BerkeleyHCI/PolymorphicBlocks/docs/blinky_kicad.png

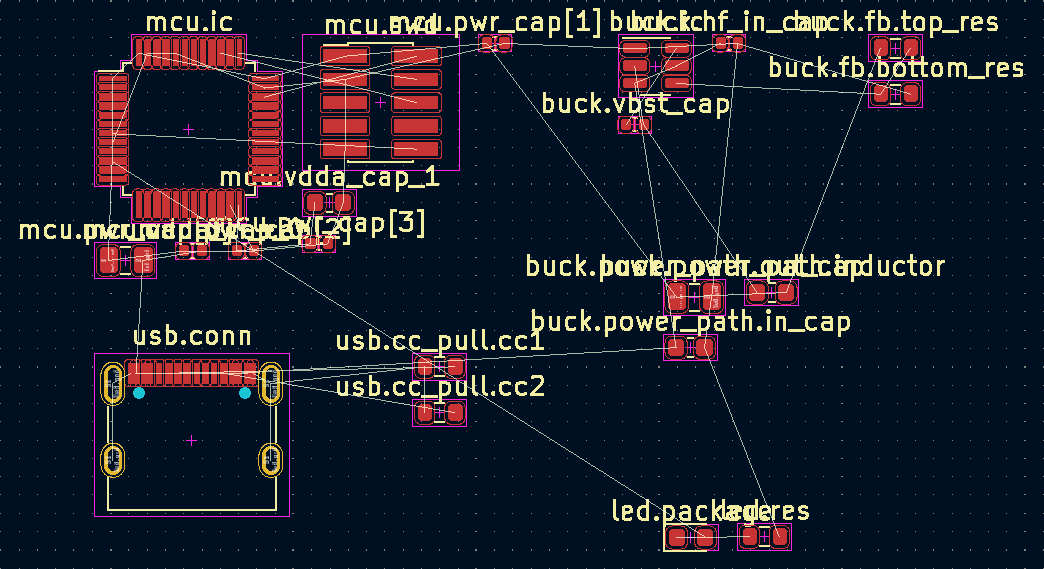
docs/blinky_kicad.png
