BerkeleyHCI/PolymorphicBlocks/docs/boards/iotfandriver.webp

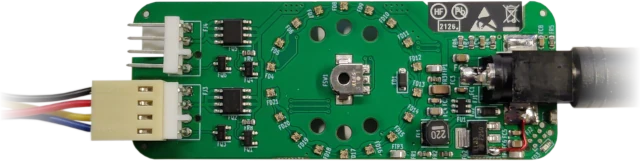
docs/boards/iotfandriver.webp
