BerkeleyHCI/PolymorphicBlocks/docs/boards/macropad_full.jpg

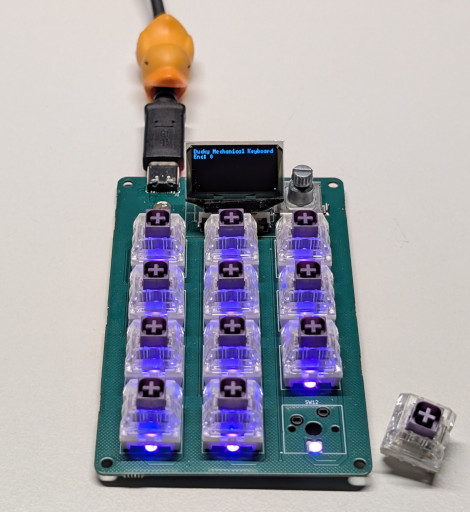
docs/boards/macropad_full.jpg
