BerkeleyHCI/PolymorphicBlocks/docs/chain.png

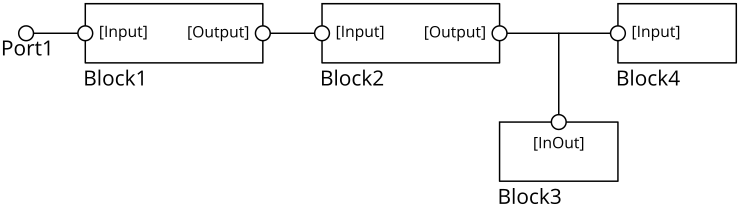
docs/chain.png
