BerkeleyHCI/PolymorphicBlocks/docs/ide/ide_blinky_buck.png

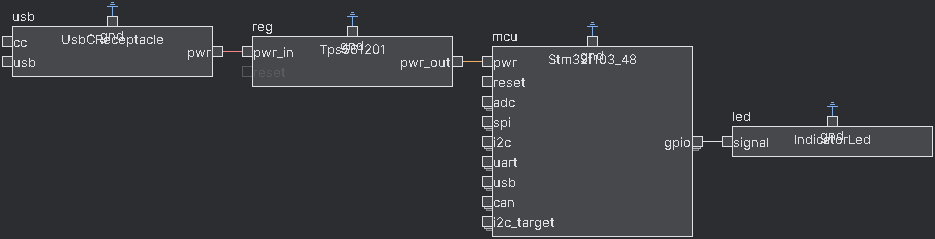
docs/ide/ide_blinky_buck.png
