BerkeleyHCI/PolymorphicBlocks/docs/ide/ide_blinky_connectpower.png

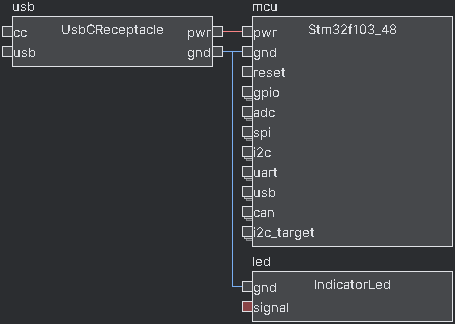
docs/ide/ide_blinky_connectpower.png
