BerkeleyHCI/PolymorphicBlocks/docs/ide/ide_blinky_errors.png

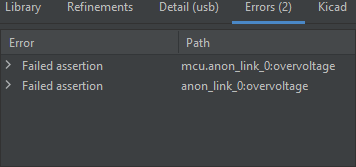
docs/ide/ide_blinky_errors.png
