BerkeleyHCI/PolymorphicBlocks/docs/ide/ide_blinky_inspect.png

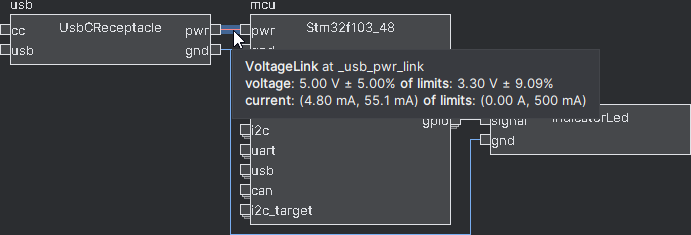
docs/ide/ide_blinky_inspect.png
