BerkeleyHCI/PolymorphicBlocks/docs/ide/ide_buck_fb.png

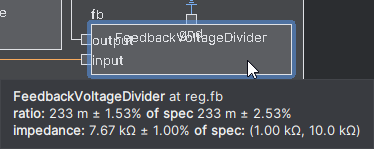
docs/ide/ide_buck_fb.png
