BerkeleyHCI/PolymorphicBlocks/docs/ide/ide_connect_mcu_start.png

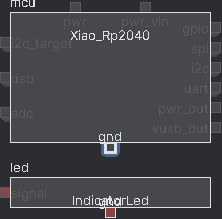
docs/ide/ide_connect_mcu_start.png
