BerkeleyHCI/PolymorphicBlocks/docs/ide/ide_connect_usbc.png

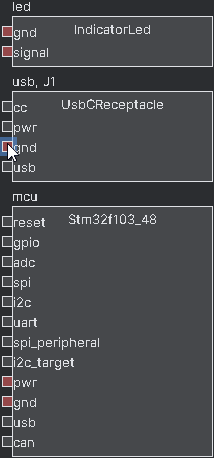
docs/ide/ide_connect_usbc.png
