BerkeleyHCI/PolymorphicBlocks/docs/ide/ide_connect_usbc_all.png

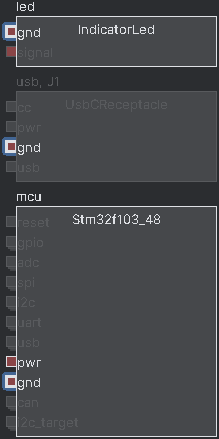
docs/ide/ide_connect_usbc_all.png
