BerkeleyHCI/PolymorphicBlocks/docs/ide/ide_insert_block.png

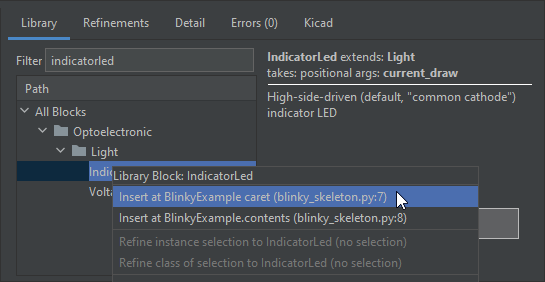
docs/ide/ide_insert_block.png
