BerkeleyHCI/PolymorphicBlocks/docs/ide/ide_kicad_magsense.png

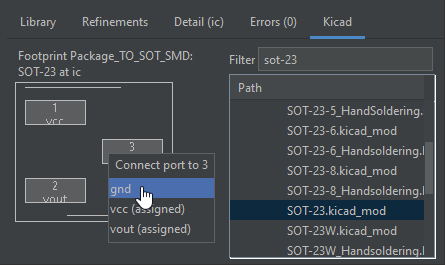
docs/ide/ide_kicad_magsense.png
