BerkeleyHCI/PolymorphicBlocks/docs/ide/ide_ledarray.png

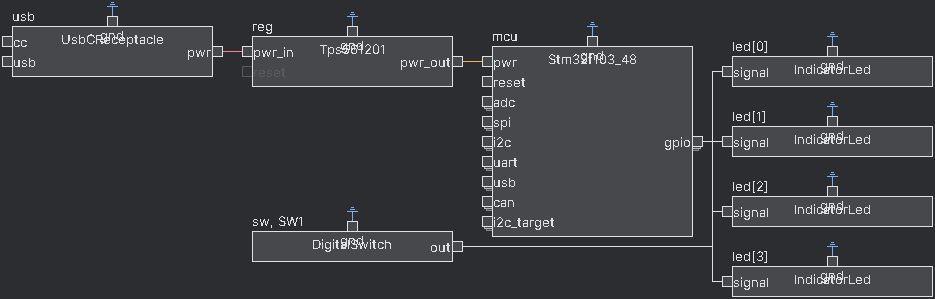
docs/ide/ide_ledarray.png
