BerkeleyHCI/PolymorphicBlocks/docs/ide/ide_library_usbc.png

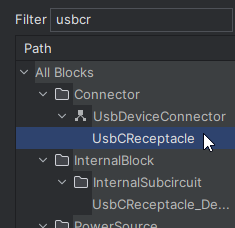
docs/ide/ide_library_usbc.png
