BerkeleyHCI/PolymorphicBlocks/docs/keyboard.png

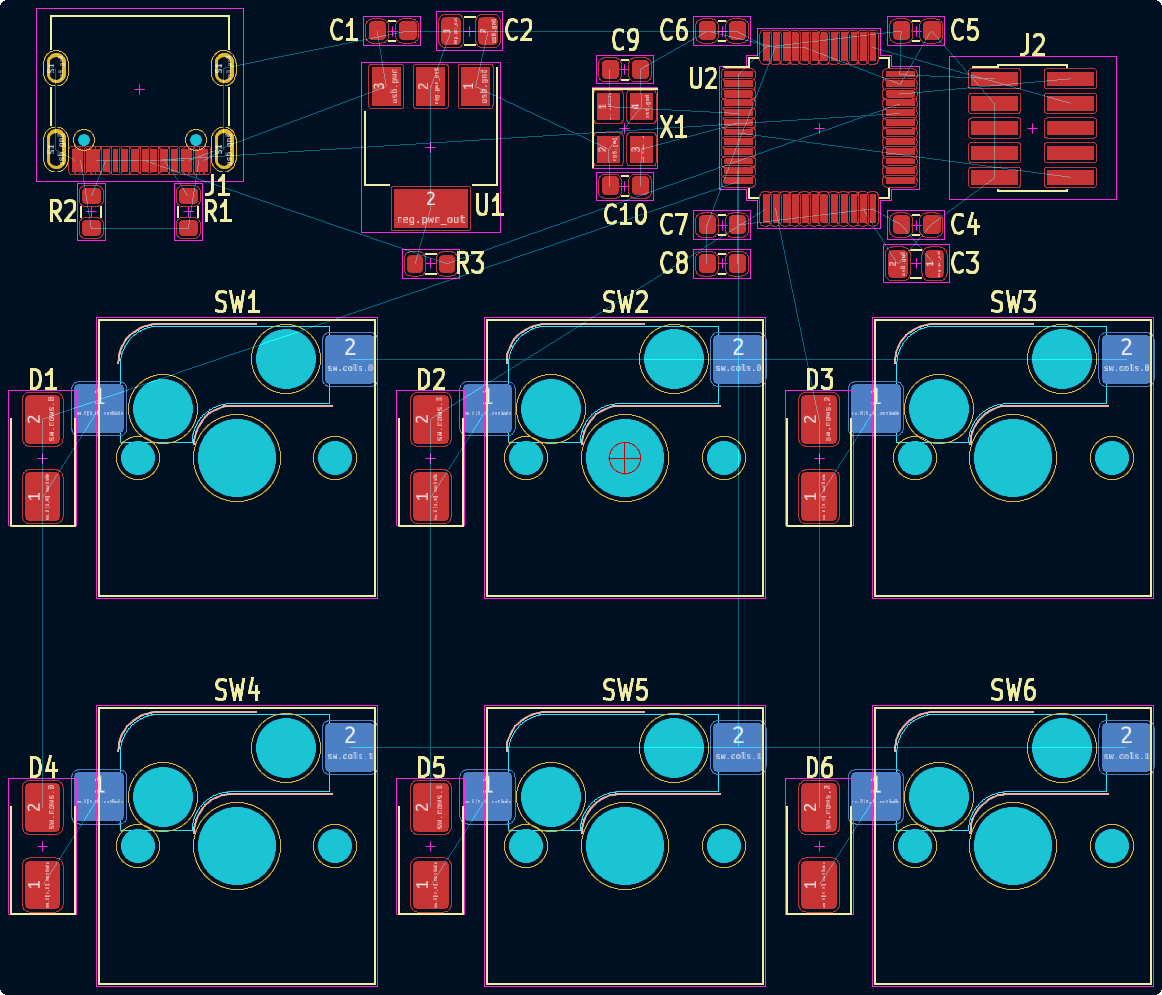
docs/keyboard.png
