BerkeleyHCI/PolymorphicBlocks/docs/packed_kicad.png

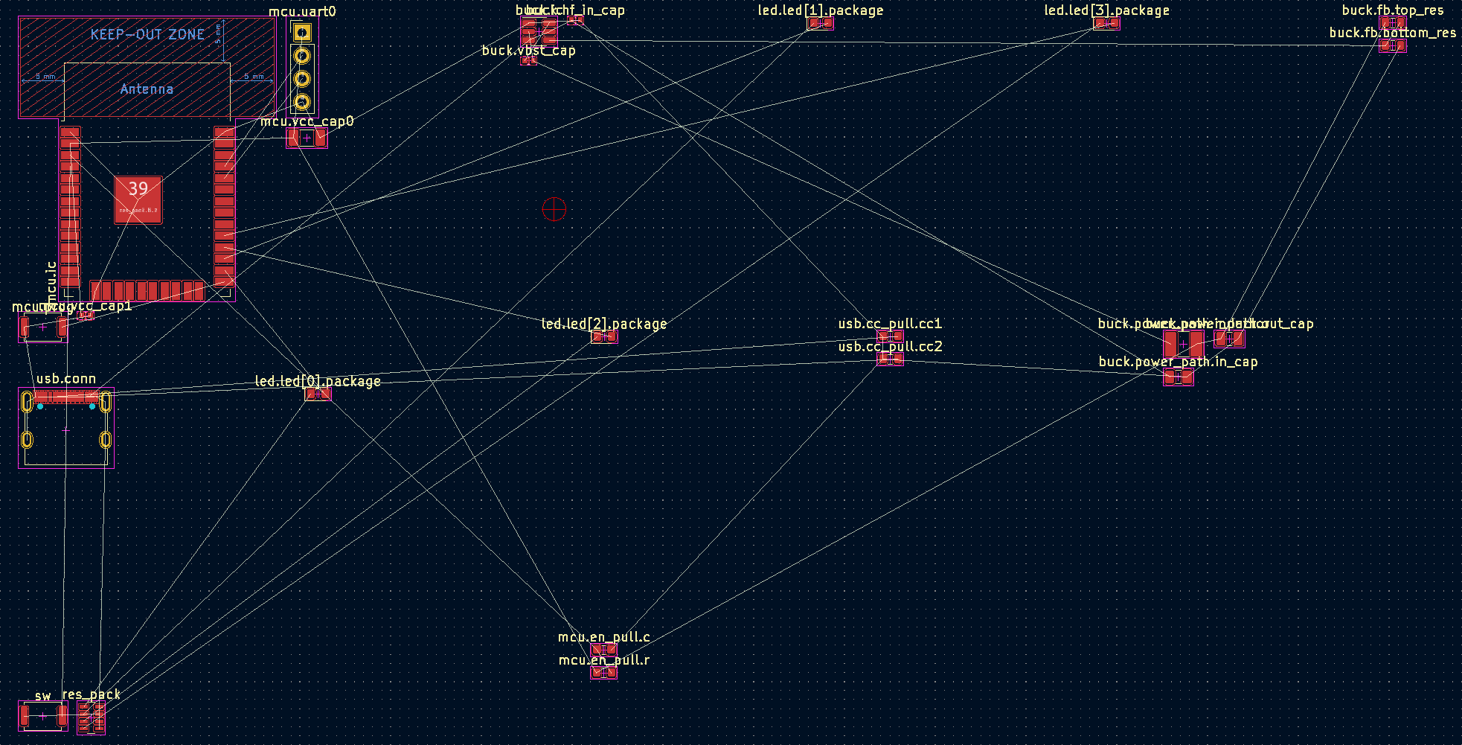
docs/packed_kicad.png
