BerkeleyHCI/PolymorphicBlocks/examples/UsbSourceMeasure/analysis/power_stage.asc

B1: bv; V = V(verr)*V(sel) + V(voff)*(1-V(sel))
C1: cap; 470p
C2: cap; 33n
C3: cap; 100µ
C4: cap; 6.8n
D1: diode; 1N4148
D2: schottky; 1N5817
D3: diode; 1N4148
D4: schottky; 1N5817
D5: diode; 1N4148
D6: diode; 1N4148
Ii: current; AC {u(prb)}
M3: pmos; RSJ250P10
M4: nmos; IRLH5030
R1: res; 45
R2: res; 0
R3: res; 0
R4: res; 10k
R5: res; 10k
R6: res; 47k
R7: res; 20k
R8: res; 1k
R9: res; 10k
R10: res; 10k
R11: res; 50k
R12: res; 4.7k
R13: res; 10k
R14: res; 10k
R15: res; 10k
R16: res; 240k
R17: res; 240k
R18: res; 10k
R19: res; 50k
R20: res; 10k
R21: res; 10k
R22: res; 1k
R23: res; 4.7k
R24: res; 10k
R25: res; 200k
R26: res; 200k
R27: res; 10k
R28: res; 10k
R29: res; 10k
R30: res; 100
R31: res; 100
R32: res; 4.7k
R33: res; 4.7k
R35: res; 150
Rload2: res; 40
Rsen: res; 1
U1: UniversalOpAmp3b; Avol=1Meg GBW=4.5Meg Slew=20Meg; Ilimit=75m Rail=0 Vos=0 Phimargin=60
U2: UniversalOpAmp3b; Avol=1Meg GBW=4.5Meg Slew=20Meg; Ilimit=75m Rail=0 Vos=0 Phimargin=60
U3: UniversalOpAmp3b; Avol=1Meg GBW=4.5Meg Slew=20Meg; Ilimit=75m Rail=0 Vos=0 Phimargin=60
U4: UniversalOpAmp3b; Avol=1Meg GBW=4.5Meg Slew=20Meg; Ilimit=75m Rail=0 Vos=0 Phimargin=60
U5: UniversalOpAmp3b; Avol=1Meg GBW=4.5Meg Slew=20Meg; Ilimit=75m Rail=0 Vos=0 Phimargin=60
U7: UniversalOpAmp3a; Avol=1Meg GBW=500k Slew=1Meg; Ilimit=25m Rail=0 Vos=0 Phimargin=60
U8: UniversalOpAmp3a; Avol=1Meg GBW=500k Slew=1Meg; Ilimit=25m Rail=0 Vos=0 Phimargin=60
U9: UniversalOpAmp3a; Avol=300Meg GBW=14Meg Slew=20Meg; Ilimit=25m Rail=0 Vos=0 Phimargin=60
V1: voltage; 20
V2: voltage; 3.3
V3: voltage; 1
V4: voltage; 3.3
V5: voltage; 1.65
V6: voltage; -.2
V7: voltage; 0
V8: voltage; PULSE(0 1 500u 1n)
V10: voltage; -1
Vi: voltage; AC {u(-prb)}
Named nets: +V, -V, 0, out, vsig, +Vdd, +Vref, vsen, -Vdd, isen, i+sig, i-sig, vint, drive, gate, x, voff, sel, verr
Driver Amplifier
(HV opamp)
Driver
Voltage Control
Error
Integrator
Source Control
1/24 V/V differential voltage sense
(re-centering 0V -> +Vref, HV opamp)
Voltage Rails
Voltage Sense
Current sense (5V/V)
(HV opamp)
Current Sense
Off-state feedback
.step param prb list -1 1
.ac dec 10 1k 1Meg
;.param prb=1
;.tran 3ms uic
; This uses the Tian method for loop gain / phase analysis,
; see LTSpice examples/Educational/LoopGain2.asc
.func T() -1/(1-1/(2*(I(Vi)@1*V(x)@2-V(x)@1*I(Vi)@2)+V(x)@1+I(Vi)@2))
TODO: the 4.7k output resistance couples into Rin of the compensator
increasing gain by 2x, which is compensated with the lower gain here
