BerkeleyHCI/PolymorphicBlocks/examples/UsbSourceMeasure/analysis/JfetProtect.asc

D1: diode; 1N4148
J1: njf; J112
J2: njf; J112
R1: res; 100
V1: voltage; 3.3
V2: voltage; PULSE(0 30 .01 0.001 0.001 0.1 0.2)
V3: voltage; SINE(15 30 10)
Named nets: 0, O
.tran 1
;.tf V(O) V2
