BerkeleyHCI/PolymorphicBlocks/examples/Fcml/analysis/fcml_power_stage.asc

B1: bv; V=V(G3A)-V(S3A) < 0.5
B3: bv; V=V(G1A)-V(S1A) < 0.5
B4: bv; V=V(G2A)-V(S2A) < 0.5
C1: cap; {Cb}
C2: cap; {Cf}
C3: cap; 15µ
C4: cap; {Cb}
C5: cap; {Cb}
C6: cap; {Cb}
C7: cap; {Cb}
C8: cap; {Cf}
D1: diode
D2: diode
D3: diode
D4: diode; md
D5: diode; md
D6: diode; md
D7: diode; md
D8: diode
D9: diode
D10: diode; md
D11: diode; md
L1: ind; 10µ
M1: nmos; fet
M2: nmos; fet
M3: nmos; fet
M4: nmos; fet
M5: nmos; fet
M6: nmos; fet
R1: res; 10
V1: voltage; PULSE(1 0 0 .01u .01u 0.5u 1u)
V2: voltage; 5
V3: voltage; PULSE(1 0 0.333u .01u .01u 0.5u 1u)
V4: voltage; 6
V5: voltage; PULSE(1 0 0.666u .01u .01u 0.5u 1u)
Named nets: 0, G1A, G2A, S1A, S2A, S1B, G1B, S2B, G2B, out, sw, B2A, B2B, B1B, G3A, S3A, G3B, S3B, B3A, B3B
.tran 0 1000u 0u
.model fet VDMOS(Rd=3m Rs=3m Vto=0.5 Kp=60 Cgdmax=1.9n Cgdmin=50p Cgs=3.1n Cjo=1n Is=5.5p Rb=5.7m)
.param Cf=7u Cb=0.1u
.model md D(Ron=.01 Roff=1Meg Vfwd=1.5)
.model d D(Ron=.01 Roff=1Meg Vfwd=0.5)
