BerkeleyHCI/PolymorphicBlocks/examples/Multimeter/analysis/ohms_source.asc

D1: diode; 1N914
Q1: npn; 2N3904
Q2: pnp; 2N3906
R1: res; 1k
R2: res; 1k
R3: res; 1k
R4: res; 1
U1: AD8030
U2: AD8030
V1: voltage; -100
V2: voltage; 10
V3: voltage; 4
Named nets: 0, +V, Vref
.tran 10m
