BerkeleyHCI/PolymorphicBlocks/examples/Datalogger/analysis/opamp_mosfet_constant_current.asc

C1: cap; .33; IC=0
M1: pmos; AO6407
R1: res; .5
R4: res; .1
U1: AD8605
V1: voltage; 5
V2: voltage; 1
Named nets: 0
.tran 0 5 0 .05
