BerkeleyHCI/PolymorphicBlocks/edg/circuits/resources/RampLimiter.asc

C1: cap; 470n
C2: cap; 10n
C3: cap; 200µ
M1: pmos; AO6407
M2: nmos; AO6408
R1: res; 200k
R2: res; 200k
R3: res; 1000
V1: voltage; PULSE(0 12 0 0.000001 0 1)
V2: voltage; PULSE(0 8 0.050 .000001 0 1)
V3: voltage; PULSE(3.3 0 .01 .000001 .000001 .045)
Named nets: 0, Vout, Vin, Vg
.tran .1
