BerkeleyHCI/PolymorphicBlocks/examples/CanAdapter/CanAdapter.kicad_pcb

## KiCad design examples/CanAdapter/CanAdapter.kicad_pcb (2025-07-09)

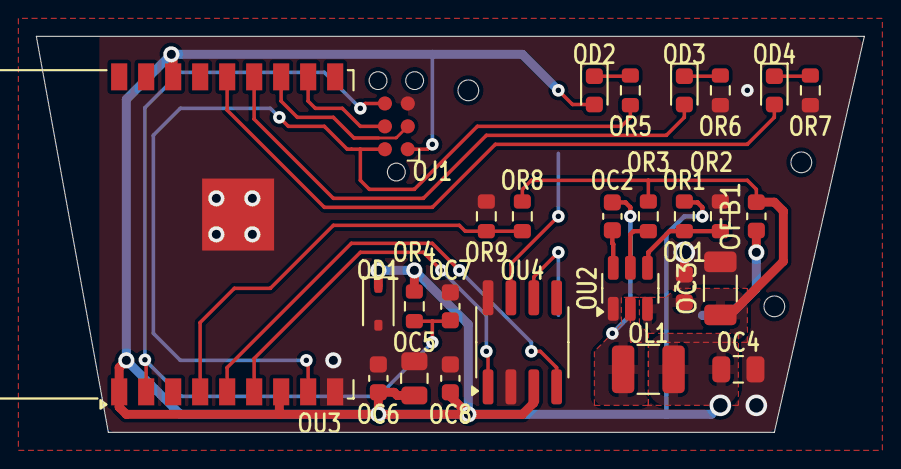
[picture p85: board CanAdapter.kicad_pcb from above]

Board: 2 copper layers, 46.0 x 22.0 mm, 31 parts (1 on the bottom side), 22 nets.

Parts:
OC1: reg_3v3.hf_in_cap; C_0603_1608Metric
OC2: reg_3v3.boot_cap; C_0603_1608Metric
OC3: reg_3v3.power_path.in_cap; C_1206_3216Metric
OC4: reg_3v3.power_path.out_cap; C_0805_2012Metric
OC5: mcu.vcc_cap0; C_0805_2012Metric
OC6: mcu.vcc_cap1; C_0603_1608Metric
OC7: mcu.en_pull.c; C_0603_1608Metric
OC8: can.vdd_cap; C_0603_1608Metric
OD1: prot_3v3; D_SOD-323
OD2: ledr.package; LED_0603_1608Metric
OD3: ledg.package; LED_0603_1608Metric
OD4: ledw.package; LED_0603_1608Metric
OFB1: ferrite; L_0603_1608Metric
OH1: jlc_th.th1; JlcToolingHole_1.152mm
OH2: jlc_th.th2; JlcToolingHole_1.152mm
OH3: jlc_th.th3; JlcToolingHole_1.152mm
OJ1: mcu.prog; Tag-Connect_TC2030-IDC-NL_2x03_P1.27mm_Vertical
OL1: reg_3v3.power_path.inductor; L_1210_3225Metric
OR1: reg_3v3.fb.top_res; R_0603_1608Metric
OR2: reg_3v3.fb.bottom_res; R_0603_1608Metric
OR3: reg_3v3.en_res; R_0603_1608Metric
OR4: mcu.en_pull.r; R_0603_1608Metric
OR5: ledr.res; R_0603_1608Metric
OR6: ledg.res; R_0603_1608Metric
OR7: ledw.res; R_0603_1608Metric
OR8: vobd_sense.top_res; R_0603_1608Metric
OR9: vobd_sense.bottom_res; R_0603_1608Metric
OU1: obd; J1962
OU2: reg_3v3.ic; SOT-23-6
OU3: mcu.ic; ESP-WROOM-02
OU4: can.ic; SOIC-8_3.9x4.9mm_P1.27mm

Connections:
Ocan.can.canh: OU1.6, OU4.7
Ocan.can.canl: OU1.14, OU4.6
Ocan.controller.rxd: OU3.5, OU4.4
Ocan.controller.txd: OU3.6, OU4.1
Ognd: OC1.2, OC3.2, OC4.2, OC5.2, OC6.2, OC7.2, OC8.2, OD1.2, OJ1.5, OR2.2, OR6.2, OR7.2, OR9.2, OU1.5, OU2.1, OU3.9, OU3.19, OU4.2, OU4.8
Oledg.res.a: OD3.1, OR6.1
Oledg.signal: OD3.2, OU3.13
Oledr.res.a: OD2.1, OR5.1
Oledw.res.a: OD4.1, OR7.1
Oledw.signal: OD4.2, OU3.14
Omcu.program_boot_node: OJ1.2, OR5.2, OU3.8
Omcu.program_en_node: OC7.1, OJ1.6, OR4.2, OU3.2
Omcu.program_uart_node.a_tx: OJ1.3, OU3.12
Omcu.program_uart_node.b_tx: OJ1.4, OU3.11
Oobd.pwr: OFB1.1, OU1.16
Oreg_3v3.boot_cap.neg: OC2.2, OL1.1, OU2.2
Oreg_3v3.boot_cap.pos: OC2.1, OU2.6
Oreg_3v3.en_res.b: OR3.2, OU2.5
Oreg_3v3.fb.output: OR1.2, OR2.1, OU2.4
Ov3v3: OC4.1, OC5.1, OC6.1, OC8.1, OD1.1, OD2.2, OJ1.1, OL1.2, OR1.1, OR4.1, OU3.1, OU3.7, OU3.16, OU4.3
Ovobd: OC1.1, OC3.1, OFB1.2, OR3.1, OR8.1, OU2.3
Ovobd_sense.output: OR8.2, OR9.1, OU3.4
