BerkeleyHCI/PolymorphicBlocks/examples/IotRollerBlinds/IotRollerBlinds.kicad_pcb

## KiCad design examples/IotRollerBlinds/IotRollerBlinds.kicad_pcb (2025-07-09)

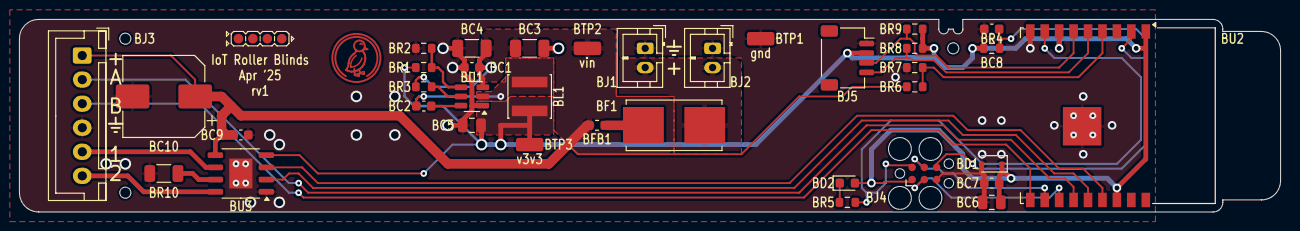
[picture p86: board IotRollerBlinds.kicad_pcb from above]

Board: 2 copper layers, 131.0 x 20.0 mm, 40 parts (0 on the bottom side), 24 nets.

Parts:
BC1: reg_3v3.hf_in_cap; C_0603_1608Metric
BC2: reg_3v3.boot_cap; C_0603_1608Metric
BC3: reg_3v3.power_path.in_cap.c[0]; C_1206_3216Metric
BC4: reg_3v3.power_path.in_cap.c[1]; C_1206_3216Metric
BC5: reg_3v3.power_path.out_cap; C_0805_2012Metric
BC6: mcu.vcc_cap0; C_0805_2012Metric
BC7: mcu.vcc_cap1; C_0603_1608Metric
BC8: mcu.en_pull.c; C_0603_1608Metric
BC9: drv.vm_cap0; C_0603_1608Metric
BC10: drv.vm_cap1; CP_Elec_8x10
BD1: prot_3v3; D_SOD-323
BD2: ledr.package; LED_0603_1608Metric
BF1: fuse; Fuseholder_Littelfuse_Nano2_154x
BFB1: ferrite; L_0603_1608Metric
BH1: jlc_th.th1; JlcToolingHole_1.152mm
BH2: jlc_th.th2; JlcToolingHole_1.152mm
BH3: jlc_th.th3; JlcToolingHole_1.152mm
BJ1: pwr; JST_PH_B2B-PH-K_1x02_P2.00mm_Vertical
BJ2: pwr_out; JST_PH_B2B-PH-K_1x02_P2.00mm_Vertical
BJ3: conn; JST_XH_B6B-XH-A_1x06_P2.50mm_Vertical
BJ4: mcu.prog; Tag-Connect_TC2030-IDC-FP_2x03_P1.27mm_Vertical
BJ5: qwiic; JST_SH_SM04B-SRSS-TB_1x04-1MP_P1.00mm_Horizontal
BL1: reg_3v3.power_path.inductor; L_Sunlord_SWPA4030S
BR1: reg_3v3.fb.top_res; R_0603_1608Metric
BR2: reg_3v3.fb.bottom_res; R_0603_1608Metric
BR3: reg_3v3.en_res; R_0603_1608Metric
BR4: mcu.en_pull.r; R_0603_1608Metric
BR5: ledr.res; R_0603_1608Metric
BR6: vin_sense.top_res; R_0603_1608Metric
BR7: vin_sense.bottom_res; R_0603_1608Metric
BR8: qwiic_pull.scl_res; R_0603_1608Metric
BR9: qwiic_pull.sda_res; R_0603_1608Metric
BR10: drv.isen_res; R_1206_3216Metric
BTP1: gnd; TestPoint_TE_RCT_0805
BTP2: vin; TestPoint_TE_RCT_0805
BTP3: v3v3; TestPoint_TE_RCT_0805
BU1: reg_3v3.ic; SOT-23-6
BU2: mcu.ic; ESP-WROOM-02
BU3: drv.ic; HSOP-8-1EP_3.9x4.9mm_P1.27mm_EP2.41x3.1mm
duck: G***; Symbol_Duckling

Connections:
Bconn.enca: BJ3.2, BU2.13
Bconn.encb: BJ3.3, BU2.10
Bdrv.ic.isen: BR10.2, BU3.7
Bdrv.in1: BU2.15, BU3.3
Bdrv.in2: BU2.14, BU3.2
Bdrv.out1: BJ3.5, BU3.6
Bdrv.out2: BJ3.6, BU3.8
Bfuse.pwr_out: BF1.2, BFB1.1
Bgnd: BC1.2, BC3.2, BC4.2, BC5.2, BC6.2, BC7.2, BC8.2, BC9.2, BC10.2, BD1.2, BJ1.1, BJ2.1, BJ3.4, BJ4.5, BJ5.1, BR2.2, BR7.2, BR10.1, BTP1.1, BU1.1, BU2.9, BU2.19, BU3.1, BU3.9
Bledr.res.a: BD2.1, BR5.1
Bmcu.program_boot_node: BJ4.2, BR5.2, BU2.8
Bmcu.program_en_node: BC8.1, BJ4.6, BR4.2, BU2.2
Bmcu.program_uart_node.a_tx: BJ4.3, BU2.12
Bmcu.program_uart_node.b_tx: BJ4.4, BU2.11
Bqwiic_pull.i2c.scl: BJ5.4, BR8.2, BU2.5
Bqwiic_pull.i2c.sda: BJ5.3, BR9.2, BU2.6
Breg_3v3.boot_cap.neg: BC2.2, BL1.1, BU1.2
Breg_3v3.boot_cap.pos: BC2.1, BU1.6
Breg_3v3.en_res.b: BR3.2, BU1.5
Breg_3v3.fb.output: BR1.2, BR2.1, BU1.4
Bv3v3: BC5.1, BC6.1, BC7.1, BD1.1, BD2.2, BJ4.1, BJ5.2, BL1.2, BR1.1, BR4.1, BR8.1, BR9.1, BTP3.1, BU2.1, BU2.7, BU2.16, BU3.4
Bvin: BC1.1, BC3.1, BC4.1, BC9.1, BC10.1, BFB1.2, BJ3.1, BR3.1, BR6.1, BTP2.1, BU1.3, BU3.5
Bvin_raw: BF1.1, BJ1.2, BJ2.2
Bvin_sense.output: BR6.2, BR7.1, BU2.4
