BerkeleyHCI/PolymorphicBlocks/examples/IotCurtainCrawler/IotCurtainCrawler.kicad_pcb

## KiCad design examples/IotCurtainCrawler/IotCurtainCrawler.kicad_pcb (2025-07-09)

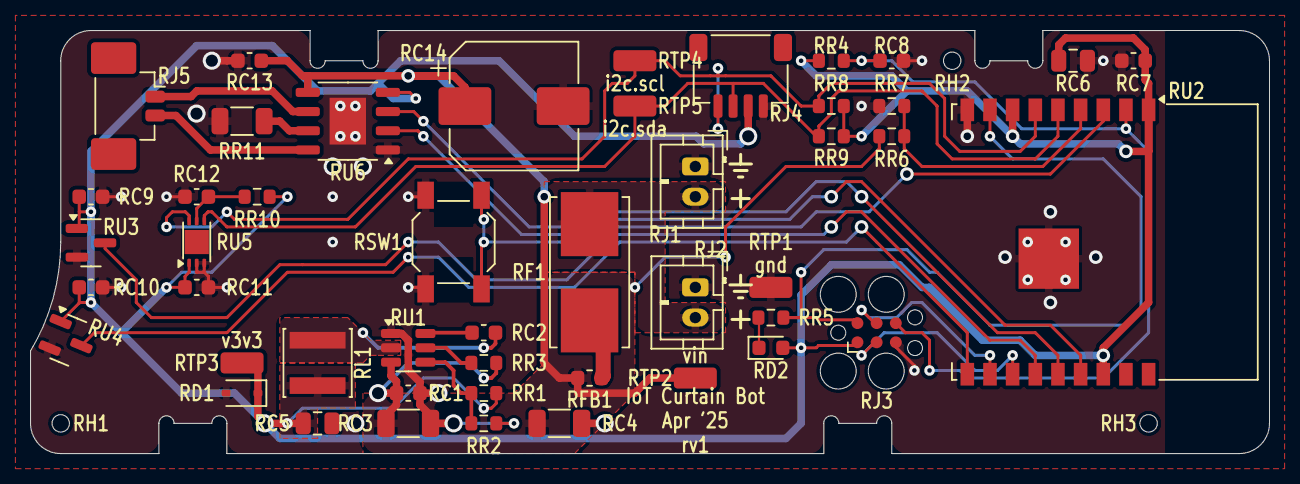
[picture p87: board IotCurtainCrawler.kicad_pcb from above]

Board: 2 copper layers, 82.0 x 28.0 mm, 50 parts (0 on the bottom side), 26 nets.

Parts:
RC1: reg_3v3.hf_in_cap; C_0603_1608Metric
RC2: reg_3v3.boot_cap; C_0603_1608Metric
RC3: reg_3v3.power_path.in_cap.c[0]; C_1206_3216Metric
RC4: reg_3v3.power_path.in_cap.c[1]; C_1206_3216Metric
RC5: reg_3v3.power_path.out_cap; C_0805_2012Metric
RC6: mcu.vcc_cap0; C_0805_2012Metric
RC7: mcu.vcc_cap1; C_0603_1608Metric
RC8: mcu.en_pull.c; C_0603_1608Metric
RC9: enca.cin; C_0603_1608Metric
RC10: encb.cin; C_0603_1608Metric
RC11: als.vcc_cap; C_0603_1608Metric
RC12: als.dvi_cap; C_0603_1608Metric
RC13: drv.vm_cap0; C_0603_1608Metric
RC14: drv.vm_cap1; CP_Elec_8x10
RD1: prot_3v3; D_SOD-323
RD2: ledr.package; LED_0603_1608Metric
RF1: fuse; Fuseholder_Littelfuse_Nano2_154x
RFB1: ferrite; L_0603_1608Metric
RH1: jlc_th.th1; JlcToolingHole_1.152mm
RH2: jlc_th.th2; JlcToolingHole_1.152mm
RH3: jlc_th.th3; JlcToolingHole_1.152mm
RJ1: pwr; JST_PH_B2B-PH-K_1x02_P2.00mm_Vertical
RJ2: pwr_out; JST_PH_B2B-PH-K_1x02_P2.00mm_Vertical
RJ3: mcu.prog; Tag-Connect_TC2030-IDC-FP_2x03_P1.27mm_Vertical
RJ4: qwiic; JST_SH_SM04B-SRSS-TB_1x04-1MP_P1.00mm_Horizontal
RJ5: motor; Molex_PicoBlade_53398-0271_1x02-1MP_P1.25mm_Vertical
RL1: reg_3v3.power_path.inductor; L_Sunlord_SWPA4030S
RR1: reg_3v3.fb.top_res; R_0603_1608Metric
RR2: reg_3v3.fb.bottom_res; R_0603_1608Metric
RR3: reg_3v3.en_res; R_0603_1608Metric
RR4: mcu.en_pull.r; R_0603_1608Metric
RR5: ledr.res; R_0603_1608Metric
RR6: vin_sense.top_res; R_0603_1608Metric
RR7: vin_sense.bottom_res; R_0603_1608Metric
RR8: i2c_pull.scl_res; R_0603_1608Metric
RR9: i2c_pull.sda_res; R_0603_1608Metric
RR10: als.dvi_res; R_0603_1608Metric
RR11: drv.isen_res; R_1206_3216Metric
RSW1: sw; SW_SPST_SKQG_WithoutStem
RTP1: gnd; TestPoint_TE_RCT_0805
RTP2: vin; TestPoint_TE_RCT_0805
RTP3: v3v3; TestPoint_TE_RCT_0805
RTP4: i2c.scl; TestPoint_TE_RCT_0805
RTP5: i2c.sda; TestPoint_TE_RCT_0805
RU1: reg_3v3.ic; SOT-23-6
RU2: mcu.ic; ESP-WROOM-02
RU3: enca.ic; SOT-23
RU4: encb.ic; SOT-23
RU5: als.ic; HVSOF6
RU6: drv.ic; HSOP-8-1EP_3.9x4.9mm_P1.27mm_EP2.41x3.1mm

Connections:
Rals.dvi_res.b: RC12.1, RR10.2, RU5.5
Rdrv.ic.isen: RR11.2, RU6.7
Rdrv.in1: RU2.14, RU6.3
Rdrv.in2: RU2.15, RU6.2
Rdrv.out1: RJ5.1, RU6.6
Rdrv.out2: RJ5.2, RU6.8
Renca.out: RU2.13, RU3.3
Rencb.out: RU2.10, RU4.3
Rfuse.pwr_out: RF1.2, RFB1.1
Rgnd: RC1.2, RC3.2, RC4.2, RC5.2, RC6.2, RC7.2, RC8.2, RC9.2, RC10.2, RC11.2, RC12.2, RC13.2, RC14.2, RD1.2, RJ1.1, RJ2.1, RJ3.5, RJ4.1, RR2.2, RR7.2, RR11.1, RSW1.2, RTP1.1, RU1.1, RU2.9, RU2.19, RU3.2, RU4.2, RU5.2, RU5.3, RU6.1, RU6.9
Ri2c_chain_0.scl: RJ4.4, RR8.2, RTP4.1, RU2.6, RU5.6
Ri2c_chain_0.sda: RJ4.3, RR9.2, RTP5.1, RU2.5, RU5.4
Rledr.res.a: RD2.1, RR5.1
Rmcu.program_boot_node: RJ3.2, RR5.2, RU2.8
Rmcu.program_en_node: RC8.1, RJ3.6, RR4.2, RU2.2
Rmcu.program_uart_node.a_tx: RJ3.3, RU2.12
Rmcu.program_uart_node.b_tx: RJ3.4, RU2.11
Rreg_3v3.boot_cap.neg: RC2.2, RL1.1, RU1.2
Rreg_3v3.boot_cap.pos: RC2.1, RU1.6
Rreg_3v3.en_res.b: RR3.2, RU1.5
Rreg_3v3.fb.output: RR1.2, RR2.1, RU1.4
Rsw.out: RSW1.1, RU2.3
Rv3v3: RC5.1, RC6.1, RC7.1, RC9.1, RC10.1, RC11.1, RD1.1, RD2.2, RJ3.1, RJ4.2, RL1.2, RR1.1, RR4.1, RR8.1, RR9.1, RR10.1, RTP3.1, RU2.1, RU2.7, RU2.16, RU3.1, RU4.1, RU5.1, RU6.4
Rvin: RC1.1, RC3.1, RC4.1, RC13.1, RC14.1, RFB1.2, RR3.1, RR6.1, RTP2.1, RU1.3, RU6.5
Rvin_raw: RF1.1, RJ1.2, RJ2.2
Rvin_sense.output: RR6.2, RR7.1, RU2.4
