BerkeleyHCI/PolymorphicBlocks/examples/EspLora/EspLora.kicad_pcb

## KiCad design examples/EspLora/EspLora.kicad_pcb (2024-10-19)

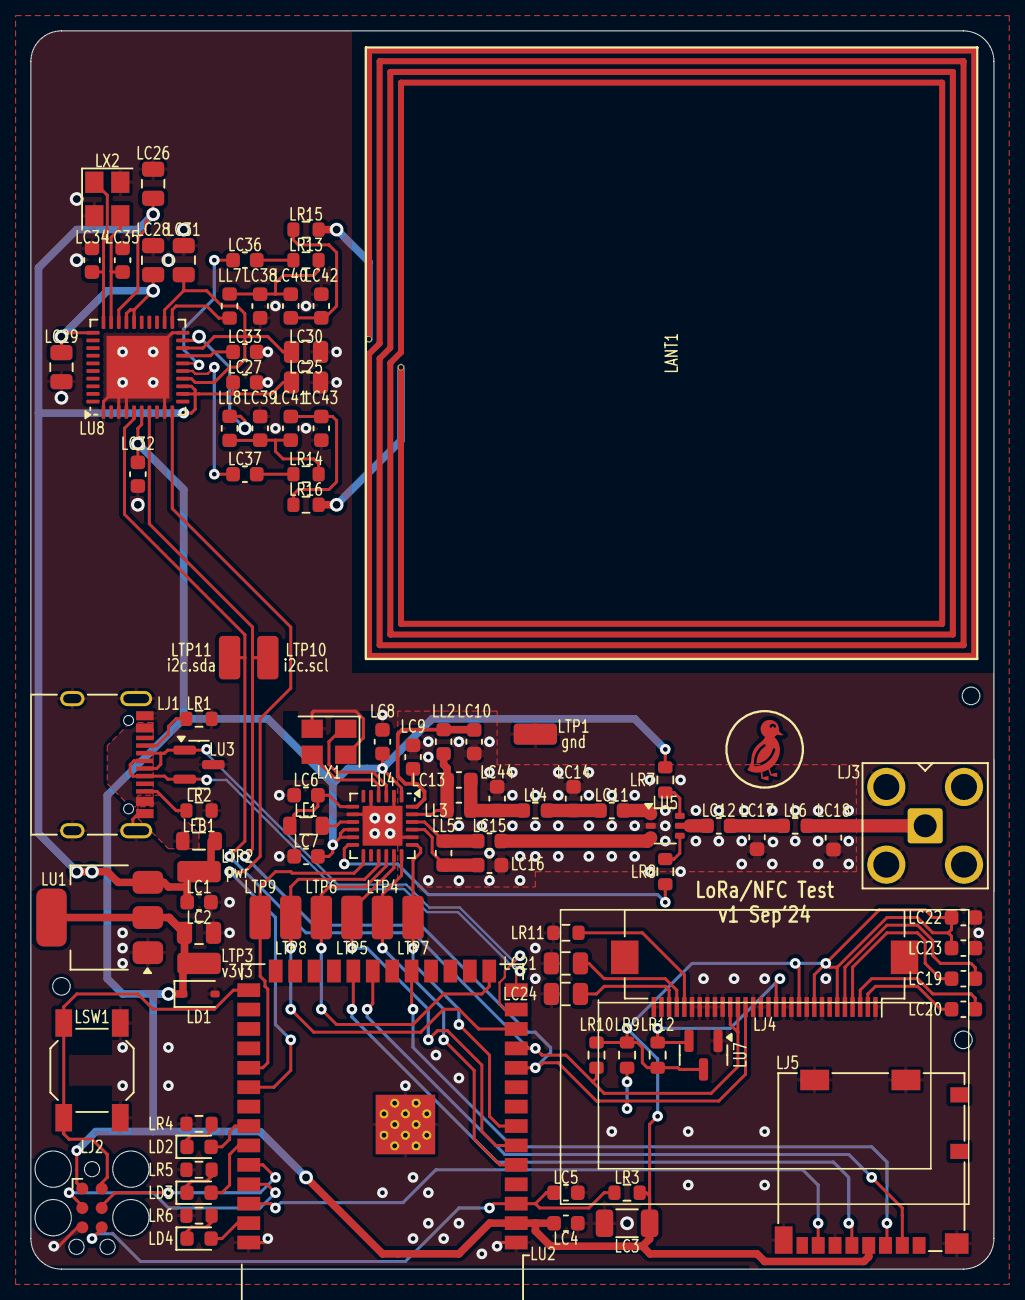
[picture p88: board EspLora.kicad_pcb from above]

Board: 2 copper layers, 63.0 x 81.0 mm, 105 parts (0 on the bottom side), 74 nets.

Parts:
LANT1: an13219
LC1, LC4, LC7, LC27, LC33: 50V 100nF X7R ±10% 0603 Multilayer Ceramic Capaci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; C_0603_1608Metric
LC2, LC21, LC25, LC26: 25V 4.7uF X5R ±10% 0805 Multilayer Ceramic Capaci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; C_0805_2012Metric
LC3: 25V 22uF X5R ±10% 1206 Multilayer Ceramic Capacit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; C_1206_3216Metric
LC5, LC8, LC19, LC20, LC22, LC23, LC32: 50V 1uF X5R ±10% 0603 Multilayer Ceramic Capacito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; C_0603_1608Metric
LC6: 25V 470nF X7R ±10% 0603 Multilayer Ceramic Capaci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; C_0603_1608Metric
LC9, LC11, LC12, LC42, LC43: 50V 47pF C0G ±5% 0603 Multilayer Ceramic Capacito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; C_0603_1608Metric
LC10: 50V 47nF X7R ±10% 0603 Multilayer Ceramic Capacit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; C_0603_1608Metric
LC13: 250V 2.2pF NP0 ±5% 0603 Multilayer Ceramic Capaci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; C_0603_1608Metric
LC14, LC15, LC16, LC17, LC18: 250V 3pF C0G ±5% 0603 Multilayer Ceramic Capacito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; C_0603_1608Metric
LC24: 25V 10uF X5R ±10% 0805 Multilayer Ceramic Capacit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; C_0805_2012Metric
LC28, LC29, LC30, LC31: 50V 2.2uF X5R ±10% 0805 Multilayer Ceramic Capaci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; C_0805_2012Metric
LC34, LC35, LC44: 50V 10pF C0G ±5% 0603 Multilayer Ceramic Capacito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; C_0603_1608Metric
LC36, LC37: 50V 1nF X7R ±10% 0603 Multilayer Ceramic Capacito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; C_0603_1608Metric
LC38, LC39: 50V 560pF X7R ±10% 0603 Multilayer Ceramic Capaci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; C_0603_1608Metric
LC40, LC41: 50V 150pF X7R ±10% 0603 Multilayer Ceramic Capaci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; C_0603_1608Metric
LD1: 3.6V~3.8V 200mW 3.6V SOD-323 Zener Diodes ROHS; D_SOD-323
LD2: -40?~+85? Red 0603 LED Indication - Discrete ROHS; LED_0603_1608Metric
LD3: 20mA Colorless transparent lens -40?~+85? 585.5nm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; LED_0603_1608Metric
LD4: White 0603 LED Indication - Discrete ROHS; LED_0603_1608Metric
LFB1: ±25% 100?@100MHz 0805 Ferrite Beads ROHS; L_0805_2012Metric
LH1, LH2, LH3: JlcToolingHole_1.152mm
LJ1: COM-15111; USB_C_Receptacle_XKB_U262-16XN-4BVC11
LJ2: Tag-Connect_TC2030-IDC-FP_2x03_P1.27mm_Vertical
LJ3: 901-143; SMA_Amphenol_901-143_Horizontal
LJ4: AFC01-S30FCA-00; Hirose_FH12-30S-0.5SH_1x30-1MP_P0.50mm_Horizontal
LJ5: 104031-0811; microSD_HC_Molex_104031-0811
LL1: 100mA 15uH ±20% 650m? 0805 Inductors (SMD) ROHS; L_0805_2012Metric
LL2: 200mA 47nH ±5% 1? 0603 Inductors (SMD) ROHS; L_0603_1608Metric
LL3: 700mA 3.3nH ±5% 0603 Power Inductors ROHS; L_0603_1608Metric
LL4, LL6: 500mA 8.2nH ±5% 350m? 0603 Inductors (SMD) ROHS; L_0603_1608Metric
LL5: 300mA 12nH ±5% 450m? 0603 Inductors (SMD) ROHS; L_0603_1608Metric
LL7, LL8: 900mA 220nH ±5% 200m? 0603 Inductors (SMD) ROHS; L_0603_1608Metric
LR1, LR2: 100mW Thick Film Resistors 75V ±100ppm/? ±1% 5.1k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; R_0603_1608Metric
LR3, LR12: 100mW Thick Film Resistors 75V ±100ppm/? ±1% 10k?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; R_0603_1608Metric
LR4, LR5, LR6: 100mW Thick Film Resistors 75V ±100ppm/? ±1% 820?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; R_0603_1608Metric
LR7, LR8: 100mW Thick Film Resistors 75V ±100ppm/? ±1% 1k? 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; R_0603_1608Metric
LR9, LR10: 100mW Thick Film Resistors 75V ±100ppm/? ±1% 4.7k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; R_0603_1608Metric
LR11: 100mW Thick Film Resistors 75V ±100ppm/? ±1% 470k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; R_0603_1608Metric
LR13, LR14: 100mW Thick Film Resistors 75V ±100ppm/? ±1% 2.2k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; R_0603_1608Metric
LR15, LR16: 100mW Thick Film Resistors 75V ±1% ±200ppm/? 2.49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; R_0603_1608Metric
LSW1: 5.1mm switch; SW_SPST_SKQG_WithoutStem
LTP1: gnd; TestPoint_TE_RCT_0805
LTP2: pwr; TestPoint_TE_RCT_0805
LTP3: v3v3; TestPoint_TE_RCT_0805
LTP4: lr.sck; TestPoint_TE_RCT_0805
LTP5: lr.mosi; TestPoint_TE_RCT_0805
LTP6: lr.miso; TestPoint_TE_RCT_0805
LTP7: lr_cs; TestPoint_TE_RCT_0805
LTP8: lr_rs; TestPoint_TE_RCT_0805
LTP9: lr_di; TestPoint_TE_RCT_0805
LTP10: i2c.scl; TestPoint_TE_RCT_0805
LTP11: i2c.sda; TestPoint_TE_RCT_0805
LU1: LDL1117S33R; SOT-223-3_TabPin2
LU2: ESP32-S3-WROOM-1-N16R8; ESP32-S3-WROOM-1
LU3: PESD5V0X1BT; SOT-23
LU4: SX1262IMLTRT; QFN-24-1EP_4x4mm_P0.5mm_EP2.6x2.6mm
LU5: PE4259; SOT-363_SC-70-6
LU6: ER-OLED-0.96-1.1; Lcd_Er_Oled0.96_1.1_Outline
LU7: APX803S-29SA-7; SOT-23
LU8: PN7160A1HN/C100Y; HVQFN-40-1EP_6x6mm_P0.5mm_EP4.1x4.1mm
LX1: 30MHz SMD Crystal Resonator 20pF ±10ppm ±30ppm -4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; Crystal_SMD_3225-4Pin_3.2x2.5mm
LX2: 27.12MHz SMD Crystal Resonator 10pF ±10ppm ±30ppm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; Crystal_SMD_3225-4Pin_3.2x2.5mm
svg2mod: G***; Symbol_DucklingSolid

Connections:
Lgnd: LC1.2, LC2.2, LC3.2, LC4.2, LC5.2, LC6.2, LC7.2, LC8.2, LC9.2, LC10.2, LC14.2, LC16.2, LC17.2, LC18.2, LC21.2, LC22.2, LC23.2, LC24.2, LC25.2, LC26.2, LC27.2, LC28.2, LC29.2, LC30.2, LC31.2, LC32.2, LC33.2, LC34.2, LC35.2, LC38.2, LC39.2, LC42.2, LC43.2, LC44.2, LD1.2, LJ1.A1, LJ1.A12, LJ1.B1, LJ1.B12, LJ1.S1, LJ2.5, LJ3.2, LJ4.1, LJ4.8, LJ4.10, LJ4.12, LJ4.13, LJ4.15, LJ4.16, LJ4.17, LJ4.21, LJ4.22, LJ4.23, LJ4.24, LJ4.25, LJ4.29, LJ4.30, LJ5.6, LJ5.11, LR1.1, LR2.1, LR4.2, LR5.2, LR6.2, LR11.2, LSW1.2, LTP1.1, LU1.1, LU2.1, LU2.40, LU2.41, LU3.3, LU4.2, LU4.5, LU4.8, LU4.20, LU4.25, LU5.2, LU7.1, LU8.1, LU8.3, LU8.4, LU8.9, LU8.20, LU8.41, LX1.2, LX1.4, LX2.2, LX2.4
Li2c_pull.i2c.scl: LJ4.18, LR9.2, LTP10.1, LU2.10, LU8.7
Li2c_pull.i2c.sda: LJ4.19, LJ4.20, LR10.2, LTP11.1, LU2.11, LU8.5
Lledb.res.a: LD4.1, LR6.1
Lledb.signal: LD4.2, LU2.39
Lledg.res.a: LD3.1, LR5.1
Lledg.signal: LD3.2, LU2.35
Lledr.res.a: LD2.1, LR4.1
Lledr.signal: LD2.2, LU2.34
Llora.ant_pi.output: LC18.1, LJ3.1, LL6.2
Llora.balun.input: LC15.1, LU5.3
Llora.balun.rfi_n: LC15.2, LL5.1, LU4.22
Llora.balun.rfi_p: LC16.1, LL5.2, LU4.21
Llora.dcc_l.a: LL1.1, LU4.9
Llora.ic.rfo: LC13.2, LL2.2, LL3.1, LU4.23
Llora.ic.vr_pa: LC9.1, LC10.1, LL2.1, LU4.24
Llora.ic.vreg: LC6.1, LL1.2, LU4.7
Llora.rf_sw.ctrl: LR8.1, LU4.12
Llora.rf_sw.ctrl_res.b: LR8.2, LU5.4
Llora.rf_sw.vdd_res.b: LR7.2, LU5.6
Llora.rfc_dcblock.neg: LC12.2, LU5.5
Llora.rfc_dcblock.pos: LC12.1, LC17.1, LL6.1
Llora.tx_dcblock.pos: LC11.1, LU5.1
Llora.tx_pi.output: LC11.2, LC14.1, LL4.2
Llora.xtal.crystal.xtal_in: LU4.3, LX1.1
Llora.xtal.crystal.xtal_out: LU4.4, LX1.3
Lmcu.program_boot_node: LJ2.2, LSW1.1, LU2.27
Lmcu.program_en_node: LC5.1, LJ2.6, LR3.2, LU2.3
Lmcu.program_uart_node.a_tx: LJ2.3, LU2.37
Lmcu.program_uart_node.b_tx: LJ2.4, LU2.36
Lnfc.damp.ant1: LANT1.1, LR15.2
Lnfc.damp.ant2: LANT1.2, LR16.2
Lnfc.emc.out1: LC38.1, LC40.1, LL7.2, LR13.1
Lnfc.emc.out2: LC39.1, LC41.1, LL8.2, LR14.1
Lnfc.ic.rxn: LC37.2, LU8.15
Lnfc.ic.rxp: LC36.2, LU8.16
Lnfc.ic.tx1: LL7.1, LU8.21
Lnfc.ic.tx2: LL8.1, LU8.19
Lnfc.ic.vdd: LC28.1, LC29.1, LU8.26, LU8.27, LU8.31
Lnfc.ic.vddmid: LC33.1, LU8.17
Lnfc.ic.vddtx: LC30.1, LC31.1, LU8.14, LU8.18, LU8.22
Lnfc.ic.xtal.xtal_in: LC34.1, LU8.30, LX2.1
Lnfc.ic.xtal.xtal_out: LC35.1, LU8.29, LX2.3
Lnfc.match.out1: LC40.2, LC42.1, LR15.1
Lnfc.match.out2: LC41.2, LC43.1, LR16.1
Lnfc.reset: LU2.32, LU8.10
Lnfc.rx.rrx1.b: LC36.1, LR13.2
Lnfc.rx.rrx2.b: LC37.1, LR14.2
Loled.c1_cap.neg: LC19.2, LJ4.5
Loled.c1_cap.pos: LC19.1, LJ4.4
Loled.c2_cap.neg: LC20.2, LJ4.3
Loled.c2_cap.pos: LC20.1, LJ4.2
Loled.device.vcc: LC24.1, LJ4.28
Loled.device.vcomh: LC21.1, LJ4.27
Loled.iref_res.a: LJ4.26, LR11.1
Loled_rst.nreset: LJ4.14, LR12.2, LU7.2
Lpwr: LC1.1, LC25.1, LC26.1, LC27.1, LFB1.2, LTP2.1, LU1.3, LU8.12, LU8.13, LU8.28
Lsd.cs: LJ5.2, LU2.21
Lsd.spi.miso: LJ5.7, LU2.38
Lsd.spi.mosi: LJ5.3, LU2.19
Lsd.spi.sck: LJ5.5, LU2.22
Ltp_lora_cs.io: LTP7.1, LU2.7, LU4.19
Ltp_lora_dio.io: LTP9.1, LU2.31, LU4.13
Ltp_lora_rst.io: LTP8.1, LU2.12, LU4.15
Ltp_lora_spi.io.miso: LTP6.1, LU2.15, LU4.16
Ltp_lora_spi.io.mosi: LTP5.1, LU2.6, LU4.17
Ltp_lora_spi.io.sck: LTP4.1, LU2.5, LU4.18
Ltx_cpack.pos.0: LC13.1, LC44.1, LL3.2, LL4.1
Lusb.conn.cc.cc1: LJ1.A5, LR1.2
Lusb.conn.cc.cc2: LJ1.B5, LR2.2
Lusb.pwr: LFB1.1, LJ1.A4, LJ1.A9, LJ1.B4, LJ1.B9
Lusb_chain_0.d_N: LJ1.A7, LJ1.B7, LU2.13, LU3.1
Lusb_chain_0.d_P: LJ1.A6, LJ1.B6, LU2.14, LU3.2
Lv3v3: LC2.1, LC3.1, LC4.1, LC7.1, LC8.1, LC22.1, LC23.1, LC32.1, LD1.1, LJ2.1, LJ4.6, LJ4.9, LJ4.11, LJ5.4, LR3.1, LR7.1, LR9.1, LR10.1, LR12.1, LTP3.1, LU1.2, LU2.2, LU4.1, LU4.10, LU4.11, LU7.3, LU8.6
