BerkeleyHCI/PolymorphicBlocks/examples/DeskController/DeskController.kicad_pcb

## KiCad design examples/DeskController/DeskController.kicad_pcb (2024-10-19)

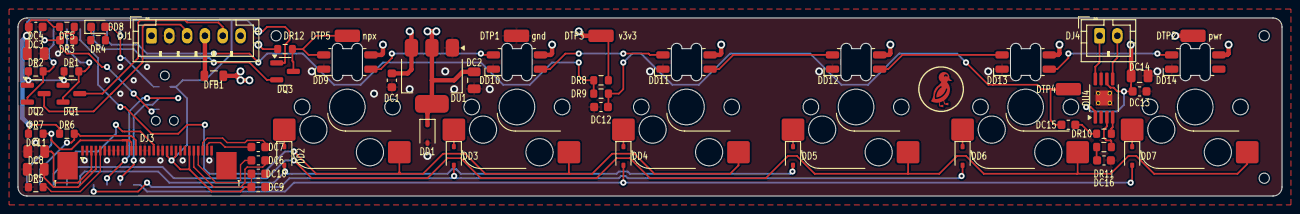
[picture p89: board DeskController.kicad_pcb from above]

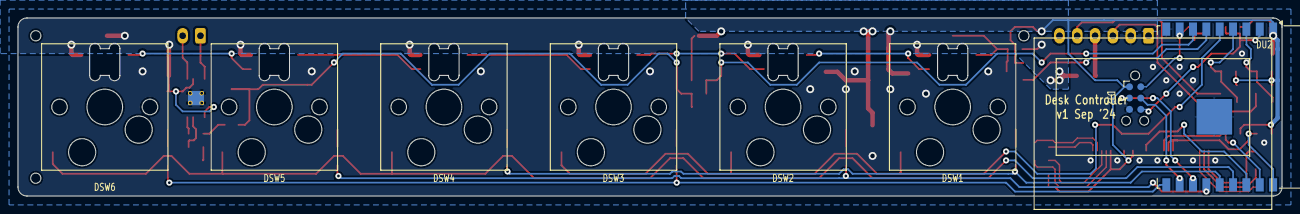
[picture p90: board DeskController.kicad_pcb from below]

Board: 2 copper layers, 142.0 x 20.0 mm, 69 parts (18 on the bottom side), 49 nets.

Parts:
DC1, DC4, DC13: 50V 100nF X7R ±10% 0603 Multilayer Ceramic Capaci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; C_0603_1608Metric
DC2, DC8: 25V 4.7uF X5R ±10% 0805 Multilayer Ceramic Capaci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; C_0805_2012Metric
DC3, DC11, DC14: 25V 10uF X5R ±10% 0805 Multilayer Ceramic Capacit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; C_0805_2012Metric
DC5, DC6, DC7, DC9, DC10, DC15, DC16: 50V 1uF X5R ±10% 0603 Multilayer Ceramic Capacito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; C_0603_1608Metric
DC12: 50V 33nF X7R ±10% 0603 Multilayer Ceramic Capacit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; C_0603_1608Metric
DD1: 3.6V~3.8V 200mW 3.6V SOD-323 Zener Diodes ROHS; D_SOD-323
DD2, DD3, DD4, DD5, DD6, DD7: 40V 600mV@1A 1A SOD-323 Schottky Diodes ROHS; D_SOD-323
DD8: -40?~+85? Red 0603 LED Indication - Discrete ROHS; LED_0603_1608Metric
DD9, DD10, DD11, DD12, DD13, DD14: SK6812MINI-E; LED_SK6812MINI-E
DFB1: ±25% 100?@100MHz 0805 Ferrite Beads ROHS; L_0805_2012Metric
DH1, DH2, DH3: JlcToolingHole_1.152mm
DJ1: B6B-PH-K; JST_PH_B6B-PH-K_1x06_P2.00mm_Vertical
DJ2: Tag-Connect_TC2030-IDC-NL_2x03_P1.27mm_Vertical
DJ3: AFC07-S30ECA-00; TE_3-1734839-0_1x30-1MP_P0.5mm_Horizontal
DJ4: B2B-PH-K; JST_PH_B2B-PH-K_1x02_P2.00mm_Vertical
DQ1, DQ2, DQ3: 30V 5.7A 26.5m?@10V,5.7A 1.4W 1.5V@250uA 1PCSNCha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; SOT-23
DR1, DR2, DR6, DR7, DR8, DR12: 100mW Thick Film Resistors 75V ±100ppm/? ±1% 4.7k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; R_0603_1608Metric
DR3: 100mW Thick Film Resistors 75V ±100ppm/? ±1% 10k?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; R_0603_1608Metric
DR4: 100mW Thick Film Resistors 75V ±100ppm/? ±1% 820?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; R_0603_1608Metric
DR5: 100mW Thick Film Resistors 75V ±100ppm/? ±1% 470k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; R_0603_1608Metric
DR9: 100mW Thick Film Resistors 75V ±100ppm/? ±1% 1k? 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; R_0603_1608Metric
DR10, DR11: 100mW Thick Film Resistors 75V ±100ppm/? ±1% 68k?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; R_0603_1608Metric
DSW1, DSW2, DSW3, DSW4, DSW5, DSW6: PG151101S11; SW_Hotswap_Kailh_MX
DTP1: gnd; TestPoint_TE_RCT_0805
DTP2: pwr; TestPoint_TE_RCT_0805
DTP3: v3v3; TestPoint_TE_RCT_0805
DTP4: spk_chain_1; TestPoint_TE_RCT_0805
DTP5: npx; TestPoint_TE_RCT_0805
DU1: LDL1117S33R; SOT-223-3_TabPin2
DU2: ESP32-C3-WROOM-02; ESP-WROOM-02
DU3: ER-OLED-0.96-1.1; Lcd_Er_Oled0.96_1.1_Outline
DU4: TPA2005D1; MSOP-8-1EP_3x3mm_P0.65mm_EP1.68x1.88mm_ThermalVias
svg2mod: G***; Symbol_DucklingSolid

Connections:
Dconn.dtx_shift.hv_io: DJ1.5, DQ1.3
Dconn.htx_shift.hv_io: DJ1.3, DQ2.3
Dconn.pwr: DFB1.1, DJ1.4
Dconn.uart.rx: DQ2.2, DR2.2, DU2.3
Dconn.uart.tx: DQ1.2, DR1.2, DU2.4
Dgnd: DC1.2, DC2.2, DC3.2, DC4.2, DC5.2, DC8.2, DC9.2, DC10.2, DC11.2, DC12.2, DC13.2, DC14.2, DC16.2, DD1.2, DD9.3, DD10.3, DD11.3, DD12.3, DD13.3, DD14.3, DJ1.2, DJ2.5, DJ3.1, DJ3.2, DJ3.6, DJ3.7, DJ3.8, DJ3.9, DJ3.10, DJ3.14, DJ3.15, DJ3.16, DJ3.18, DJ3.19, DJ3.21, DJ3.23, DJ3.30, DR4.2, DR5.2, DTP1.1, DU1.1, DU2.9, DU2.19, DU4.7, DU4.9
Di2c_pull.i2c.scl: DJ3.13, DR6.2, DU2.17
Di2c_pull.i2c.sda: DJ3.11, DJ3.12, DR7.2, DU2.18
Dledr.res.a: DD8.1, DR4.1
Dmcu.gpio.swc_0: DSW1.2, DSW2.2, DSW3.2, DU2.5
Dmcu.gpio.swc_1: DSW4.2, DSW5.2, DSW6.2, DU2.15
Dmcu.gpio.swr_0: DD2.2, DD5.2, DU2.14
Dmcu.gpio.swr_1: DD3.2, DD6.2, DU2.13
Dmcu.gpio.swr_2: DD4.2, DD7.2, DU2.10
Dmcu.program_boot_node: DD8.2, DJ2.2, DU2.8
Dmcu.program_en_node: DC5.1, DJ2.6, DR3.2, DU2.2
Dmcu.program_uart_node.a_tx: DJ2.3, DU2.12
Dmcu.program_uart_node.b_tx: DJ2.4, DU2.11
Dnpx.led[0].dout: DD9.2, DD10.4
Dnpx.led[1].dout: DD10.2, DD11.4
Dnpx.led[2].dout: DD11.2, DD12.4
Dnpx.led[3].dout: DD12.2, DD13.4
Dnpx.led[4].dout: DD13.2, DD14.4
Dnpx_shift.hv_io: DD9.4, DQ3.3, DR12.2, DTP5.1
Dnpx_shift.lv_io: DQ3.2, DU2.6
Doled.c1_cap.neg: DC6.2, DJ3.26
Doled.c1_cap.pos: DC6.1, DJ3.27
Doled.c2_cap.neg: DC7.2, DJ3.28
Doled.c2_cap.pos: DC7.1, DJ3.29
Doled.device.vcc: DC11.1, DJ3.3
Doled.device.vcomh: DC8.1, DJ3.4
Doled.iref_res.a: DJ3.5, DR5.1
Doled.reset: DJ3.17, DU2.16
Dpwr: DC1.1, DC13.1, DC14.1, DD9.1, DD10.1, DD11.1, DD12.1, DD13.1, DD14.1, DFB1.2, DR12.1, DTP2.1, DU1.3, DU4.1, DU4.6
Dspk_chain_0: DR8.2, DR9.1, DU2.7
Dspk_chain_1: DC12.1, DC15.2, DR9.2, DTP4.1
Dspk_chain_2.a: DJ4.1, DU4.8
Dspk_chain_2.b: DJ4.2, DU4.5
Dspk_drv.inn_cap.pos: DC16.1, DR11.1
Dspk_drv.inn_res.b: DR11.2, DU4.3
Dspk_drv.inp_cap.pos: DC15.1, DR10.1
Dspk_drv.inp_res.b: DR10.2, DU4.4
Dsw.d[0,0].cathode: DD2.1, DSW1.1
Dsw.d[0,1].cathode: DD3.1, DSW2.1
Dsw.d[0,2].cathode: DD4.1, DSW3.1
Dsw.d[1,0].cathode: DD5.1, DSW4.1
Dsw.d[1,1].cathode: DD6.1, DSW5.1
Dsw.d[1,2].cathode: DD7.1, DSW6.1
Dv3v3: DC2.1, DC3.1, DC4.1, DC9.1, DC10.1, DD1.1, DJ2.1, DJ3.20, DJ3.22, DJ3.25, DQ1.1, DQ2.1, DQ3.1, DR1.1, DR2.1, DR3.1, DR6.1, DR7.1, DR8.1, DTP3.1, DU1.2, DU2.1
