BerkeleyHCI/PolymorphicBlocks/examples/IotDisplay/IotDisplay.kicad_pcb

## KiCad design examples/IotDisplay/IotDisplay.kicad_pcb (2024-06-11)

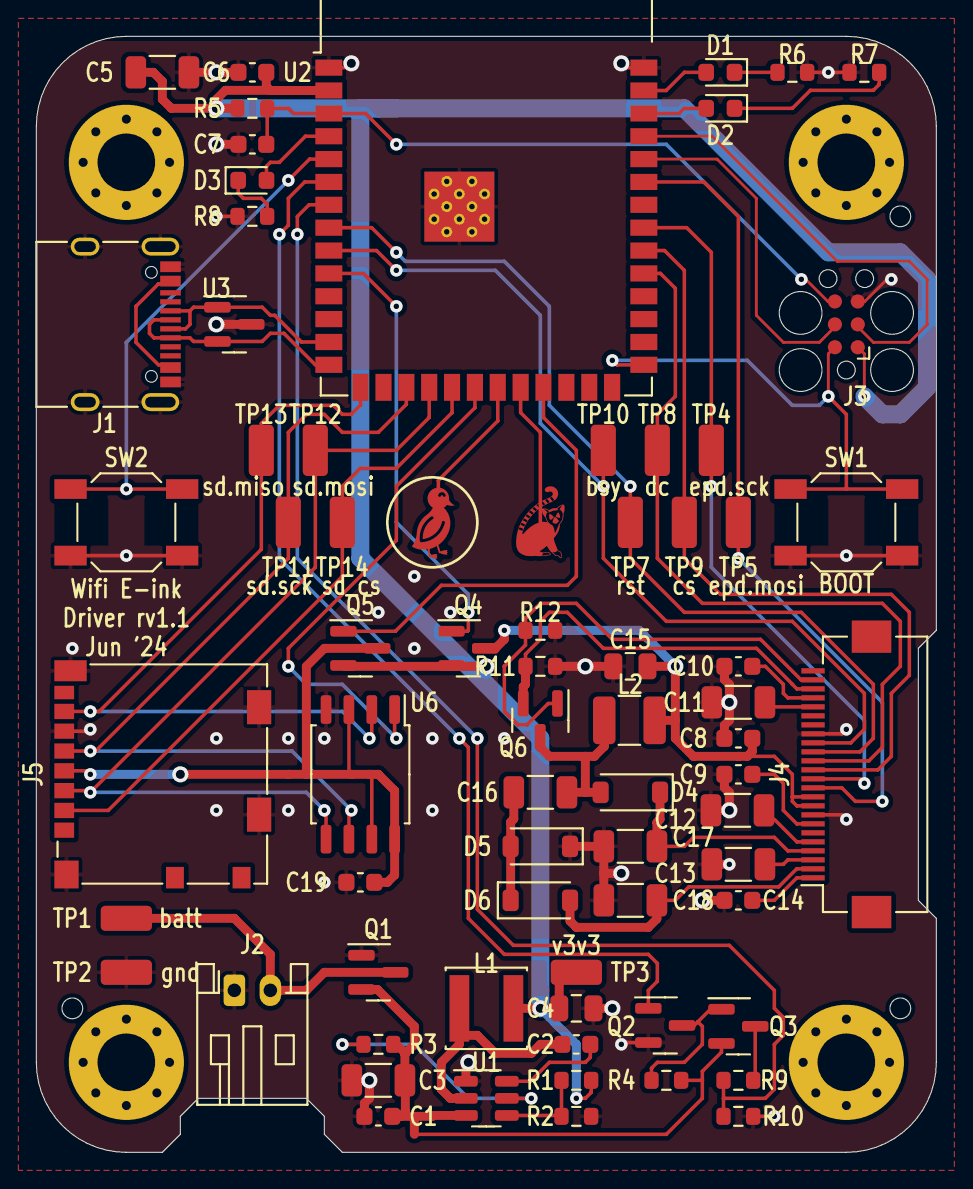
[picture p91: board IotDisplay.kicad_pcb from above]

Board: 2 copper layers, 50.0 x 62.0 mm, 74 parts (0 on the bottom side), 55 nets.

Parts:
C1, C2, C6, C7, C8, C9, C10, C14, C19: C_0603_1608Metric
C3, C5, C11, C12, C13, C16, C17, C18: C_1206_3216Metric
C4, C15: C_0805_2012Metric
D1: Red 615~630nm 1.9~2.2V 0603 Light Emitting Diodes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; LED_0603_1608Metric
D2, D3: LED_0603_1608Metric
D4, D5, D6: 20V 450mV@1A 300mA SOD-123 Schottky Barrier Diode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; D_SOD-123
H1, H2, H3: JlcToolingHole_1.152mm
J1: COM-15111; USB_C_Receptacle_XKB_U262-16XN-4BVC11
J2: S2B-PH-K; JST_PH_S2B-PH-K_1x02_P2.00mm_Horizontal
J3: Tag-Connect_TC2030-IDC-FP_2x03_P1.27mm_Vertical
J4: AFC07-S24ECA-00; Hirose_FH12-24S-0.5SH_1x24-1MP_P0.50mm_Horizontal
J5: 104031-0811; microSD_HC_Molex_104031-0811
L1: L_Sunlord_SWPA4030S
L2: L_1210_3225Metric
Q1, Q3, Q4, Q5: 30V 4A 44m?@10V,4.3A 1.4W 1.3V@250?A P Channel SO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; SOT-23
Q2: 60V 115mA 200mW 7.5?@10V,500mA 2.5V@250?A N Chann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; SOT-23
Q6: 30V 5.7A 26.5m?@10V,5.7A 1.4W 1.5V@250?A N Channe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; SOT-23
R1, R2, R3, R4, R5, R6, R7, R8, R9, R10, R11, R12: R_0603_1608Metric
SW1, SW2: 5.1mm switch; SW_SPST_SKQG_WithoutStem
TP1: batt; TestPoint_TE_RCT_0805
TP2: gnd; TestPoint_TE_RCT_0805
TP3: v3v3; TestPoint_TE_RCT_0805
TP4: epd.sck; TestPoint_TE_RCT_0805
TP5: epd.mosi; TestPoint_TE_RCT_0805
TP7: rst; TestPoint_TE_RCT_0805
TP8: dc; TestPoint_TE_RCT_0805
TP9: cs; TestPoint_TE_RCT_0805
TP10: bsy; TestPoint_TE_RCT_0805
TP11: sd.sck; TestPoint_TE_RCT_0805
TP12: sd.mosi; TestPoint_TE_RCT_0805
TP13: sd.miso; TestPoint_TE_RCT_0805
TP14: sd_cs; TestPoint_TE_RCT_0805
U1: TPS54202H; SOT-23-6
U2: ESP32-S3-WROOM-1-N16R8; ESP32-S3-WROOM-1
U3: PESD5V0X1BT; SOT-23
U4: Symbol_DucklingSolid
U5: Symbol_LemurSolid
U6: W25Q128JVSIQ; SOIC-8_5.23x5.23mm_P1.27mm

Connections:
batt.pwr: J2.2, Q1.3, TP1.1
epd.boost.boot_cap.neg: C16.2, D5.1, D6.2
epd.boost.inductor.b: C16.1, D4.2, L2.2, Q6.3
epd.boost.neg_out: C18.2, D5.2, J4.2
epd.boost.pos_out: C17.1, D4.1, J4.4
epd.device.gdr: J4.23, Q6.1, R12.1
epd.device.rese: J4.22, Q6.2, R11.1
epd.device.vcom: C14.1, J4.1
epd.device.vdd1v8: C9.1, J4.7
epd.device.vgh: C11.1, J4.20
epd.device.vgl: C10.2, J4.21
epd.device.vsh: C12.1, J4.5
epd.device.vsl: C13.2, J4.3
epd_gate.control: Q4.1, U2.10
epd_gate.output: C8.1, C15.1, J4.9, J4.10, L2.1, Q4.3
flash.cs: U2.20, U6.1
gnd: C1.2, C3.2, C4.2, C5.2, C6.2, C7.2, C8.2, C9.2, C10.1, C11.2, C12.2, C13.1, C14.2, C15.2, C17.2, C18.1, C19.2, D6.1, J1.A1, J1.A12, J1.B1, J1.B12, J1.S1, J2.1, J3.5, J4.8, J4.17, J5.6, J5.11, Q1.1, Q2.2, R2.2, R6.2, R7.2, R8.2, R10.2, R11.2, R12.2, SW1.2, SW2.2, TP2.1, U1.1, U2.1, U2.40, U2.41, U3.3, U6.4
ledb.res.a: D3.1, R8.1
ledb.signal: D3.2, U2.4
ledg.res.a: D2.1, R7.1
ledg.signal: D2.2, U2.38
ledr.res.a: D1.1, R6.1
ledr.signal: D1.2, U2.39
mcu.program_boot_node: J3.2, SW1.1, U2.27
mcu.program_en_node: C7.1, J3.6, R5.2, U2.3
mcu.program_uart_node.a_tx: J3.3, U2.37
mcu.program_uart_node.b_tx: J3.4, U2.36
mem_gate.control: Q5.1, U2.23
mem_gate.output: C19.1, J5.4, Q5.3, U6.3, U6.7, U6.8
reg_3v3.boot_cap.neg: C2.2, L1.1, U1.2
reg_3v3.boot_cap.pos: C2.1, U1.6
reg_3v3.en_res.b: R3.2, U1.5
reg_3v3.fb.output: R1.2, R2.1, U1.4
sw.out: SW2.1, U2.5
touch_duck.pad: U2.21, U4.1
touch_lemur.pad: U2.22, U5.1
tp_busy.io: J4.16, TP10.1, U2.9
tp_dc.io: J4.14, TP8.1, U2.31
tp_epd.io.mosi: J4.11, TP5.1, U2.35
tp_epd.io.sck: J4.12, TP4.1, U2.33
tp_epd_cs.io: J4.13, TP9.1, U2.32
tp_erst.io: J4.15, TP7.1, U2.8
tp_sd.io.miso: J5.7, TP13.1, U2.15, U6.2
tp_sd.io.mosi: J5.3, TP12.1, U2.18, U6.5
tp_sd.io.sck: J5.5, TP11.1, U2.17, U6.6
tp_sd_cs.io: J5.2, TP14.1, U2.19
usb.pwr: J1.A4, J1.A9, J1.B4, J1.B9
usb_chain_0.d_N: J1.A7, J1.B7, U2.13, U3.1
usb_chain_0.d_P: J1.A6, J1.B6, U2.14, U3.2
v3v3: C4.1, C5.1, C6.1, J3.1, L1.2, Q4.2, Q5.2, R1.1, R5.1, TP3.1, U2.2
vbat: C1.1, C3.1, Q1.2, Q3.2, R3.1, R4.1, U1.3
vbat_sense.output: R9.2, R10.1, U2.7
vbat_sense_gate.control: Q2.1, U2.6
vbat_sense_gate.output: Q3.3, R9.1
vbat_sense_gate.pre.drain: Q2.3, Q3.1, R4.2
