BerkeleyHCI/PolymorphicBlocks/examples/ProtectedCharger/ProtectedCharger.kicad_pcb

## KiCad design examples/ProtectedCharger/ProtectedCharger.kicad_pcb (2024-04-30)

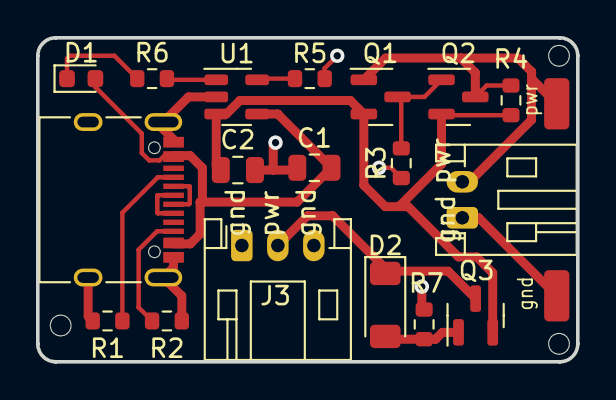
[picture p92: board ProtectedCharger.kicad_pcb from above]

Board: 2 copper layers, 30.0 x 18.0 mm, 24 parts (1 on the bottom side), 14 nets.

Parts:
C1, C2: C_0805_2012Metric
D1: LED_0603_1608Metric
D2: 2?A@1V 85? Single 3.1V~3.5V 500mW 3.3V LL-34 Zene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; D_MiniMELF
H1, H2, H3: JlcToolingHole_1.152mm
J1: COM-15111; USB_C_Receptacle_XKB_U262-16XN-4BVC11
J2: S2B-PH-K; JST_PH_S2B-PH-K_1x02_P2.00mm_Horizontal
J3: S3B-PH-K; JST_PH_S3B-PH-K_1x03_P2.00mm_Horizontal
Q1: 30V 4A 44m?@10V,4.3A 1.4W 1.3V@250?A P Channel SO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; SOT-23
Q2: 60V 5.2A 50m?@10V,3.2A 27W 2.5V@250?A P Channel S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; SOT-23
Q3: 20V 3.1A 860mW 112m?@4.5V,2.8A 1V@250?A P Channel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; SOT-23
R1, R2, R3, R4, R5, R6, R7: R_0603_1608Metric
TP1: gnd; TestPoint_TE_RCT_0805
TP2: _batt_pwr_link; TestPoint_TE_RCT_0805
U1: MCP73831T-2ACI/OT; SOT-23-5
svg2mod: G***; Symbol_DucklingSolid

Connections:
(adapter)pwr_pins.pins.2.src: D2.1, J3.2, Q3.3
batt.pwr: J2.2, Q1.1, Q2.3, R4.2, TP2.1
charge_led.res.a: D1.1, R6.1
charge_led.signal: R6.2, U1.1
charger.prog_res.a: R5.1, U1.5
charger.pwr_bat: C2.1, Q1.2, Q2.2, Q3.2, R4.1, U1.3
gnd: C1.2, C2.2, J1.A1, J1.A12, J1.B1, J1.B12, J1.S1, J2.1, J3.1, J3.3, R1.1, R2.1, R3.2, R5.2, R7.2, TP1.1, U1.2
pmos.r1.a: Q1.3, Q2.1, R3.1
pmos_load.fet.gate: D2.2, Q3.1, R7.1
usb.conn.A5: J1.A5, R1.2
usb.conn.B5: J1.B5, R2.2
usb.usb.dm: J1.A7, J1.B7
usb.usb.dp: J1.A6, J1.B6
vusb: C1.1, D1.2, J1.A4, J1.A9, J1.B4, J1.B9, U1.4
