BerkeleyHCI/PolymorphicBlocks/examples/Keyboard/Keyboard.kicad_pcb

## KiCad design examples/Keyboard/Keyboard.kicad_pcb (2024-04-20)

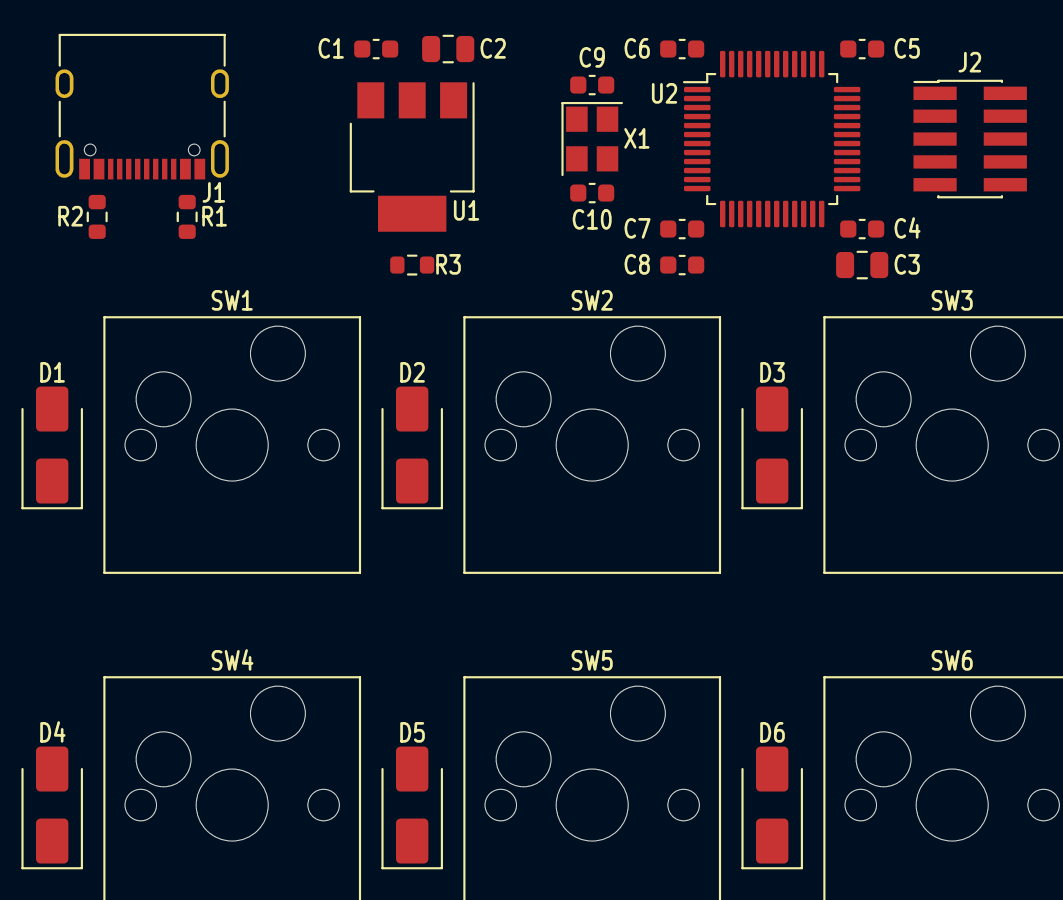
[picture p93: board Keyboard.kicad_pcb from above]

Board: 2 copper layers, 30 parts (0 on the bottom side), 23 nets, no tracks yet.

Parts:
C1, C4, C5, C6, C7, C8, C9, C10: C_0603_1608Metric
C2, C3: C_0805_2012Metric
D1, D2, D3, D4, D5, D6: 40V 550mV@1A 1A SMA(DO-214AC) Schottky Barrier Di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; D_SMA
J1: COM-15111; USB_C_Receptacle_XKB_U262-16XN-4BVC11
J2: PinHeader1.27 Shrouded 2x5; PinHeader_2x05_P1.27mm_Vertical_SMD
R1, R2, R3: R_0603_1608Metric
SW1, SW2, SW3, SW4, SW5, SW6: PG151101S11; SW_Hotswap_Kailh_MX
U1: LDL1117S33R; SOT-223-3_TabPin2
U2: STM32F103xxT6; LQFP-48_7x7mm_P0.5mm
X1: Crystal_SMD_3225-4Pin_3.2x2.5mm

Connections:
mcu.reset_node: J2.10, U2.7
mcu.swd_node.swclk: J2.4, U2.37
mcu.swd_node.swdio: J2.2, U2.34
mcu.xtal_node.driver.xtal_in: C9.1, U2.5, X1.1
mcu.xtal_node.driver.xtal_out: C10.1, U2.6, X1.3
reg.pwr_out: C2.1, C3.1, C4.1, C5.1, C6.1, C7.1, C8.1, J2.1, R3.1, U1.2, U2.1, U2.9, U2.24, U2.36, U2.48
sw.cols.0: SW1.2, SW2.2, SW3.2, U2.10
sw.cols.1: SW4.2, SW5.2, SW6.2, U2.11
sw.d[0,0].cathode: D1.1, SW1.1
sw.d[0,1].cathode: D2.1, SW2.1
sw.d[0,2].cathode: D3.1, SW3.1
sw.d[1,0].cathode: D4.1, SW4.1
sw.d[1,1].cathode: D5.1, SW5.1
sw.d[1,2].cathode: D6.1, SW6.1
sw.rows.0: D1.2, D4.2, U2.12
sw.rows.1: D2.2, D5.2, U2.13
sw.rows.2: D3.2, D6.2, U2.14
usb.conn.A5: J1.A5, R1.2
usb.conn.B5: J1.B5, R2.2
usb.gnd: C1.2, C2.2, C3.2, C4.2, C5.2, C6.2, C7.2, C8.2, C9.2, C10.2, J1.A1, J1.A12, J1.B1, J1.B12, J1.S1, J2.3, J2.5, J2.9, R1.1, R2.1, U1.1, U2.8, U2.23, U2.35, U2.44, U2.47, X1.2, X1.4
usb.pwr: C1.1, J1.A4, J1.A9, J1.B4, J1.B9, U1.3
usb.usb.dm: J1.A7, J1.B7, U2.32
usb.usb.dp: J1.A6, J1.B6, R3.2, U2.33
