BerkeleyHCI/PolymorphicBlocks/examples/PcbBot/PcbBot.kicad_pcb

## KiCad design examples/PcbBot/PcbBot.kicad_pcb (2024-03-04)

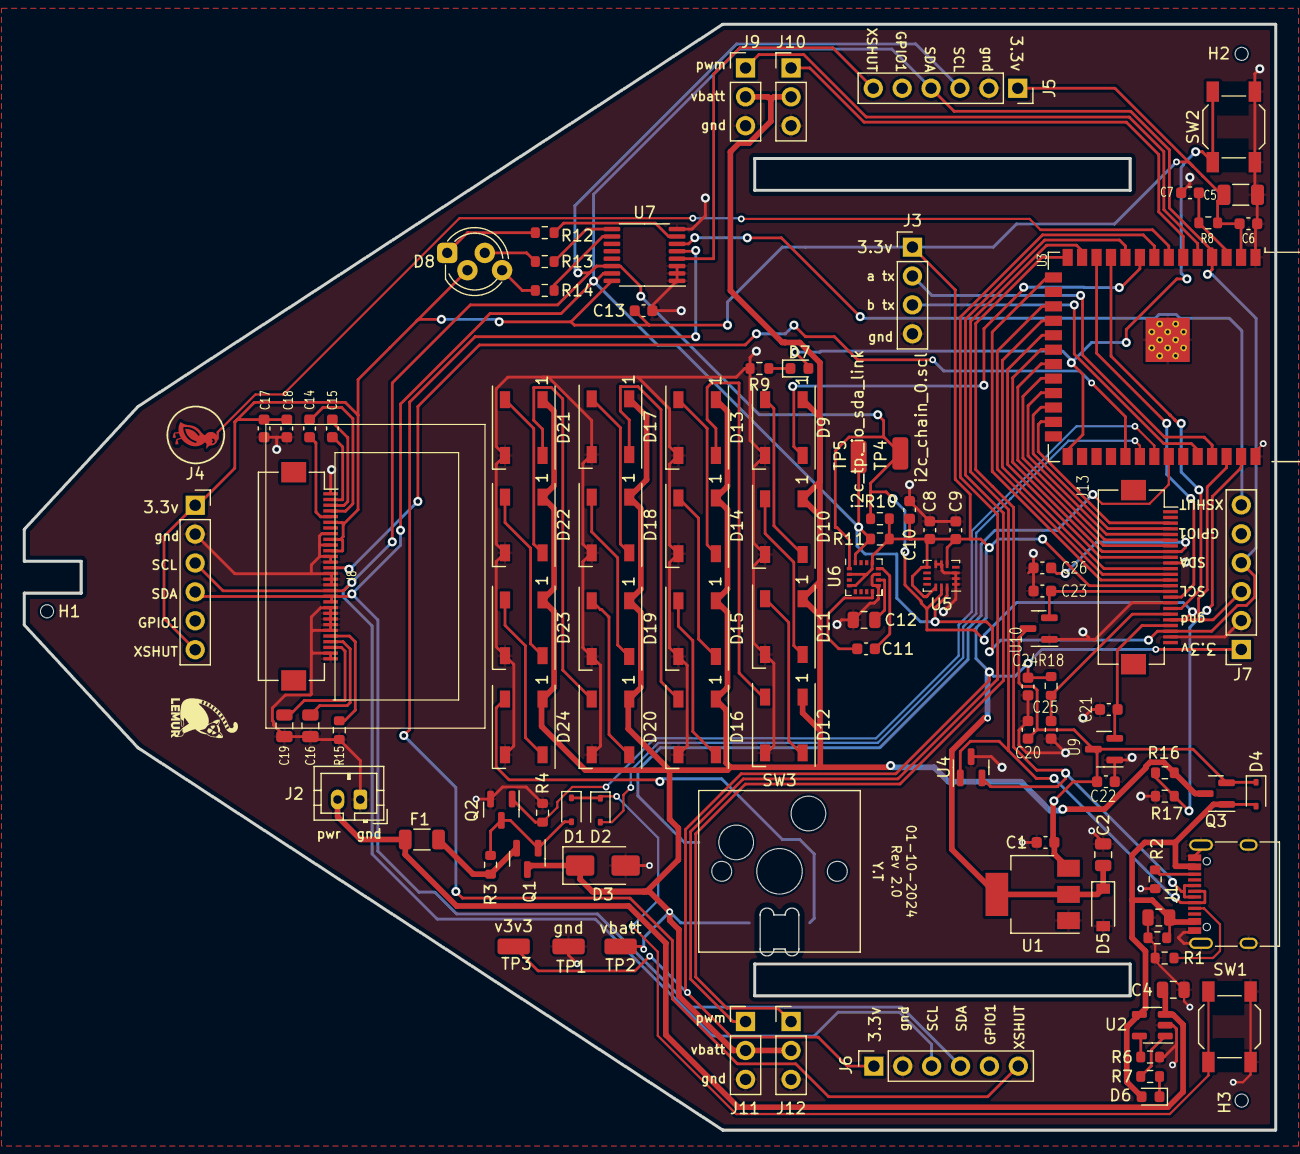
[picture p94: board PcbBot.kicad_pcb from above]

Board: 2 copper layers, 110.0 x 97.2 mm, 109 parts (0 on the bottom side), 83 nets.

Parts:
C1, C6, C7, C8, C9, C10, C11, C13, C14, C15, C17, C18, C20, C21, C22, C23, C24, C25, C26: C_0603_1608Metric
C2, C3, C4, C12, C16, C19: C_0805_2012Metric
C5: C_1206_3216Metric
D1, D2: 30V 370mV@1mA 30mA SOD-323 Schottky Barrier Diode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; D_SOD-323
D3: 10?A@2V 5? Single 5.32V~5.92V 1W 5.6V SMAF Zener 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; D_SMA
D4: 40V 600mV@1A 1A SOD-323 Schottky Barrier Diodes (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; D_SOD-323
D5: 5?A@1V 90? Single 3.6V~3.8V 350mW 3.4V SOD-123 Ze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; D_SOD-123
D6: LED_0603_1608Metric
D7: Red 615~630nm 1.9~2.2V 0603 Light Emitting Diodes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; LED_0603_1608Metric
D8: COM-09264; LED_D5.0mm-4_RGB_Staggered_Pins
D9, D10, D11, D12, D13, D14, D15, D16, D17, D18, D19, D20, D21, D22, D23, D24: WS2812B; LED_WS2812B_PLCC4_5.0x5.0mm_P3.2mm
D25: SK6812MINI-E; LED_SK6812MINI-E
F1: 6V 2A 100A 4A 1206 Resettable Fuses ROHS; R_1206_3216Metric
H1, H2, H3: JlcToolingHole_1.152mm
J1: COM-15111; USB_C_Receptacle_XKB_U262-16XN-4BVC11
J2: B2B-PH-K; JST_PH_B2B-PH-K_1x02_P2.00mm_Vertical
J3: PinHeader2.54 1x4; PinHeader_1x04_P2.54mm_Vertical
J4, J5, J6, J7: PinSocket2.54 1x6; PinSocket_1x06_P2.54mm_Vertical
J8: AFC01-S30FCA-00; Hirose_FH12-30S-0.5SH_1x30-1MP_P0.50mm_Horizontal
J9, J10, J11, J12: PinHeader2.54 1x3; PinHeader_1x03_P2.54mm_Vertical
J13: AFC01-S24FCA-00; Hirose_FH12-24S-0.5SH_1x24-1MP_P0.50mm_Horizontal
Q1: 20V 3.1A 860mW 112m?@4.5V,2.8A 1V@250?A P Channel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; SOT-23
Q2: 60V 115mA 200mW 7.5?@10V,500mA 2.5V@250?A N Chann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; SOT-23
Q3: 30V 4A 44m?@10V,4.3A 1.4W 1.3V@250?A P Channel SO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; SOT-23
R1, R2, R3, R4, R5, R6, R7, R8, R9, R10, R11, R12, R13, R14, R15, R16, R17, R18: R_0603_1608Metric
SW1, SW2: 5.1mm switch; SW_SPST_SKQG_WithoutStem
SW3: PG151101S11; SW_Hotswap_Kailh_MX
TP1: gnd; TestPoint_TE_RCT_0805
TP2: vbatt; TestPoint_TE_RCT_0805
TP3: v3v3; TestPoint_TE_RCT_0805
TP4: i2c_chain_0.scl; TestPoint_TE_RCT_0805
TP5: i2c_tp._io_sda_link; TestPoint_TE_RCT_0805
U1: LDL1117S33R; SOT-223-3_TabPin2
U2: MCP73831T-2ACI/OT; SOT-23-5
U3: ESP32-S3-WROOM-1-N16R8; ESP32-S3-WROOM-1
U4: PESD5V0X1BT; SOT-23
U5: LSM6DS3TR-C; Bosch_LGA-14_3x2.5mm_P0.5mm
U6: QMC5883L; LGA-16_3x3mm_P0.5mm
U7: PCA9554APW,118; TSSOP-16_4.4x5mm_P0.65mm
U8: ER-OLED-0.96-1.1; Lcd_Er_Oled0.96_1.1_Outline
U9: XC6206P252MR; SOT-23
U10: XC6206P122MR-G; SOT-23
svg2mod: G***; Symbol_LemurSmall
svg2mod#2: G***; Symbol_DucklingSolid

Connections:
batt.pwr: C4.1, F1.1, J2.2, U2.3
batt_sense.output: R16.2, R17.1, U3.39
cam.device.reset: C25.1, J13.19, R18.2
cam.dvp8.href: J13.16, U3.12
cam.dvp8.pclk: C26.1, J13.8, U3.20
cam.dvp8.vsync: J13.18, U3.11
cam.dvp8.xclk: J13.12, U3.17
cam.dvp8.y0: J13.6, U3.22
cam.dvp8.y1: J13.4, U3.24
cam.dvp8.y2: J13.3, U3.25
cam.dvp8.y3: J13.5, U3.23
cam.dvp8.y4: J13.7, U3.21
cam.dvp8.y5: J13.9, U3.19
cam.dvp8.y6: J13.11, U3.18
cam.dvp8.y7: J13.13, U3.15
charge_led.res.a: D6.1, R7.1
charge_led.signal: R7.2, U2.1
charger.prog_res.a: R6.1, U2.5
expander.io.rgb_blue: R14.2, U7.10
expander.io.rgb_green: R13.2, U7.9
expander.io.rgb_red: R12.2, U7.7
expander.io.tof_xshut_1: J5.6, U7.4
expander.io.tof_xshut_2: J6.6, U7.5
expander.io.tof_xshut_3: J7.6, U7.6
fuse.pwr_out: F1.2, Q1.2, R3.1
gate.btn_out: D2.2, U3.32
gate.control: Q2.1, R4.2, U3.33
gate.ctl_diode.cathode: D1.1, D2.1, SW1.1
gate.pull_res.b: D1.2, Q1.1, Q2.3, R3.2
gnd: C1.2, C2.2, C3.2, C4.2, C5.2, C6.2, C7.2, C8.2, C9.2, C10.2, C12.2, C13.2, C16.2, C17.2, C18.2, C19.2, C20.2, C21.2, C22.2, C23.2, C24.2, C25.2, C26.2, D3.2, D5.2, D9.3, D10.3, D11.3, D12.3, D13.3, D14.3, D15.3, D16.3, D17.3, D18.3, D19.3, D20.3, D21.3, D22.3, D23.3, D24.3, D25.3, J1.A1, J1.A12, J1.B1, J1.B12, J1.S1, J2.1, J3.4, J4.2, J5.2, J6.2, J7.2, J8.1, J8.8, J8.10, J8.12, J8.13, J8.15, J8.16, J8.17, J8.21, J8.22, J8.23, J8.24, J8.25, J8.29, J8.30, J9.3, J10.3, J11.3, J12.3, J13.10, J13.17, J13.23, Q2.2, R1.1, R2.1, R4.1, R5.2, R6.2, R9.2, R15.2, R17.2, SW1.2, SW2.2, SW3.2, TP1.1, U1.1, U2.2, U3.1, U3.40, U3.41, U4.3, U5.1, U5.2, U5.3, U5.6, U5.7, U6.9, U6.11, U7.1, U7.2, U7.3, U7.8, U9.1, U10.1
i2c_chain_0.scl: J4.3, J5.3, J6.3, J7.3, J8.18, J13.20, R10.2, TP4.1, U3.38, U5.13, U6.1, U7.14
i2c_chain_0.sda: J4.4, J5.4, J6.4, J7.4, J8.19, J8.20, J13.22, R11.2, TP5.1, U3.4, U5.14, U6.16, U7.15
led.res.a: D7.1, R9.1
mag.c1.pos: C12.1, U6.10
mag.set_cap.neg: C11.2, U6.12
mag.set_cap.pos: C11.1, U6.8
mcu.program_boot_node: D7.2, SW2.1, U3.27
mcu.program_en_node: C7.1, R8.2, U3.3
mcu.program_uart_node.a_tx: J3.2, U3.37
mcu.program_uart_node.b_tx: J3.3, U3.36
npx.din: D9.4, U3.9
npx.dout: D24.2, D25.4
npx.led[0].dout: D9.2, D10.4
npx.led[1].dout: D10.2, D11.4
npx.led[2].dout: D11.2, D12.4
npx.led[3].dout: D12.2, D13.4
npx.led[4].dout: D13.2, D14.4
npx.led[5].dout: D14.2, D15.4
npx.led[6].dout: D15.2, D16.4
npx.led[7].dout: D16.2, D17.4
npx.led[8].dout: D17.2, D18.4
npx.led[9].dout: D18.2, D19.4
npx.led[10].dout: D19.2, D20.4
npx.led[11].dout: D20.2, D21.4
npx.led[12].dout: D21.2, D22.4
npx.led[13].dout: D22.2, D23.4
npx.led[14].dout: D23.2, D24.4
oled.c1_cap.neg: C14.2, J8.5
oled.c1_cap.pos: C14.1, J8.4
oled.c2_cap.neg: C15.2, J8.3
oled.c2_cap.pos: C15.1, J8.2
oled.device.vcc: C19.1, J8.28
oled.device.vcomh: C16.1, J8.27
oled.iref_res.a: J8.26, R15.1
oled.reset: J8.14, U3.31
pwr: C1.1, C20.1, C22.1, D4.1, Q3.2, U1.3, U9.3, U10.3
rgb.blue_res.a: D8.4, R14.1
rgb.green_res.a: D8.3, R13.1
rgb.red_res.a: D8.1, R12.1
servo[0].pwm: J9.1, U3.5
servo[1].pwm: J10.1, U3.6
servo[2].pwm: J11.1, U3.8
servo[3].pwm: J12.1, U3.10
switch.out: SW3.1, U3.34
usb.conn.A5: J1.A5, R1.2
usb.conn.B5: J1.B5, R2.2
usb_chain_0.d_N: J1.A7, J1.B7, U3.13, U4.1
usb_chain_0.d_P: J1.A6, J1.B6, U3.14, U4.2
v1v2: C23.1, J13.15, U10.2
v2v5: C21.1, J13.21, U9.2
v3v3: C2.1, C5.1, C6.1, C8.1, C9.1, C10.1, C13.1, C17.1, C18.1, C24.1, D5.1, D8.2, J3.1, J4.1, J4.6, J5.1, J6.1, J7.1, J8.6, J8.9, J8.11, J13.14, R8.1, R10.1, R11.1, R18.1, TP3.1, U1.2, U3.2, U5.5, U5.8, U5.12, U6.2, U6.4, U6.13, U7.16
vbatt: D3.1, D9.1, D10.1, D11.1, D12.1, D13.1, D14.1, D15.1, D16.1, D17.1, D18.1, D19.1, D20.1, D21.1, D22.1, D23.1, D24.1, D25.1, J9.2, J10.2, J11.2, J12.2, Q1.3, Q3.3, R16.1, TP2.1
vusb: C3.1, D4.2, D6.2, J1.A4, J1.A9, J1.B4, J1.B9, Q3.1, R5.1, U2.4
