BerkeleyHCI/PolymorphicBlocks/examples/prerouted_blocks/Esp32s3_Wroom_1.kicad_pcb

## KiCad design examples/prerouted_blocks/Esp32s3_Wroom_1.kicad_pcb (2024-03-04)

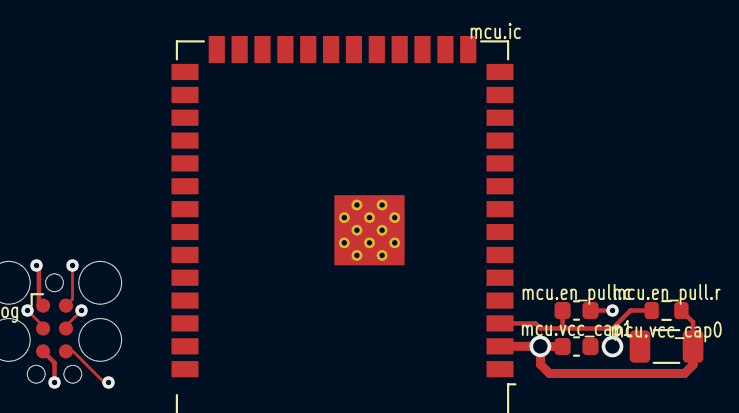
[picture p95: board Esp32s3_Wroom_1.kicad_pcb from above]

Board: 4 copper layers, 6 parts (0 on the bottom side), 6 nets.

Parts:
mcu.en_pull.c, mcu.vcc_cap1: C_0603_1608Metric
mcu.en_pull.r: R_0603_1608Metric
mcu.ic: ESP32-S3-WROOM-1-N16R8; ESP32-S3-WROOM-1
mcu.prog: Tag-Connect_TC2030-IDC-FP_2x03_P1.27mm_Vertical
mcu.vcc_cap0: C_1206_3216Metric

Connections:
gnd: mcu.en_pull.c.2, mcu.ic.1, mcu.ic.40, mcu.ic.41, mcu.prog.5, mcu.vcc_cap0.2, mcu.vcc_cap1.2
mcu.program_boot_node: mcu.ic.27, mcu.prog.2
mcu.program_en_node: mcu.en_pull.c.1, mcu.en_pull.r.2, mcu.ic.3, mcu.prog.6
mcu.program_uart_node.a_tx: mcu.ic.37, mcu.prog.3
mcu.program_uart_node.b_tx: mcu.ic.36, mcu.prog.4
v3v3: mcu.en_pull.r.1, mcu.ic.2, mcu.prog.1, mcu.vcc_cap0.1, mcu.vcc_cap1.1
