BerkeleyHCI/PolymorphicBlocks/examples/prerouted_blocks/ErOled096_1_1.kicad_pcb

## KiCad design examples/prerouted_blocks/ErOled096_1_1.kicad_pcb (2024-03-04)

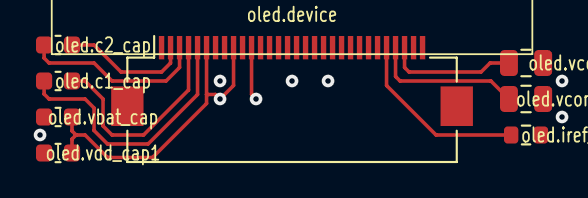
[picture p96: board ErOled096_1_1.kicad_pcb from above]

Board: 4 copper layers, 9 parts (0 on the bottom side), 10 nets.

Parts:
oled.c1_cap, oled.c2_cap, oled.vbat_cap, oled.vdd_cap1: C_0603_1608Metric
oled.device: AFC01-S30FCA-00; Hirose_FH12-30S-0.5SH_1x30-1MP_P0.50mm_Horizontal
oled.iref_res: R_0603_1608Metric
oled.lcd: ER-OLED-0.96-1.1; Lcd_Er_Oled0.96_1.1_Outline
oled.vcc_cap, oled.vcomh_cap: C_0805_2012Metric

Connections:
gnd: oled.device.1, oled.device.8, oled.device.10, oled.device.12, oled.device.13, oled.device.15, oled.device.16, oled.device.17, oled.device.21, oled.device.22, oled.device.23, oled.device.24, oled.device.25, oled.device.29, oled.device.30, oled.iref_res.2, oled.vbat_cap.2, oled.vcc_cap.2, oled.vcomh_cap.2, oled.vdd_cap1.2
i2c_pull.i2c.sda: oled.device.19, oled.device.20
oled.c1_cap.neg: oled.c1_cap.2, oled.device.5
oled.c1_cap.pos: oled.c1_cap.1, oled.device.4
oled.c2_cap.neg: oled.c2_cap.2, oled.device.3
oled.c2_cap.pos: oled.c2_cap.1, oled.device.2
oled.device.vcc: oled.device.28, oled.vcc_cap.1
oled.device.vcomh: oled.device.27, oled.vcomh_cap.1
oled.iref_res.a: oled.device.26, oled.iref_res.1
v3v3: oled.device.6, oled.device.9, oled.device.11, oled.vbat_cap.1, oled.vdd_cap1.1
