BerkeleyHCI/PolymorphicBlocks/examples/UsbSourceMeasure/UsbSourceMeasure.kicad_pcb

## KiCad design examples/UsbSourceMeasure/UsbSourceMeasure.kicad_pcb (2024-01-06)

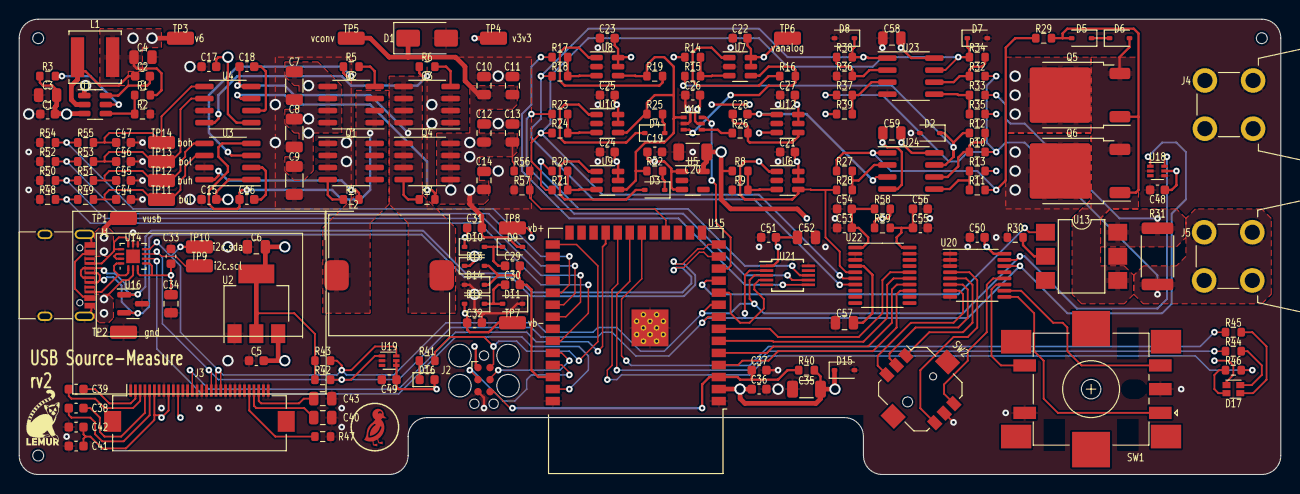
[picture p97: board UsbSourceMeasure.kicad_pcb from above]

Board: 4 copper layers, 133.0 x 48.0 mm, 193 parts (0 on the bottom side), 118 nets.

Parts:
C1, C2, C5, C15, C16, C17, C18, C19, C21, C22, C23, C24, C25, C26, C27, C28, C29, C30, C31, C32, C33, C36, C37, C38, C39, C41, C42, C44, C45, C46, C47, C48, C49, C50, C51, C53, C54, C55, C56: C_0603_1608Metric
C3, C4, C6, C10, C11, C12, C13, C14, C34, C40, C43, C52, C57, C58, C59: C_0805_2012Metric
C7, C8, C9, C20, C35: C_1206_3216Metric
D1: 5?A@27V 50? Single 34.2V~37.9V 1W 36V SMAF Zener 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; D_SMA
D2, D7, D8: 20?A@1V 100? Single 2.5V~2.9V 200mW 2.7V SOD-323 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; D_SOD-323
D3, D4, D9, D10, D11, D12, D13, D14: 30V 370mV@1mA 30mA SOD-323 Schottky Barrier Diode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; D_SOD-323
D5, D6: 500nA@6V 15? Single 8.5V~9.6V 200mW 9.1V SOD-323 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; D_SOD-323
D15: 5?A@1V 90? Single 3.53V~3.67V 200mW 3.6V SOD-323 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; D_SOD-323
D16: Red 615~630nm 1.9~2.2V 0603 Light Emitting Diodes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; LED_0603_1608Metric
D17: EAST1616RGBB2; LED_LiteOn_LTST-C19HE1WT
H1, H2, H3: JlcToolingHole_1.152mm
J1: COM-15111; USB_C_Receptacle_XKB_U262-16XN-4BVC11
J2: Tag-Connect_TC2030-IDC-FP_2x03_P1.27mm_Vertical
J3: AFC01-S30FCA-00; Hirose_FH12-30S-0.5SH_1x30-1MP_P0.50mm_Horizontal
J4, J5: CT3151-*; CalTest_CT3151
L1: L_Sunlord_SWPA5040S
L2: L_TDK_SLF12575
Q1, Q2, Q3, Q4: 40V 18A 3.1W 7.5m?@10V,10A 2V@250?A N Channel SOP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; SOIC-8_3.9x4.9mm_P1.27mm
Q5: SQD50N10-8M9L_GE3; TO-252-2
Q6: SQD50P06-15L_GE3; TO-252-2
R1, R2, R3, R4, R5, R6, R7, R8, R9, R10, R11, R12, R13, R14, R15, R16, R17, R18, R19, R20, R21, R22, R23, R24, R25, R26, R27, R28, R29, R30, R32, R33, R34, R35, R36, R37, R38, R39, R40, R41, R42, R43, R44, R45, R46, R47, R48, R49, R50, R51, R52, R53, R54, R55, R56, R57, R58, R59: R_0603_1608Metric
R31: R_2512_6332Metric
SW1: PEC11S-929K-S0015; RotaryEncoder_Bourns_PEC11S
SW2: SKRHABE010; DirectionSwitch_Alps_SKRH
TP1: vusb; TestPoint_TE_RCT_0805
TP2: gnd; TestPoint_TE_RCT_0805
TP3: v6; TestPoint_TE_RCT_0805
TP4: v3v3; TestPoint_TE_RCT_0805
TP5: vconv; TestPoint_TE_RCT_0805
TP6: vanalog; TestPoint_TE_RCT_0805
TP7: vb-; TestPoint_TE_RCT_0805
TP8: vb+; TestPoint_TE_RCT_0805
TP9: i2c.scl; TestPoint_TE_RCT_0805
TP10: i2c.sda; TestPoint_TE_RCT_0805
TP11: bul; TestPoint_TE_RCT_0805
TP12: buh; TestPoint_TE_RCT_0805
TP13: bol; TestPoint_TE_RCT_0805
TP14: boh; TestPoint_TE_RCT_0805
U1: TPS54202H; SOT-23-6
U2: LDL1117S33R; SOT-223-3_TabPin2
U3, U4: UCC27282DR; SOIC-8_3.9x4.9mm_P1.27mm
U5: AP2210K-3.3; SOT-23-5
U6, U7, U8, U9, U10, U12: TLV9061S; SOT-23-6
U11: NLAS4157; SOT-363_SC-70-6
U13: TLP3545A(TP1,F; SMDIP-6_W7.62mm
U14: FUSB302B11MPX; WQFN-14-1EP_2.5x2.5mm_P0.5mm_EP1.45x1.45mm
U15: ESP32-S3-WROOM-1-N16R8; ESP32-S3-WROOM-1
U16: PESD5V0X1BT; SOT-23
U17: ER-OLED-0.96-1.1; Lcd_Er_Oled0.96_1.1_Outline
U18, U19: TMP1075N; SOT-563
U20: PCA9554APW,118; TSSOP-16_4.4x5mm_P0.65mm
U21: MCP4728-E/UN; MSOP-10_3x3mm_P0.5mm
U22: MCP3561R-*/ST; TSSOP-20_4.4x6.5mm_P0.65mm
U23, U24: OPA2197IDR; SOIC-8_3.9x4.9mm_P1.27mm
svg2mod: G***; Symbol_LemurSmall
svg2mod#2: G***; Symbol_DucklingSolid

Connections:
adc.cs: U15.4, U22.13
adc.ic.avdd: C53.1, C54.1, R58.2, U22.1
adc.ic.dvdd: C55.1, C56.1, R59.2, U22.20
adc.ic.vrefp: C57.1, U22.4
adc.spi.miso: U15.7, U22.16
adc.spi.mosi: U15.6, U22.15
adc.spi.sck: U15.5, U22.14
ampdmeas_amps.inn.0: R27.2, R28.1, U24.2
ampdmeas_amps.inn.1: R10.2, R12.2, U24.6
ampdmeas_amps.inp.0: C28.1, U12.1, U24.3
ampdmeas_amps.inp.1: R11.2, R13.2, U24.5
ampdmeas_amps.out.1: D2.1, R12.1, R15.1, U24.7
boosth_pull.io: R54.2, R55.1, U15.31
boosth_rc.output: C47.1, R55.2, TP14.1, U4.5
boostl_pull.io: R52.2, R53.1, U15.32
boostl_rc.output: C46.1, R53.2, TP13.1, U4.6
boot.d_neg_1.anode: C30.2, D11.2, D12.1
boot.d_pos_1.cathode: C29.1, D9.1, D10.2
boot.out_pos: C31.1, C59.1, D10.1, TP8.1, U24.8
boot.pwm: C29.2, C30.1, D13.2, D14.1, U15.38
boot_neg_forced.pwr_in: C32.2, C59.2, D12.2, TP7.1, U24.4
buckh_pull.io: R50.2, R51.1, U15.33
buckh_rc.output: C45.1, R51.2, TP12.1, U3.5
buckl_pull.io: R48.2, R49.1, U15.35
buckl_rc.output: C44.1, R49.2, TP11.1, U3.6
control.drive: R11.1, R27.1, R29.2, U24.1
control.driver.clamp1.cathode: D5.1, D6.1
control.driver.out: D6.2, Q5.3, Q6.3, U13.4
control.driver.res.a: D5.2, Q5.1, Q6.1, R29.1
control.drv_en: U13.1, U15.11
control.err_sink.diode.anode: D4.2, R25.1
control.err_sink.diode.cathode: D4.1, U10.1
control.err_sink.rtop.b: R23.2, R24.2, U10.3
control.err_source.diode.anode: D3.2, U9.1
control.err_source.diode.cathode: D3.1, R22.1
control.err_source.rtop.b: R20.2, R21.2, U9.3
control.err_volt1.output: R16.2, U7.4, U11.3
control.err_volt1.rout.a: R16.1, U7.1
control.err_volt1.rtop.b: R14.2, R15.2, U7.3
control.err_volt.output: R19.2, R22.2, R25.2, U8.4, U9.4, U10.4, U11.1
control.err_volt.rout.a: R19.1, U8.1
control.err_volt.rtop.b: R17.2, R18.2, U8.3
control.gate.pwr_out: R31.1, R33.1, U13.6
control.gate.res.a: R30.1, U13.2
control.int.r.b: C28.2, R26.2, U12.4
control.int_link: R26.1, U11.4
control.meas_i: D7.1, R21.1, R24.1, R34.1, U22.6, U23.7
control.meas_v: D8.1, R18.1, R38.1, U22.7, U23.1
control.outa: J5.1, R10.1, R31.2, R32.1, R37.1
conv.boost_sw.driver.ic.hb: C18.1, U4.2
conv.boost_sw.high_gate_res.a: R7.1, U4.3
conv.boost_sw.high_gate_res.b: Q4.4, R7.2
conv.boost_sw.low_gate_res.a: R6.1, U4.8
conv.boost_sw.low_gate_res.b: Q3.4, R6.2
conv.buck_sw.driver.ic.hb: C16.1, U3.2
conv.buck_sw.high_gate_res.a: R5.1, U3.3
conv.buck_sw.high_gate_res.b: Q2.4, R5.2
conv.buck_sw.low_gate_res.a: R4.1, U3.8
conv.buck_sw.low_gate_res.b: Q1.4, R4.2
conv.power_path.switch_in: C16.2, L2.1, Q1.5, Q1.6, Q1.7, Q1.8, Q2.1, Q2.2, Q2.3, U3.4
conv.power_path.switch_out: C18.2, L2.2, Q3.5, Q3.6, Q3.7, Q3.8, Q4.1, Q4.2, Q4.3, U4.4
conv_sense.output: R56.2, R57.1, U15.18
dac.ldac: U15.10, U21.4
dac.out0: R17.1, U21.6
dac.out1: R23.1, U21.7
dac.out2: R20.1, U21.8
dir.a: SW2.1, U20.5
dir.b: SW2.4, U20.12
dir.c: SW2.3, U20.7
dir.center: SW2.2, U20.6
dir.d: SW2.6, U20.4
enc.a: SW1.A, U20.9
enc.b: SW1.B, U20.10
enc.sw: SW1.S1, U20.11
gnd: C1.2, C3.2, C4.2, C5.2, C6.2, C7.2, C8.2, C9.2, C10.2, C11.2, C12.2, C13.2, C14.2, C15.2, C17.2, C19.2, C20.2, C21.2, C22.2, C23.2, C24.2, C25.2, C26.2, C27.2, C32.1, C33.2, C34.2, C35.2, C36.2, C37.2, C40.2, C41.2, C42.2, C43.2, C44.2, C45.2, C46.2, C47.2, C48.2, C49.2, C50.2, C51.2, C52.2, C53.2, C54.2, C55.2, C56.2, C57.2, C58.2, D1.2, D2.2, D7.2, D8.2, D11.1, D14.2, D15.2, J1.A1, J1.A12, J1.B1, J1.B12, J1.S1, J2.5, J3.1, J3.8, J3.10, J3.12, J3.13, J3.15, J3.16, J3.17, J3.21, J3.22, J3.23, J3.24, J3.25, J3.29, J3.30, J4.1, Q1.1, Q1.2, Q1.3, Q3.1, Q3.2, Q3.3, Q6.2, R2.2, R9.2, R30.2, R36.1, R47.2, R48.1, R50.1, R52.1, R54.1, R57.2, SW1.C, SW1.S2, SW2.5, TP2.1, U1.1, U2.1, U3.7, U4.7, U5.2, U6.2, U7.2, U8.2, U9.2, U10.2, U11.2, U12.2, U14.8, U14.9, U14.15, U15.1, U15.40, U15.41, U16.3, U18.2, U18.4, U19.2, U20.1, U20.2, U20.3, U20.8, U21.10, U22.2, U22.3, U22.19, U23.4
i2c_pull.i2c.scl: J3.18, R42.2, TP9.1, U14.6, U15.8, U18.1, U19.1, U20.14, U21.2
i2c_pull.i2c.sda: J3.19, J3.20, R43.2, TP10.1, U14.7, U15.9, U18.6, U19.6, U20.15, U21.3
led.res.a: D16.1, R41.1
mcu.gpio.off_0: U11.6, U15.12
mcu.gpio.rgb_blue: R46.2, U15.22
mcu.gpio.rgb_green: R45.2, U15.20
mcu.gpio.rgb_red: R44.2, U15.21
mcu.program_boot_node: J2.2, R41.2, U15.27
mcu.program_en_node: C37.1, J2.6, R40.2, U15.3
mcu.program_uart_node.a_tx: J2.3, U15.37
mcu.program_uart_node.b_tx: J2.4, U15.36
oled.c1_cap.neg: C38.2, J3.5
oled.c1_cap.pos: C38.1, J3.4
oled.c2_cap.neg: C39.2, J3.3
oled.c2_cap.pos: C39.1, J3.2
oled.device.vcc: C43.1, J3.28
oled.device.vcomh: C40.1, J3.27
oled.iref_res.a: J3.26, R47.1
oled.reset: J3.14, U15.23
pd.ic.vconn: U14.12, U14.13
pd.int: U14.5, U15.39
ref_div.output: R8.2, R9.1, U6.3
reg_6v.boot_cap.neg: C2.2, L1.1, U1.2
reg_6v.boot_cap.pos: C2.1, U1.6
reg_6v.en_res.b: R3.2, U1.5
reg_6v.fb.output: R1.2, R2.1, U1.4
rgb.blue_res.a: D17.1, R46.1
rgb.green_res.a: D17.4, R45.1
rgb.red_res.a: D17.3, R44.1
usb.A5: J1.A5, U14.10, U14.11
usb.B5: J1.B5, U14.1, U14.14
usb_chain_0.d_N: J1.A7, J1.B7, U15.13, U16.1
usb_chain_0.d_P: J1.A6, J1.B6, U15.14, U16.2
v3v3: C6.1, C33.1, C34.1, C35.1, C36.1, C41.1, C42.1, C48.1, C49.1, C50.1, D13.1, D15.1, D16.2, D17.2, J2.1, J3.6, J3.9, J3.11, R40.1, R42.1, R43.1, TP4.1, U2.2, U14.3, U14.4, U15.2, U18.5, U19.4, U19.5, U20.16
v6: C4.1, C5.1, C15.1, C17.1, C19.1, L1.2, R1.1, TP3.1, U2.3, U3.1, U4.1, U5.1, U5.3
vanalog: C20.1, C21.1, C22.1, C23.1, C24.1, C25.1, C26.1, C27.1, C51.1, C52.1, R8.1, R58.1, R59.1, TP6.1, U5.5, U6.5, U6.6, U7.5, U7.6, U8.5, U8.6, U9.5, U9.6, U10.5, U10.6, U11.5, U12.5, U12.6, U21.1
vcenter: R13.1, R14.1, R28.2, R35.1, R39.1, U6.1, U6.4, U12.3, U22.5
vconv: C10.1, C11.1, C12.1, C13.1, C14.1, C31.2, C58.1, D1.1, D9.2, Q4.5, Q4.6, Q4.7, Q4.8, Q5.2, R56.1, TP5.1, U23.8
vimeas_amps.inn.0: R36.2, R38.2, U23.2
vimeas_amps.inn.1: R32.2, R34.2, U23.6
vimeas_amps.inp.0: R37.2, R39.2, U23.3
vimeas_amps.inp.1: R33.2, R35.2, U23.5
vusb: C1.1, C3.1, C7.1, C8.1, C9.1, J1.A4, J1.A9, J1.B4, J1.B9, Q2.5, Q2.6, Q2.7, Q2.8, R3.1, TP1.1, U1.3, U14.2
