BerkeleyHCI/PolymorphicBlocks/examples/prerouted_blocks/UsbCFusb302bEsd.kicad_pcb

## KiCad design examples/prerouted_blocks/UsbCFusb302bEsd.kicad_pcb (2024-01-06)

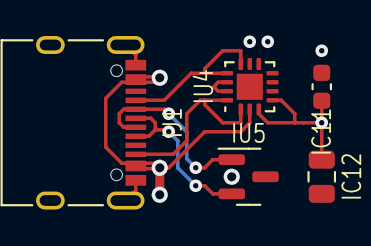
[picture p98: board UsbCFusb302bEsd.kicad_pcb from above]

Board: 2 copper layers, 5 parts (0 on the bottom side), 8 nets.

Parts:
IC11: C_0603_1608Metric
IC12: C_0805_2012Metric
IJ1: COM-15111 (Sparkfun); USB_C_Receptacle_XKB_U262-16XN-4BVC11
IU4: FUSB302B11MPX (ON Semiconductor); WQFN-14-1EP_2.5x2.5mm_P0.5mm_EP1.45x1.45mm
IU5: PESD5V0X1BT (Nexperia); SOT-23

Connections:
Ignd: IC11.2, IC12.2, IJ1.A1, IJ1.A12, IJ1.B1, IJ1.B12, IJ1.S1, IU4.8, IU4.9, IU4.15, IU5.3
Ipd.ic.vconn: IU4.12, IU4.13
Iusb.A5: IJ1.A5, IU4.10, IU4.11
Iusb.B5: IJ1.B5, IU4.1, IU4.14
Iusb_chain_0.d_N: IJ1.A7, IJ1.B7, IU5.1
Iusb_chain_0.d_P: IJ1.A6, IJ1.B6, IU5.2
Iv3v3: IC11.1, IC12.1, IU4.3, IU4.4
Ivusb: IJ1.A4, IJ1.A9, IJ1.B4, IJ1.B9, IU4.2
