BerkeleyHCI/PolymorphicBlocks/examples/IotIron/IotIron.kicad_pcb

## KiCad design examples/IotIron/IotIron.kicad_pcb (2023-10-19)

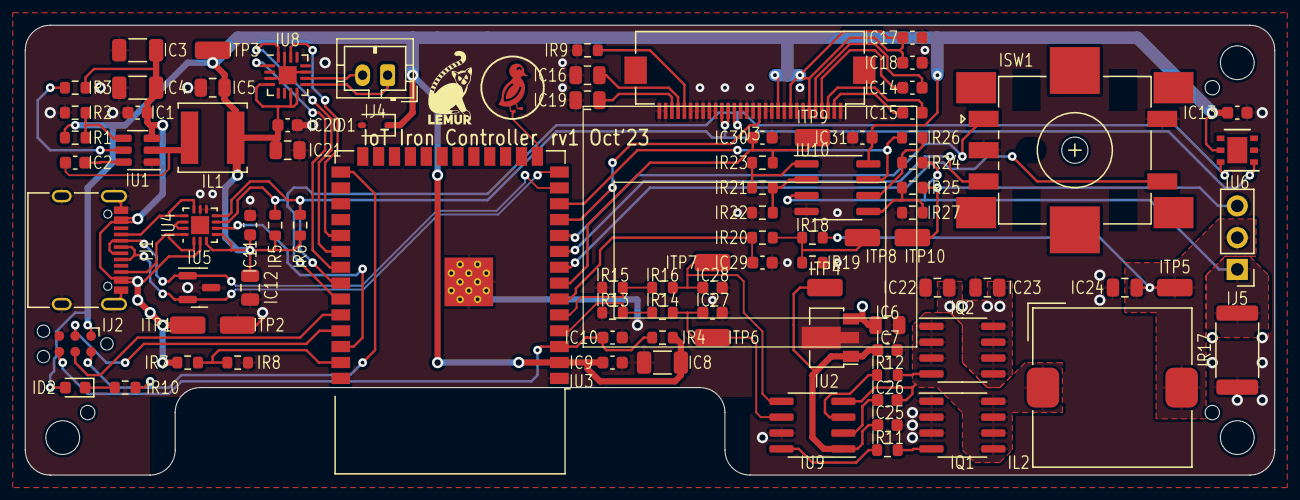
[picture p99: board IotIron.kicad_pcb from above]

Board: 2 copper layers, 100.0 x 36.0 mm, 98 parts (0 on the bottom side), 59 nets.

Parts:
H10, H11, H14: MountingHole_2.7mm_M2.5
IC1, IC2, IC7, IC9, IC10, IC11, IC13, IC14, IC15, IC17, IC18, IC20, IC25, IC26, IC27, IC28, IC29, IC30, IC31: C_0603_1608Metric
IC3, IC4, IC8: C_1206_3216Metric
IC5, IC6, IC12, IC16, IC19, IC21, IC22, IC23, IC24: C_0805_2012Metric
ID1: BZT52B3V6S (SMC(Sangdest Microelectronicstronic (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; D_SOD-323
ID2: KT-0603R (Hubei KENTO Elec) - Red 615~630nm 1.9~2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; LED_0603_1608Metric
IH1, IH2, IH3: JlcToolingHole_1.152mm
IJ1: COM-15111 (Sparkfun); USB_C_Receptacle_XKB_U262-16XN-4BVC11
IJ2: Tag-Connect_TC2030-IDC-NL_2x03_P1.27mm_Vertical
IJ3: AFC01-S30FCA-00 (Jushuo); Hirose_FH12-30S-0.5SH_1x30-1MP_P0.50mm_Horizontal
IJ4: B2B-PH-K (JST); JST_PH_B2B-PH-K_1x02_P2.00mm_Vertical
IJ5: PinHeader2.54 1x3 (Generic); PinHeader_1x03_P2.54mm_Vertical
IL1: L_Sunlord_SWPA5040S
IL2: L_TDK_SLF12565
IQ1, IQ2: IRF7458TRPBF (Infineon Technologies) - 30V 14A 8m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; SOIC-8_3.9x4.9mm_P1.27mm
IR1, IR2, IR3, IR4, IR5, IR6, IR7, IR8, IR9, IR10, IR11, IR12, IR13, IR14, IR15, IR16, IR18, IR19, IR20, IR21, IR22, IR23, IR24, IR25, IR26, IR27: R_0603_1608Metric
IR17: R_2512_6332Metric
ISW1: EC11J1525402 (Alps Alpine); RotaryEncoder_Alps_EC11J15-Switch
ITP1: 5015 (Keystone) - vusb; TestPoint_TE_RCT_0805
ITP2: 5015 (Keystone) - gnd; TestPoint_TE_RCT_0805
ITP3: 5015 (Keystone) - v3v3; TestPoint_TE_RCT_0805
ITP4: 5015 (Keystone) - vgate; TestPoint_TE_RCT_0805
ITP5: 5015 (Keystone) - conv_out; TestPoint_TE_RCT_0805
ITP6: 5015 (Keystone) - _low_rc_output_link; TestPoint_TE_RCT_0805
ITP7: 5015 (Keystone) - _high_rc_output_link; TestPoint_TE_RCT_0805
ITP8: 5015 (Keystone) - _vsense_output_link; TestPoint_TE_RCT_0805
ITP9: 5015 (Keystone) - _tp_i_output_link; TestPoint_TE_RCT_0805
ITP10: 5015 (Keystone) - _tamp_input_positive_link; TestPoint_TE_RCT_0805
IU1: TPS54202H (Texas Instruments); SOT-23-6
IU2: L78L12AC (STMicroelectronics); SOT-89-3
IU3: ESP32-S3-WROOM-1-N16R8 (Espressif Systems); ESP32-S3-WROOM-1
IU4: FUSB302B11MPX (ON Semiconductor); WQFN-14-1EP_2.5x2.5mm_P0.5mm_EP1.45x1.45mm
IU5: PESD5V0X1BT (Nexperia); SOT-23
IU6: HDC1080 (Texas Instruments); WSON-6-1EP_3x3mm_P0.95mm
IU7: ER-OLED-0.96-1.1 (EastRising); Lcd_Er_Oled0.96_1.1_Outline
IU8: MAX98357AETE+T (Maxim Integrated); QFN-16-1EP_3x3mm_P0.5mm_EP1.45x1.45mm
IU9: UCC27282DR (Texas Instruments); SOIC-8_3.9x4.9mm_P1.27mm
IU10: OPA2333AIDR (Texas Instruments); SOIC-8_3.9x4.9mm_P1.27mm
UU5: Lemur; Symbol_LemurSmall
svg2mod: G***; Symbol_DucklingSolid

Connections:
Iconv.sw.driver.ic.hb: IC26.1, IU9.2
Iconv.sw.high_gate_res.a: IR12.1, IU9.3
Iconv.sw.high_gate_res.b: IQ2.4, IR12.2
Iconv.sw.low_gate_res.a: IR11.1, IU9.8
Iconv.sw.low_gate_res.b: IQ1.4, IR11.2
Iconv.sw.out: IC26.2, IL2.1, IQ1.5, IQ1.6, IQ1.7, IQ1.8, IQ2.1, IQ2.2, IQ2.3, IU9.4
Iconv_out: IC24.1, IJ5.2, IL2.2, IR18.1, ITP5.1
Ienc.a: ISW1.A, IU3.10
Ienc.b: ISW1.B, IU3.9
Ienc.sw: ISW1.S1, IU3.8
Ignd: IC1.2, IC3.2, IC4.2, IC5.2, IC6.2, IC7.2, IC8.2, IC9.2, IC10.2, IC11.2, IC12.2, IC13.2, IC16.2, IC17.2, IC18.2, IC19.2, IC20.2, IC21.2, IC22.2, IC23.2, IC24.2, IC25.2, IC27.2, IC28.2, IC29.2, IC30.2, IC31.2, ID1.2, IJ1.A1, IJ1.A12, IJ1.B1, IJ1.B12, IJ1.S1, IJ2.5, IJ3.1, IJ3.8, IJ3.10, IJ3.12, IJ3.13, IJ3.15, IJ3.16, IJ3.17, IJ3.21, IJ3.22, IJ3.23, IJ3.24, IJ3.25, IJ3.29, IJ3.30, IQ1.1, IQ1.2, IQ1.3, IR2.2, IR8.2, IR9.2, IR13.1, IR15.1, IR17.1, IR19.2, IR22.2, IR27.1, ISW1.C, ISW1.S2, ITP2.1, IU1.1, IU2.2, IU3.1, IU3.40, IU3.41, IU4.8, IU4.9, IU4.15, IU5.3, IU6.2, IU8.3, IU8.11, IU8.15, IU8.17, IU9.7, IU10.4
Ihigh_pull.io: IR15.2, IR16.1, IU3.5
Ihigh_rc.output: IC28.1, IR16.2, ITP7.1, IU9.5
Ii2c_pull.i2c.scl: IJ3.18, IR5.2, IU3.35, IU4.6, IU6.6
Ii2c_pull.i2c.sda: IJ3.19, IJ3.20, IR6.2, IU3.34, IU4.7, IU6.1
Iifilt.output: IR21.1, IR23.1, IU10.1
Iisense.pwr_out: IJ5.1, IR17.2, IR24.1, IU10.3
Iledr.res.a: ID2.1, IR10.1
Ilow_pull.io: IR13.2, IR14.1, IU3.4
Ilow_rc.output: IC27.1, IR14.2, ITP6.1, IU9.6
Imcu.program_boot_node: IJ2.2, IR10.2, IU3.27
Imcu.program_en_node: IC10.1, IJ2.6, IR4.2, IU3.3
Imcu.program_uart_node.a_tx: IJ2.3, IU3.37
Imcu.program_uart_node.b_tx: IJ2.4, IU3.36
Ioled.c1_cap.neg: IC14.2, IJ3.5
Ioled.c1_cap.pos: IC14.1, IJ3.4
Ioled.c2_cap.neg: IC15.2, IJ3.3
Ioled.c2_cap.pos: IC15.1, IJ3.2
Ioled.device.vcc: IC19.1, IJ3.28
Ioled.device.vcomh: IC16.1, IJ3.27
Ioled.iref_res.a: IJ3.26, IR9.1
Ioled.reset: IJ3.14, IU3.11
Ipacked_opamp.inn.0: IR21.2, IR22.1, IU10.2
Ipacked_opamp.inn.1: IR24.2, IR26.2, IU10.6
Ipacked_opamp.inp.1: IR25.2, IR27.2, IU10.5
Ipd.ic.vconn: IU4.12, IU4.13
Ipd.int: IU3.38, IU4.5
Ireg_3v3.boot_cap.neg: IC2.2, IL1.1, IU1.2
Ireg_3v3.boot_cap.pos: IC2.1, IU1.6
Ireg_3v3.en_res.b: IR3.2, IU1.5
Ireg_3v3.fb.output: IR1.2, IR2.1, IU1.4
Ispk_drv.i2s.sck: IU3.32, IU8.16
Ispk_drv.i2s.sd: IU3.33, IU8.1
Ispk_drv.i2s.ws: IU3.31, IU8.14
Ispk_drv.out.a: IJ4.1, IU8.9
Ispk_drv.out.b: IJ4.2, IU8.10
Itamp.input_positive: IJ5.3, IR25.1, ITP10.1
Itamp.output: IR26.1, IU3.12, IU10.7
Itp_i.output: IC30.1, IR23.2, ITP9.1, IU3.7
Iusb.A5: IJ1.A5, IU4.10, IU4.11
Iusb.B5: IJ1.B5, IU4.1, IU4.14
Iusb_chain_0.d_N: IJ1.A7, IJ1.B7, IU3.13, IU5.1
Iusb_chain_0.d_P: IJ1.A6, IJ1.B6, IU3.14, IU5.2
Iv3v3: IC5.1, IC8.1, IC9.1, IC11.1, IC12.1, IC13.1, IC17.1, IC18.1, IC20.1, IC21.1, IC31.1, ID1.1, ID2.2, IJ2.1, IJ3.6, IJ3.9, IJ3.11, IL1.2, IR1.1, IR4.1, IR5.1, IR6.1, ITP3.1, IU3.2, IU4.3, IU4.4, IU6.5, IU8.4, IU8.7, IU8.8, IU10.8
Ivfilt.output: IC29.1, IR20.2, IU3.6
Ivgate: IC7.1, IC25.1, ITP4.1, IU2.1, IU9.1
Ivsense.output: IR18.2, IR19.1, IR20.1, ITP8.1
Ivusb: IC1.1, IC3.1, IC4.1, IC6.1, IC22.1, IC23.1, IJ1.A4, IJ1.A9, IJ1.B4, IJ1.B9, IQ2.5, IQ2.6, IQ2.7, IQ2.8, IR3.1, IR7.1, ITP1.1, IU1.3, IU2.3, IU4.2
Ivusb_sense.output: IR7.2, IR8.1, IU3.39
