BerkeleyHCI/PolymorphicBlocks/examples/JacdacKeyswitch/JacdacKeyswitch.kicad_pcb

## KiCad design examples/JacdacKeyswitch/JacdacKeyswitch.kicad_pcb (2023-10-19)

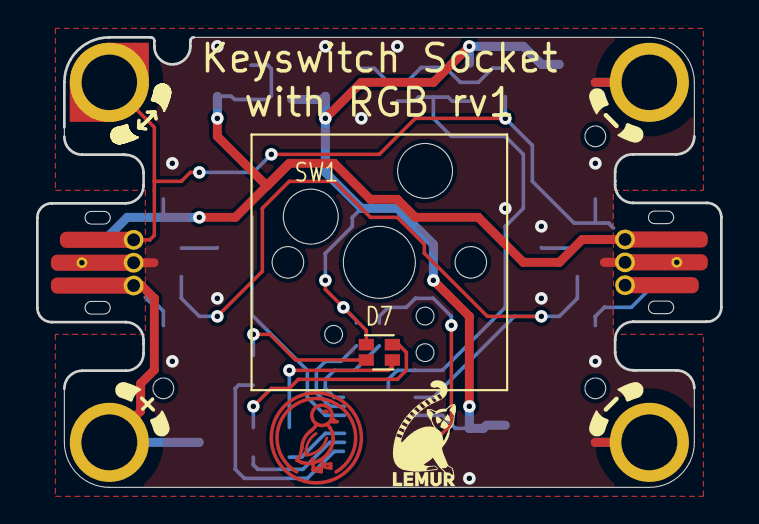
[picture p100: board JacdacKeyswitch.kicad_pcb from above]

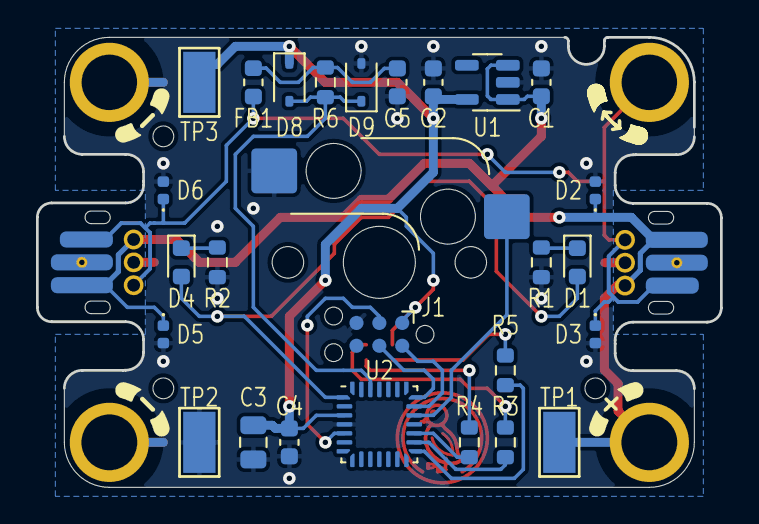
[picture p101: board JacdacKeyswitch.kicad_pcb from below]

Board: 2 copper layers, 38.0 x 25.0 mm, 39 parts (26 on the bottom side), 19 nets.

Parts:
C1, C2, C4, C5: C_0603_1608Metric
C3: C_0805_2012Metric
D1, D4: LED_0603_1608Metric
D2, D3, D5, D6: D_0402_1005Metric
D7: EAST1616RGBB2 (Everlight Electronics Co Ltd); LED_LiteOn_LTST-C19HE1WT
D8, D9: 1N5819WS (Guangdong Hottech) - 40V 600mV@1A 1A SO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; D_SOD-323
EC1, EC2: JD-PEC-02_Prerouted_recessed
FB1: L_0603_1608Metric
H1, H2, H3: JlcToolingHole_1.152mm
J1: Tag-Connect_TC2030-IDC-NL_2x03_P1.27mm_Vertical
MH1: jacdac_hole_DATA_notched_MH1
MH2: jacdac_hole_GND_MH2
MH3: jacdac_hole_PWR_MH3
MH4: jacdac_hole_GND_MH4
R1, R2, R3, R4, R5, R6: R_0603_1608Metric
SW1: PG151101S11 (Kailh); SW_Hotswap_Kailh_MX
TP1: 5015 (Keystone) - jd_pwr; TestPoint_Keystone_5015_Micro-Minature
TP2: 5015 (Keystone) - gnd; TestPoint_Keystone_5015_Micro-Minature
TP3: 5015 (Keystone) - v3v3; TestPoint_Keystone_5015_Micro-Minature
U1: XC6209F332MR-G (Torex Semiconductor Ltd); SOT-23-5
U2: STM32G031Gxxx (STMicroelectronics); QFN-28_4x4mm_P0.5mm
duck: G***; Symbol_Duckling
svg2mod: G***; Symbol_LemurSmall

Connections:
edge2.status_led.res.a: D4.1, R2.1
edge.status_led.res.a: D1.1, R1.1
gnd: C1.2, C2.2, C3.2, C4.2, C5.2, D2.2, D3.2, D5.2, D6.2, D9.2, EC1.2, EC2.2, J1.5, MH2.MH2, MH4.MH4, R1.2, R2.2, SW1.2, TP2.1, U1.2, U2.4
jd_data.jd_data: D3.1, D6.1, EC1.1, EC2.1, FB1.1, MH1.MH1
jd_if.ferrite.b: C5.1, FB1.2, R6.2
jd_if.signal: D8.2, D9.1, R6.1, U2.26
jd_pwr: C1.1, D2.1, D5.1, EC1.3, EC2.3, MH3.MH3, TP1.1, U1.1, U1.3
jd_status: D1.2, D4.2, U2.1
mcu.reset_node: J1.3, U2.5
mcu.swd_node.swclk: J1.4, U2.21
mcu.swd_node.swdio: J1.2, U2.20
rgb.blue_res.a: D7.1, R5.1
rgb.green_res.a: D7.4, R4.1
rgb.red_res.a: D7.3, R3.1
rgb.signals.blue: R5.2, U2.15
rgb.signals.green: R4.2, U2.17
rgb.signals.red: R3.2, U2.16
sw.out: SW1.1, U2.19
v3v3: C2.1, C3.1, C4.1, D7.2, D8.1, J1.1, TP3.1, U1.5, U2.3
