BerkeleyHCI/PolymorphicBlocks/examples/EspProgrammer/EspProgrammer.kicad_pcb

## KiCad design examples/EspProgrammer/EspProgrammer.kicad_pcb (2023-10-19)

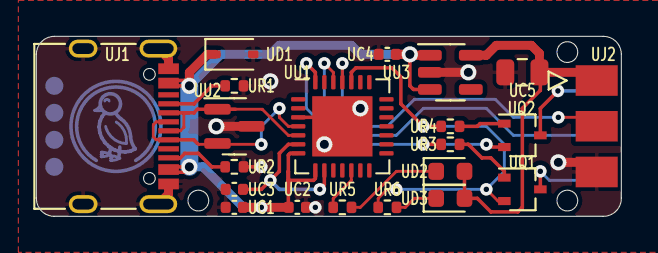
[picture p102: board EspProgrammer.kicad_pcb from above]

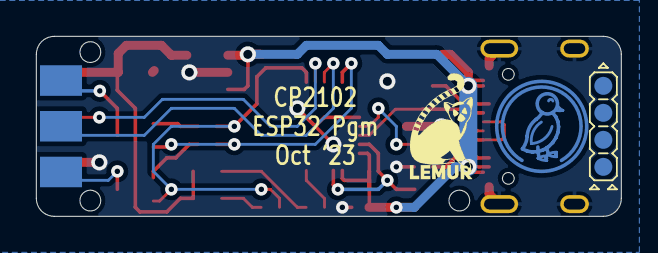
[picture p103: board EspProgrammer.kicad_pcb from below]

Board: 2 copper layers, 32.5 x 10.0 mm, 27 parts (3 on the bottom side), 19 nets.

Parts:
UC1, UC2, UC3, UC4: C_0402_1005Metric
UC5: C_0805_2012Metric
UD1: BZT52-B5V6S_R1_00001 (PANJIT International) - 100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; D_SOD-323
UD2: C2290 (Hubei KENTO Elec) - White 0603 Light Emitt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; LED_0603_1608Metric
UD3: KT-0603R (Hubei KENTO Elec) - Red 615~630nm 1.9~2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; LED_0603_1608Metric
UH1, UH2, UH3: JlcToolingHole_1.152mm
UJ1: COM-15111 (Sparkfun); USB_C_Receptacle_XKB_U262-16XN-4BVC11
UJ2: PinHeader2.54 Shrouded 2x3 (Generic); PinHeader_2x03_P2.54mm_EdgeInline
UQ1, UQ2: BC846BW 1B (CBI) - 65V 330mW 100mA 290@2mA,5V 250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; SOT-323_SC-70
UR1, UR2, UR3, UR4, UR5, UR6: R_0402_1005Metric
UU1: CP2102 (Silicon Labs); QFN-28-1EP_5x5mm_P0.5mm_EP3.35x3.35mm
UU2: PESD5V0X1BT (Nexperia); SOT-23
UU3: AP2204K-3.3 (Diodes Incorporated); SOT-23-5
UU4: Duck; Symbol_Duckling
UU5: Lemur; Symbol_LemurSmall
UU6: IdDots4; Indicator_IdDots_4

Connections:
Uauto.boot: UJ2.2, UQ2.3
Uauto.dtr_res.b: UQ1.1, UR3.2
Uauto.en: UJ2.6, UQ1.3
Uauto.rts_res.b: UQ2.1, UR4.2
Ugnd: UC1.2, UC2.2, UC3.2, UC4.2, UC5.2, UD1.2, UJ1.A1, UJ1.A12, UJ1.B1, UJ1.B12, UJ1.S1, UJ2.5, UR1.1, UR2.1, UU1.3, UU1.29, UU2.3, UU3.2
Uled.res.a: UD2.1, UR5.1
Uled_en.res.a: UD3.1, UR6.1
Uusb_chain_0.d_N: UJ1.A7, UJ1.B7, UU1.5, UU2.1
Uusb_chain_0.d_P: UJ1.A6, UJ1.B6, UU1.4, UU2.2
Uusb_uart.conn.A5: UJ1.A5, UR1.2
Uusb_uart.conn.B5: UJ1.B5, UR2.2
Uusbconv.dtr: UQ2.2, UR3.1, UU1.28
Uusbconv.ic.vdd: UC3.1, UU1.6, UU1.9
Uusbconv.rts: UQ1.2, UR4.1, UR6.2, UU1.24
Uusbconv.suspend: UR5.2, UU1.12
Uusbconv.uart.rx: UJ2.3, UU1.25
Uusbconv.uart.tx: UJ2.4, UU1.26
Uv3v3: UC5.1, UD2.2, UD3.2, UJ2.1, UU3.5
Uvusb: UC1.1, UC2.1, UC4.1, UD1.1, UJ1.A4, UJ1.A9, UJ1.B4, UJ1.B9, UU1.7, UU1.8, UU3.1, UU3.3
