BerkeleyHCI/PolymorphicBlocks/examples/PicoProbe/PicoProbe.kicad_pcb

## KiCad design examples/PicoProbe/PicoProbe.kicad_pcb (2023-10-19)

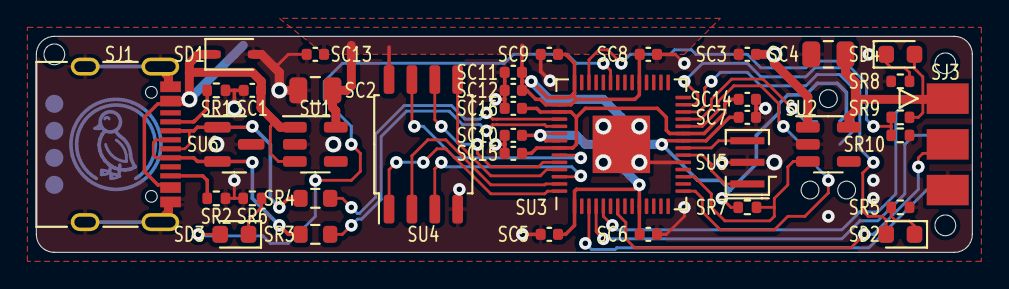
[picture p104: board PicoProbe.kicad_pcb from above]

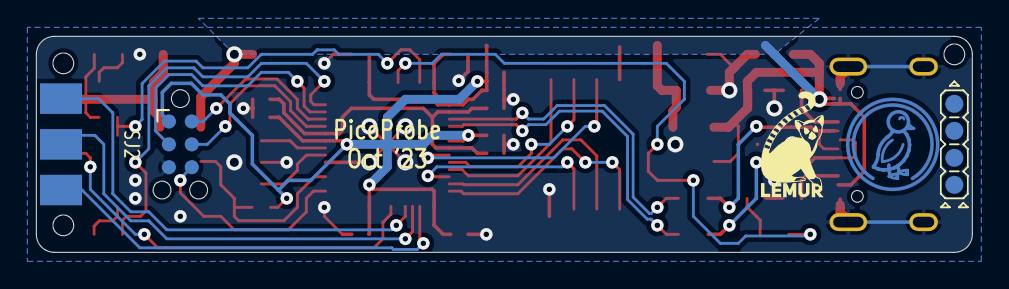
[picture p105: board PicoProbe.kicad_pcb from below]

Board: 2 copper layers, 52.0 x 12.0 mm, 45 parts (4 on the bottom side), 34 nets.

Parts:
SC1, SC3, SC5, SC6, SC7, SC8, SC9, SC10, SC11, SC12, SC13, SC14, SC15, SC16: C_0402_1005Metric
SC2, SC4: C_0805_2012Metric
SD1: BZT52-B5V6S_R1_00001 (PANJIT International) - 100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; D_SOD-323
SD2, SD4: LED_0603_1608Metric
SD3: C2290 (Hubei KENTO Elec) - White 0603 Light Emitt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; LED_0603_1608Metric
SH1, SH2, SH3: JlcToolingHole_1.152mm
SJ1: COM-15111 (Sparkfun); USB_C_Receptacle_XKB_U262-16XN-4BVC11
SJ2: Tag-Connect_TC2030-IDC-NL_2x03_P1.27mm_Vertical
SJ3: PinHeader2.54 Shrouded 2x3 (Generic); PinHeader_2x03_P2.54mm_EdgeInline
SR1, SR2, SR5, SR6, SR7, SR8, SR9, SR10: R_0402_1005Metric
SR3, SR4: R_0603_1608Metric
SU1, SU2: AP2204K-3.3 (Diodes Incorporated); SOT-23-5
SU3: RP2040 (Raspberry Pi); QFN-56-1EP_7x7mm_P0.4mm_EP3.2x3.2mm
SU4: W25Q128JVSIQ (Winbond Electronics); SOIC-8_5.23x5.23mm_P1.27mm
SU5: CSTNE12M0GH5L000R0 (Murata Electronics); Resonator_SMD_Murata_CSTxExxV-3Pin_3.0x1.1mm
SU6: PESD5V0X1BT (Nexperia); SOT-23
UU4: Duck; Symbol_Duckling
UU5: Lemur; Symbol_LemurSmall
UU6: IdDots4; Indicator_IdDots_4

Connections:
Sen_pull.io: SR7.2, SU2.3, SU3.17
Sgnd: SC1.2, SC2.2, SC3.2, SC4.2, SC5.2, SC6.2, SC7.2, SC8.2, SC9.2, SC10.2, SC11.2, SC12.2, SC13.2, SC14.2, SC15.2, SC16.2, SD1.2, SJ1.A1, SJ1.A12, SJ1.B1, SJ1.B12, SJ1.S1, SJ2.5, SJ3.5, SR1.1, SR2.1, SR5.2, SR6.2, SR8.2, SR10.2, SU1.2, SU2.2, SU3.19, SU3.57, SU4.4, SU5.2, SU6.3
Sled_target.res.a: SD4.1, SR8.1
Sled_tgt.res.a: SD2.1, SR5.1
Sled_tgt.signal: SD2.2, SU3.27
Sled_usb.res.a: SD3.1, SR6.1
Sled_usb.signal: SD3.2, SU3.37
Smcu.ic.qspi.miso: SU3.55, SU4.2
Smcu.ic.qspi.mosi: SU3.53, SU4.5
Smcu.ic.qspi.sck: SU3.52, SU4.6
Smcu.ic.qspi_cs: SU3.56, SU4.1
Smcu.ic.qspi_sd2: SU3.54, SU4.3
Smcu.ic.qspi_sd3: SU3.51, SU4.7
Smcu.ic.vreg_vout: SC14.1, SC15.1, SC16.1, SU3.23, SU3.45, SU3.50
Smcu.reset_node: SJ2.3, SU3.26
Smcu.swd.swo: SJ2.6, SU3.15
Smcu.swd_node.swclk: SJ2.4, SU3.24
Smcu.swd_node.swdio: SJ2.2, SU3.25
Smcu.usb_chain_0.d_N: SR4.1, SU3.46
Smcu.usb_chain_0.d_P: SR3.1, SU3.47
Smcu.xtal_node.driver.xtal_in: SU3.20, SU5.1
Smcu.xtal_node.driver.xtal_out: SU3.21, SU5.3
Starget.reset: SJ3.3, SU3.7
Starget.swo: SJ3.6, SU3.3
Starget_drv.swclk: SJ3.4, SU3.4
Starget_drv.swdio: SJ3.2, SU3.5
Starget_sense.output: SR9.2, SR10.1, SU3.40
Susb.conn.A5: SJ1.A5, SR1.2
Susb.conn.B5: SJ1.B5, SR2.2
Susb_chain_0.d_N: SJ1.A7, SJ1.B7, SR4.2, SU6.1
Susb_chain_0.d_P: SJ1.A6, SJ1.B6, SR3.2, SU6.2
Sv3v3: SC2.1, SC5.1, SC6.1, SC7.1, SC8.1, SC9.1, SC10.1, SC11.1, SC12.1, SC13.1, SJ2.1, SR7.1, SU1.5, SU3.1, SU3.10, SU3.22, SU3.33, SU3.42, SU3.43, SU3.44, SU3.48, SU3.49, SU4.8
Svtarget: SC4.1, SD4.2, SJ3.1, SR9.1, SU2.5
Svusb: SC1.1, SC3.1, SD1.1, SJ1.A4, SJ1.A9, SJ1.B4, SJ1.B9, SU1.1, SU1.3, SU2.1
