BerkeleyHCI/PolymorphicBlocks/examples/UsbKey/UsbKey.kicad_pcb

## KiCad design examples/UsbKey/UsbKey.kicad_pcb (2023-10-19)

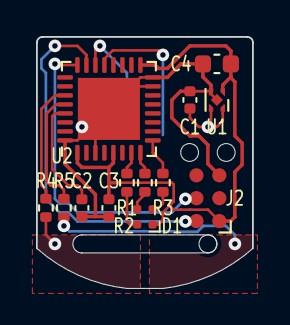
[picture p106: board UsbKey.kicad_pcb from above]

Board: 2 copper layers, 12.0 x 14.0 mm, 14 parts (1 on the bottom side), 16 nets.

Parts:
C1, C2, C3: C_0402_1005Metric
C4: C_0603_1608Metric
D1: FC-B1010RGBT-HG (Foshan NationStar Optoelectronic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; LED_Lumex_SML-LX0404SIUPGUSB
J1: USB A pads; USB_A_Pads
J2: Tag-Connect_TC2030-IDC-NL_2x03_P1.27mm_Vertical
R1, R2, R3, R4, R5: R_0402_1005Metric
U1: LP5907SNX-3.3/NOPB (Texas Instruments); UDFN-4-1EP_1x1mm_P0.65mm_EP0.48x0.48mm
U2: STM32L432Kxxx (STMicroelectronics); QFN-32-1EP_5x5mm_P0.5mm_EP3.45x3.45mm

Connections:
gnd: C1.2, C2.2, C3.2, C4.2, J1.4, J2.5, U1.2, U1.5, U2.3, U2.15, U2.16, U2.32, U2.33
mcu.swd_node.swclk: J2.4, U2.24
mcu.swd_node.swdio: J2.2, U2.23
rgb.blue_res.a: D1.4, R3.1
rgb.green_res.a: D1.3, R2.1
rgb.red_res.a: D1.2, R1.1
rgb.signals.blue: R3.2, U2.9
rgb.signals.green: R2.2, U2.8
rgb.signals.red: R1.2, U2.7
ts1.io: R4.1, U2.27
ts2.io: R5.1, U2.28
tss.io: C2.1, U2.29
usb.pwr: C1.1, J1.1, U1.3, U1.4
usb.usb.dm: J1.2, U2.21
usb.usb.dp: J1.3, U2.22
v3v3: C3.1, C4.1, D1.1, J2.1, U1.1, U2.1, U2.5, U2.17
