BerkeleyHCI/PolymorphicBlocks/examples/prerouted_blocks/Rp2040.kicad_pcb

## KiCad design examples/prerouted_blocks/Rp2040.kicad_pcb (2023-08-17)

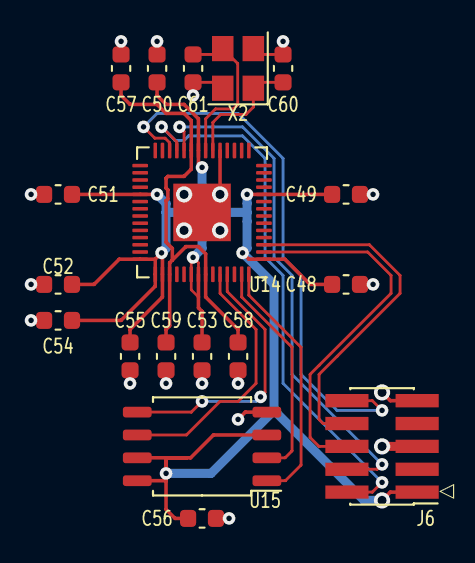
[picture p107: board Rp2040.kicad_pcb from above]

Board: 2 copper layers, 18 parts (0 on the bottom side), 14 nets.

Parts:
C48, C49, C50, C51, C52, C53, C54, C55, C56, C57, C58, C59, C60, C61: C_0603_1608Metric
J6: PinHeader1.27 Shrouded 2x5 (Generic); PinHeader_2x05_P1.27mm_Vertical_SMD
U14: RP2040 (Raspberry Pi); QFN-56-1EP_7x7mm_P0.4mm_EP3.2x3.2mm
U15: W25Q128JVSIQ (Winbond Electronics); SOIC-8_5.23x5.23mm_P1.27mm
X2: Crystal_SMD_3225-4Pin_3.2x2.5mm

Connections:
gnd: C48.2, C49.2, C50.2, C51.2, C52.2, C53.2, C54.2, C55.2, C56.2, C57.2, C58.2, C59.2, C60.2, C61.2, J6.3, J6.5, J6.9, U14.19, U14.57, U15.4, X2.2, X2.4
mcu.crystal.crystal.a: C60.1, U14.20, X2.1
mcu.crystal.crystal.b: C61.1, U14.21, X2.3
mcu.ic.qspi.miso: U14.55, U15.2
mcu.ic.qspi.mosi: U14.53, U15.5
mcu.ic.qspi.sck: U14.52, U15.6
mcu.ic.qspi_cs: U14.56, U15.1
mcu.ic.vreg_vout: C57.1, C58.1, C59.1, U14.23, U14.45, U14.50
mcu.swd.swd.reset: J6.10, U14.26
mcu.swd.swd.swclk: J6.4, U14.24
mcu.swd.swd.swdio: J6.2, U14.25
mcu.swd.swo: J6.6, U14.2
mcu.swd.tdi: J6.8, U14.3
v3v3: C48.1, C49.1, C50.1, C51.1, C52.1, C53.1, C54.1, C55.1, C56.1, J6.1, U14.1, U14.10, U14.22, U14.33, U14.42, U14.43, U14.44, U14.48, U14.49, U15.3, U15.7, U15.8
