BerkeleyHCI/PolymorphicBlocks/examples/prerouted_blocks/Esp32Camera.kicad_pcb

## KiCad design examples/prerouted_blocks/Esp32Camera.kicad_pcb (2023-08-17)

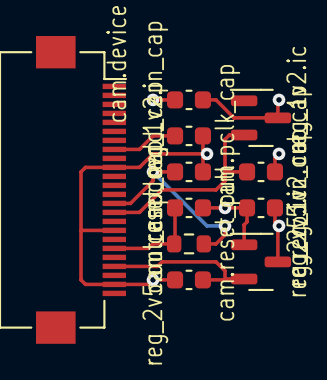
[picture p108: board Esp32Camera.kicad_pcb from above]

Board: 2 copper layers, 11 parts (0 on the bottom side), 7 nets.

Parts:
cam.device: AFC01-S24FCA-00 (Jushuo); Hirose_FH12-24S-0.5SH_1x24-1MP_P0.50mm_Horizontal
cam.dovdd_cap, cam.pclk_cap, cam.reset_cap: C_0603_1608Metric
cam.reset_pull: R_0603_1608Metric
reg_1v2.ic: XC6206P122MR-G (Torex Semiconductor Ltd); SOT-23
reg_1v2.in_cap, reg_1v2.out_cap, reg_2v5.in_cap, reg_2v5.out_cap: C_0603_1608Metric
reg_2v5.ic: XC6206P252MR (Torex Semiconductor Ltd); SOT-23

Connections:
cam.device.reset: cam.device.19, cam.reset_cap.1, cam.reset_pull.2
cam.dvp8.pclk: cam.device.8, cam.pclk_cap.1
gnd: cam.device.10, cam.device.17, cam.device.23, cam.dovdd_cap.2, cam.pclk_cap.2, cam.reset_cap.2, reg_1v2.ic.1, reg_1v2.in_cap.2, reg_1v2.out_cap.2, reg_2v5.ic.1, reg_2v5.in_cap.2, reg_2v5.out_cap.2
pwr: reg_1v2.ic.3, reg_1v2.in_cap.1, reg_2v5.ic.3, reg_2v5.in_cap.1
v1v2: cam.device.15, reg_1v2.ic.2, reg_1v2.out_cap.1
v2v5: cam.device.21, reg_2v5.ic.2, reg_2v5.out_cap.1
v3v3: cam.device.14, cam.dovdd_cap.1, cam.reset_pull.1
