BerkeleyHCI/PolymorphicBlocks/examples/prerouted_blocks/Ice40.kicad_pcb

## KiCad design examples/prerouted_blocks/Ice40.kicad_pcb (2023-08-17)

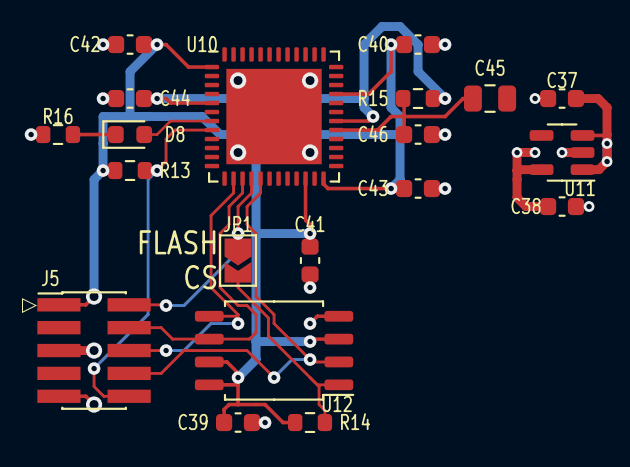
[picture p109: board Ice40.kicad_pcb from above]

Board: 2 copper layers, 20 parts (0 on the bottom side), 12 nets.

Parts:
C37, C38, C39, C40, C41, C42, C43, C44, C46: C_0603_1608Metric
C45: C_0805_2012Metric
D8: KT-0603R (Hubei KENTO Elec) - Red 615~630nm 1.9~2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; LED_0603_1608Metric
J5: PinHeader1.27 Shrouded 2x5 (Generic); PinHeader_2x05_P1.27mm_Vertical_SMD
JP1: SolderJumper-2_P1.3mm_Open_TrianglePad1.0x1.5mm
R13, R14, R15, R16: R_0603_1608Metric
U10: ICE40UP5K-SG48 (Lattice Semiconductor Corporation); QFN-48-1EP_7x7mm_P0.5mm_EP5.3x5.3mm
U11: LP5907MFX-1.2/NOPB (Texas Instruments); SOT-23-5
U12: W25Q128JVSIQ (Winbond Electronics); SOIC-8_5.23x5.23mm_P1.27mm

Connections:
cdone.res.a: D8.1, R16.1
fpga.cdone: D8.2, U10.7
fpga.cs_jmp.output: JP1.2, R14.2, U12.1
fpga.ic.creset_b: J5.10, R13.2, U10.8
fpga.ic.spi_config.miso: J5.8, U10.17, U12.2
fpga.ic.spi_config.mosi: J5.6, U10.14, U12.5
fpga.ic.spi_config.sck: J5.4, U10.15, U12.6
fpga.ic.spi_config_cs: J5.2, JP1.1, U10.16
fpga.pll_res.pwr_out: C45.1, C46.1, R15.2, U10.29
fpga.vcc_reg.pwr_out: C38.1, C44.1, R15.1, U10.5, U10.30, U11.5
gnd: C37.2, C38.2, C39.2, C40.2, C41.2, C42.2, C43.2, C44.2, C45.2, C46.2, J5.3, J5.5, J5.9, R16.2, U10.49, U11.2, U12.4
v3v3: C37.1, C39.1, C40.1, C41.1, C42.1, C43.1, J5.1, R13.1, R14.1, U10.1, U10.22, U10.24, U10.33, U11.1, U11.3, U12.3, U12.7, U12.8
