BerkeleyHCI/PolymorphicBlocks/examples/prerouted_blocks/WaveshareEpd.kicad_pcb

## KiCad design examples/prerouted_blocks/WaveshareEpd.kicad_pcb (2023-08-17)

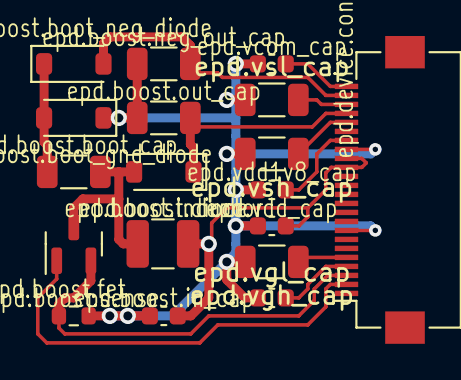
[picture p110: board WaveshareEpd.kicad_pcb from above]

Board: 2 copper layers, 18 parts (0 on the bottom side), 14 nets.

Parts:
epd.boost.boot_cap, epd.boost.neg_out_cap, epd.boost.out_cap, epd.vgh_cap, epd.vsh_cap, epd.vsl_cap: C_1206_3216Metric
epd.boost.boot_gnd_diode, epd.boost.boot_neg_diode, epd.boost.diode: B5817W (Guangdong Hottech) - 20V 450mV@1A 300mA S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; D_SOD-123
epd.boost.fet: AO3400A (Alpha & Omega Semicon) - 30V 5.7A 26.5m?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; SOT-23
epd.boost.in_cap, epd.vcom_cap, epd.vdd1v8_cap, epd.vdd_cap, epd.vgl_cap: C_0603_1608Metric
epd.boost.inductor: L_1210_3225Metric
epd.boost.sense: R_0603_1608Metric
epd.device.conn: AFC01-S24FCA-00 (Jushuo); Hirose_FH12-24S-0.5SH_1x24-1MP_P0.50mm_Horizontal

Connections:
epd.boost.boot_cap.neg: epd.boost.boot_cap.2, epd.boost.boot_gnd_diode.2, epd.boost.boot_neg_diode.1
epd.boost.inductor.b: epd.boost.boot_cap.1, epd.boost.diode.2, epd.boost.fet.3, epd.boost.inductor.2
epd.boost.neg_out: epd.boost.boot_neg_diode.2, epd.boost.neg_out_cap.2, epd.device.conn.23
epd.boost.pos_out: epd.boost.diode.1, epd.boost.out_cap.1, epd.device.conn.21
epd.device.gdr: epd.boost.fet.1, epd.device.conn.2
epd.device.rese: epd.boost.fet.2, epd.boost.sense.1, epd.device.conn.3
epd.device.vcom: epd.device.conn.24, epd.vcom_cap.1
epd.device.vdd1v8: epd.device.conn.18, epd.vdd1v8_cap.1
epd.device.vgh: epd.device.conn.5, epd.vgh_cap.1
epd.device.vgl: epd.device.conn.4, epd.vgl_cap.2
epd.device.vsh: epd.device.conn.20, epd.vsh_cap.1
epd.device.vsl: epd.device.conn.22, epd.vsl_cap.2
gnd: epd.boost.boot_gnd_diode.1, epd.boost.in_cap.2, epd.boost.neg_out_cap.1, epd.boost.out_cap.2, epd.boost.sense.2, epd.device.conn.8, epd.device.conn.17, epd.vcom_cap.2, epd.vdd1v8_cap.2, epd.vdd_cap.2, epd.vgh_cap.2, epd.vgl_cap.1, epd.vsh_cap.2, epd.vsl_cap.1
v3v3: epd.boost.in_cap.1, epd.boost.inductor.1, epd.device.conn.15, epd.device.conn.16, epd.vdd_cap.1
