BerkeleyHCI/PolymorphicBlocks/examples/RobotCrawler/RobotCrawler.kicad_pcb

## KiCad design examples/RobotCrawler/RobotCrawler.kicad_pcb (2023-08-17)

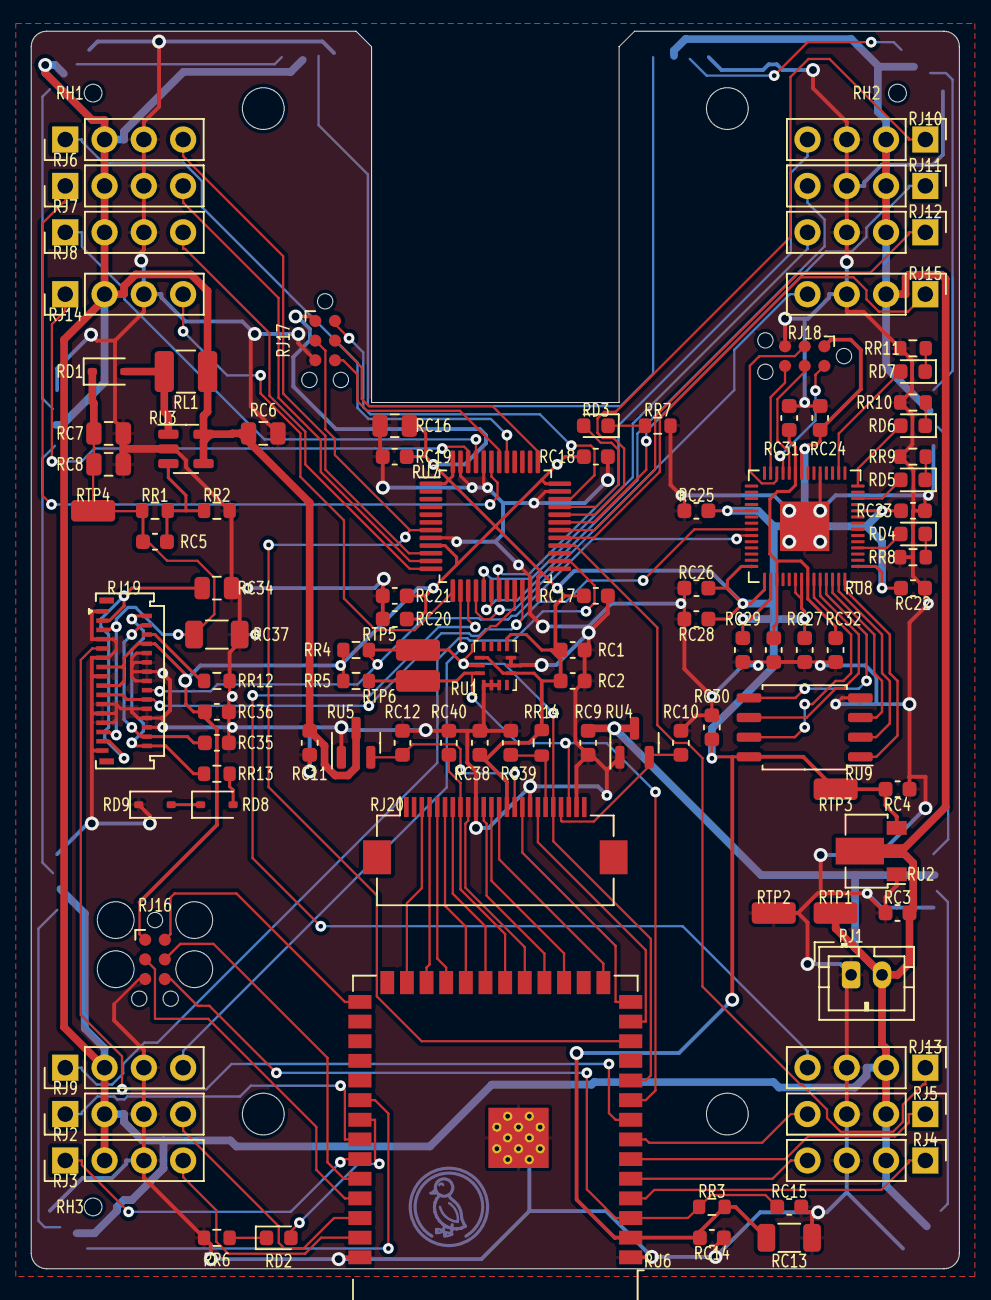
[picture p111: board RobotCrawler.kicad_pcb from above]

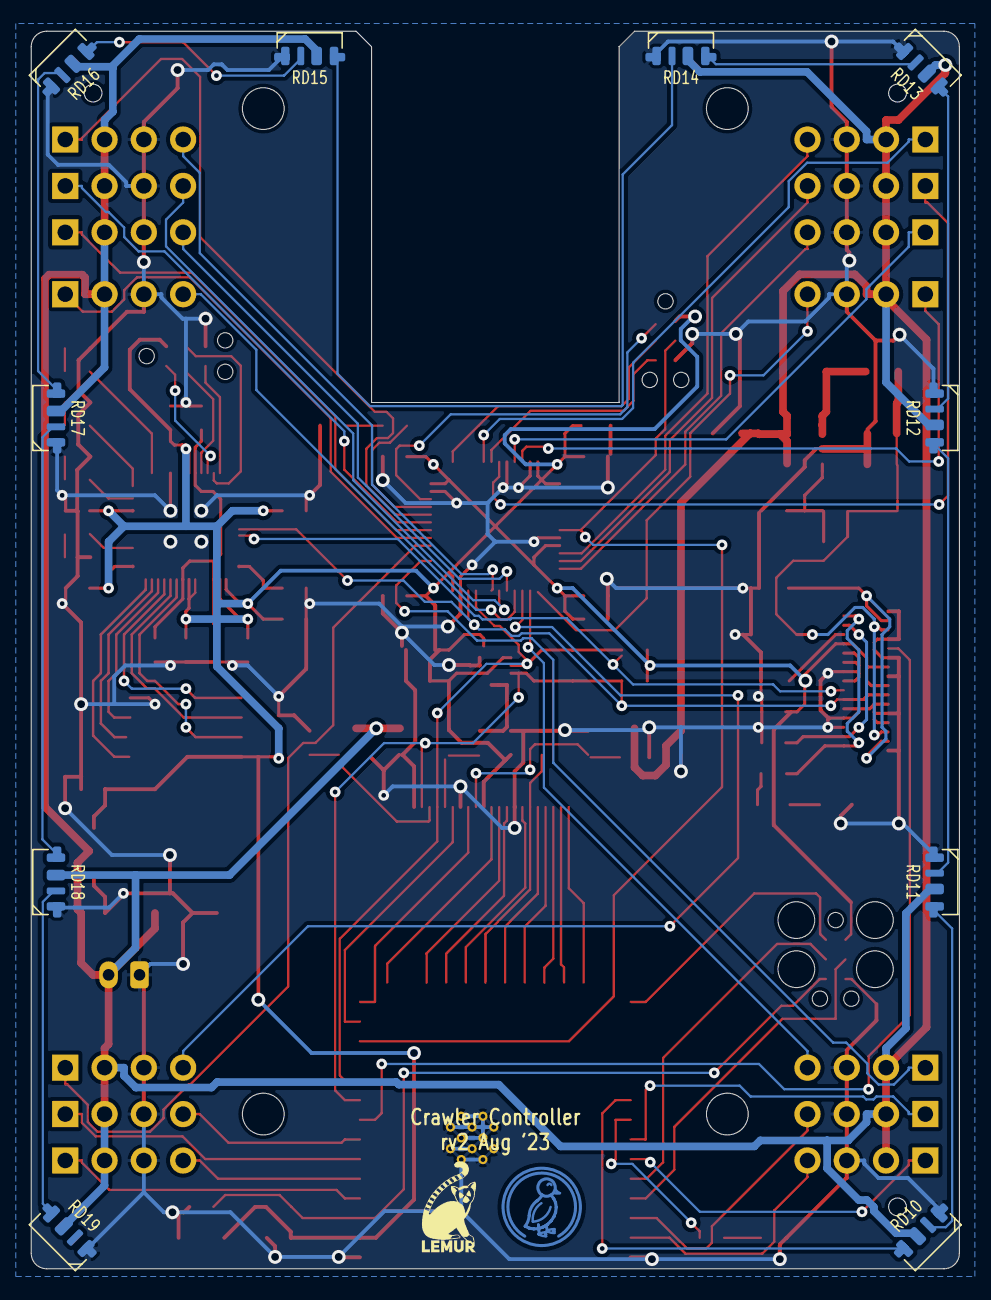
[picture p112: board RobotCrawler.kicad_pcb from below]

Board: 2 copper layers, 60.0 x 80.0 mm, 118 parts (12 on the bottom side), 99 nets.

Parts:
H10, H11, H12, H14: MountingHole_2.7mm_M2.5
RC1, RC2, RC3, RC4, RC5, RC9, RC10, RC11, RC12, RC14, RC15, RC17, RC18, RC19, RC20, RC21, RC22, RC23, RC24, RC25, RC26, RC27, RC28, RC29, RC30, RC31, RC32, RC33, RC35, RC36, RC38, RC39, RC40: C_0603_1608Metric
RC6, RC7, RC8, RC16, RC34: C_0805_2012Metric
RC13, RC37: C_1206_3216Metric
RD1: CUS10S30,H3F (TOSHIBA) - 30V 230mV@100mA 1A SOD-3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; D_SOD-323
RD2, RD3, RD4, RD5, RD6, RD7: LED_0603_1608Metric
RD8, RD9: 1N5819WS (Guangdong Hottech) - 40V 600mV@1A 1A SO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; D_SOD-323
RD10, RD11, RD12, RD13, RD14, RD15, RD16, RD17, RD18, RD19: SK6812 SIDE-A (Normand Electronic Co Ltd); LED_SK6812-SIDE-A
RH1, RH2, RH3: JlcToolingHole_1.152mm
RJ1: B2B-PH-K (JST); JST_PH_B2B-PH-K_1x02_P2.00mm_Vertical
RJ2, RJ3, RJ4, RJ5, RJ6, RJ7, RJ8, RJ9, RJ10, RJ11, RJ12, RJ13, RJ14, RJ15: PinHeader2.54 1x4 (Generic); PinHeader_1x04_P2.54mm_Vertical
RJ16: Tag-Connect_TC2030-IDC-FP_2x03_P1.27mm_Vertical
RJ17, RJ18: Tag-Connect_TC2030-IDC-NL_2x03_P1.27mm_Vertical
RJ19: FH35C-31S-0.3SHW (Hirose); Hirose_FH35C-31S-0.3SHW_1x31-1MP_P0.30mm_Horizontal
RJ20: AFC01-S24FCA-00 (Jushuo); Hirose_FH12-24S-0.5SH_1x24-1MP_P0.50mm_Horizontal
RL1: L_1210_3225Metric
RR1, RR2, RR3, RR4, RR5, RR6, RR7, RR8, RR9, RR10, RR11, RR12, RR13, RR14: R_0603_1608Metric
RTP1: 5015 (Keystone) - vbatt; TestPoint_TE_RCT_0805
RTP2: 5015 (Keystone) - gnd; TestPoint_TE_RCT_0805
RTP3: 5015 (Keystone) - v3v3; TestPoint_TE_RCT_0805
RTP4: 5015 (Keystone) - v14; TestPoint_TE_RCT_0805
RTP5: 5015 (Keystone) - i2c_chain_0.scl; TestPoint_TE_RCT_0805
RTP6: 5015 (Keystone) - i2c_tp._io_sda_link; TestPoint_TE_RCT_0805
RU1: LSM6DS3TR-C (STMicroelectronics); Bosch_LGA-14_3x2.5mm_P0.5mm
RU2: AP7215-33YG-13 (Diodes Incorporated); SOT-89-3
RU3: TPS61040DBVR (Texas Instruments); SOT-23-5
RU4: XC6206P252MR (Torex Semiconductor Ltd); SOT-23
RU5: XC6206P122MR-G (Torex Semiconductor Ltd); SOT-23
RU6: ESP32-S3-WROOM-1-N16R8 (Espressif Systems); ESP32-S3-WROOM-1
RU7: STM32F103xxT6 (STMicroelectronics); LQFP-48_7x7mm_P0.5mm
RU8: RP2040 (Raspberry Pi); QFN-56-1EP_7x7mm_P0.4mm_EP3.2x3.2mm
RU9: W25Q128JVSIQ (Winbond Electronics); SOIC-8_5.23x5.23mm_P1.27mm
UU4: Duck; Symbol_Duckling
UU5: Lemur; Symbol_LemurSmall

Connections:
Rcam.device.reset: RC39.1, RJ20.19, RR14.2
Rcam.dvp8.href: RJ20.16, RU6.14
Rcam.dvp8.pclk: RC40.1, RJ20.8, RU6.20
Rcam.dvp8.vsync: RJ20.18, RU6.13
Rcam.dvp8.xclk: RJ20.12, RU6.17
Rcam.dvp8.y0: RJ20.6, RU6.22
Rcam.dvp8.y1: RJ20.4, RU6.24
Rcam.dvp8.y2: RJ20.3, RU6.25
Rcam.dvp8.y3: RJ20.5, RU6.23
Rcam.dvp8.y4: RJ20.7, RU6.21
Rcam.dvp8.y5: RJ20.9, RU6.19
Rcam.dvp8.y6: RJ20.11, RU6.18
Rcam.dvp8.y7: RJ20.13, RU6.15
Rgnd: RC1.2, RC2.2, RC3.2, RC4.2, RC6.2, RC7.2, RC8.2, RC9.2, RC10.2, RC11.2, RC12.2, RC13.2, RC14.2, RC15.2, RC16.2, RC17.2, RC18.2, RC19.2, RC20.2, RC21.2, RC22.2, RC23.2, RC24.2, RC25.2, RC26.2, RC27.2, RC28.2, RC29.2, RC30.2, RC31.2, RC32.2, RC33.2, RC34.2, RC35.2, RC36.2, RC37.2, RC38.2, RC39.2, RC40.2, RD9.1, RD10.4, RD11.4, RD12.4, RD13.4, RD14.4, RD15.4, RD16.4, RD17.4, RD18.4, RD19.4, RJ1.1, RJ2.3, RJ3.3, RJ4.3, RJ5.3, RJ6.3, RJ7.3, RJ8.3, RJ9.3, RJ10.3, RJ11.3, RJ12.3, RJ13.3, RJ14.3, RJ15.3, RJ16.5, RJ17.5, RJ18.5, RJ19.1, RJ19.7, RJ19.10, RJ19.11, RJ19.12, RJ19.14, RJ19.15, RJ19.16, RJ19.21, RJ19.22, RJ19.23, RJ19.24, RJ19.25, RJ19.26, RJ19.31, RJ20.10, RJ20.17, RJ20.23, RR2.2, RR6.2, RR7.2, RR8.2, RR9.2, RR10.2, RR11.2, RR12.2, RTP2.1, RU1.1, RU1.2, RU1.3, RU1.6, RU1.7, RU2.1, RU3.2, RU4.1, RU5.1, RU6.1, RU6.40, RU6.41, RU7.8, RU7.23, RU7.35, RU7.44, RU7.47, RU8.19, RU8.57, RU9.4
Ri2c_chain_0.scl: RJ19.18, RJ20.20, RR4.2, RTP5.1, RU1.13, RU6.10, RU7.21, RU8.37
Ri2c_chain_0.sda: RJ19.19, RJ19.20, RJ20.22, RR5.2, RTP6.1, RU1.14, RU6.9, RU7.22, RU8.36
Rled.res.a: RD2.1, RR6.1
Rled.signal: RD2.2, RU6.33
Rmcu.program_boot_node: RJ16.2, RU6.27
Rmcu.program_en_node: RC15.1, RJ16.6, RR3.2, RU6.3
Rmcu.program_uart_node.a_tx: RJ16.3, RU6.37
Rmcu.program_uart_node.b_tx: RJ16.4, RU6.36
Rmcu_servo.reset_node: RJ17.3, RU6.12, RU7.7
Rmcu_servo.swd.swo: RJ17.6, RU7.42
Rmcu_servo.swd_node.swclk: RJ17.4, RU7.37
Rmcu_servo.swd_node.swdio: RJ17.2, RU7.34
Rmcu_test.gpio.led_0: RD4.2, RU8.4
Rmcu_test.gpio.led_1: RD5.2, RU8.12
Rmcu_test.gpio.led_2: RD6.2, RU8.14
Rmcu_test.gpio.led_3: RD7.2, RU8.16
Rmcu_test.ic.qspi.miso: RU8.55, RU9.2
Rmcu_test.ic.qspi.mosi: RU8.53, RU9.5
Rmcu_test.ic.qspi.sck: RU8.52, RU9.6
Rmcu_test.ic.qspi_cs: RU8.56, RU9.1
Rmcu_test.ic.qspi_sd2: RU8.54, RU9.3
Rmcu_test.ic.qspi_sd3: RU8.51, RU9.7
Rmcu_test.ic.vreg_vout: RC31.1, RC32.1, RC33.1, RU8.23, RU8.45, RU8.50
Rmcu_test.reset_node: RJ18.3, RU8.26
Rmcu_test.swd.swo: RJ18.6, RU8.27
Rmcu_test.swd_node.swclk: RJ18.4, RU8.24
Rmcu_test.swd_node.swdio: RJ18.2, RU8.25
Roled.device.vcomh: RC34.1, RJ19.3, RJ19.29
Roled.device.vp: RC35.1, RJ19.4, RJ19.28
Roled.device.vsl: RJ19.2, RJ19.30, RR13.1
Roled.iref_res.a: RJ19.6, RR12.1
Roled.reset: RJ19.9, RU6.8
Roled.vsl_d1.cathode: RD8.1, RD9.2
Roled.vsl_res.b: RD8.2, RR13.2
Rreg_14v.fb.output: RC5.2, RR1.2, RR2.1, RU3.3
Rreg_14v.inductor.b: RD1.2, RL1.2, RU3.1
Rrgbs.din: RD10.1, RU6.32
Rrgbs.led[0].dout: RD10.3, RD11.1
Rrgbs.led[1].dout: RD11.3, RD12.1
Rrgbs.led[2].dout: RD12.3, RD13.1
Rrgbs.led[3].dout: RD13.3, RD14.1
Rrgbs.led[4].dout: RD14.3, RD15.1
Rrgbs.led[5].dout: RD15.3, RD16.1
Rrgbs.led[6].dout: RD16.3, RD17.1
Rrgbs.led[7].dout: RD17.3, RD18.1
Rrgbs.led[8].dout: RD18.3, RD19.1
Rservo_led.res.a: RD3.1, RR7.1
Rservo_led.signal: RD3.2, RU7.33
Rservos[0].fb: RJ2.4, RU6.38
Rservos[0].pwm: RJ2.1, RU6.34
Rservos[1].fb: RJ3.4, RU6.39
Rservos[1].pwm: RJ3.1, RU6.35
Rservos[2].fb: RJ4.4, RU6.5
Rservos[2].pwm: RJ4.1, RU6.4
Rservos[3].fb: RJ5.4, RU6.7
Rservos[3].pwm: RJ5.1, RU6.6
Rservos[4].fb: RJ6.4, RU7.10
Rservos[4].pwm: RJ6.1, RU7.41
Rservos[5].fb: RJ7.4, RU7.11
Rservos[5].pwm: RJ7.1, RU7.43
Rservos[6].fb: RJ8.4, RU7.12
Rservos[6].pwm: RJ8.1, RU7.45
Rservos[7].fb: RJ9.4, RU7.14
Rservos[7].pwm: RJ9.1, RU7.26
Rservos[8].fb: RJ10.4, RU7.19
Rservos[8].pwm: RJ10.1, RU7.32
Rservos[9].fb: RJ11.4, RU7.18
Rservos[9].pwm: RJ11.1, RU7.31
Rservos[10].fb: RJ12.4, RU7.17
Rservos[10].pwm: RJ12.1, RU7.30
Rservos[11].fb: RJ13.4, RU7.15
Rservos[11].pwm: RJ13.1, RU7.28
Rservos_cam[0].fb: RJ14.4, RU7.13
Rservos_cam[0].pwm: RJ14.1, RU7.46
Rservos_cam[1].fb: RJ15.4, RU7.16
Rservos_cam[1].pwm: RJ15.1, RU7.29
Rtest_led.led[0].res.a: RD4.1, RR8.1
Rtest_led.led[1].res.a: RD5.1, RR9.1
Rtest_led.led[2].res.a: RD6.1, RR10.1
Rtest_led.led[3].res.a: RD7.1, RR11.1
Rv1v2: RC12.1, RJ20.15, RU5.2
Rv2v5: RC10.1, RJ20.21, RU4.2
Rv3v3: RC1.1, RC2.1, RC4.1, RC13.1, RC14.1, RC16.1, RC17.1, RC18.1, RC19.1, RC20.1, RC21.1, RC22.1, RC23.1, RC24.1, RC25.1, RC26.1, RC27.1, RC28.1, RC29.1, RC30.1, RC36.1, RC38.1, RJ16.1, RJ17.1, RJ18.1, RJ19.8, RJ19.13, RJ19.17, RJ20.14, RR3.1, RR4.1, RR5.1, RR14.1, RTP3.1, RU1.5, RU1.8, RU1.12, RU2.3, RU6.2, RU7.1, RU7.9, RU7.24, RU7.36, RU7.48, RU8.1, RU8.10, RU8.22, RU8.33, RU8.42, RU8.43, RU8.44, RU8.48, RU8.49, RU9.8
Rv14: RC5.1, RC7.1, RC8.1, RC37.1, RD1.1, RJ19.5, RJ19.27, RR1.1, RTP4.1
Rvbatt: RC3.1, RC6.1, RC9.1, RC11.1, RD10.2, RD11.2, RD12.2, RD13.2, RD14.2, RD15.2, RD16.2, RD17.2, RD18.2, RD19.2, RJ1.2, RJ2.2, RJ3.2, RJ4.2, RJ5.2, RJ6.2, RJ7.2, RJ8.2, RJ9.2, RJ10.2, RJ11.2, RJ12.2, RJ13.2, RJ14.2, RJ15.2, RL1.1, RTP1.1, RU2.2, RU3.4, RU3.5, RU4.3, RU5.3
