BerkeleyHCI/PolymorphicBlocks/examples/SwdDebugger/SwdDebugger.kicad_pcb

## KiCad design examples/SwdDebugger/SwdDebugger.kicad_pcb (2023-05-28)

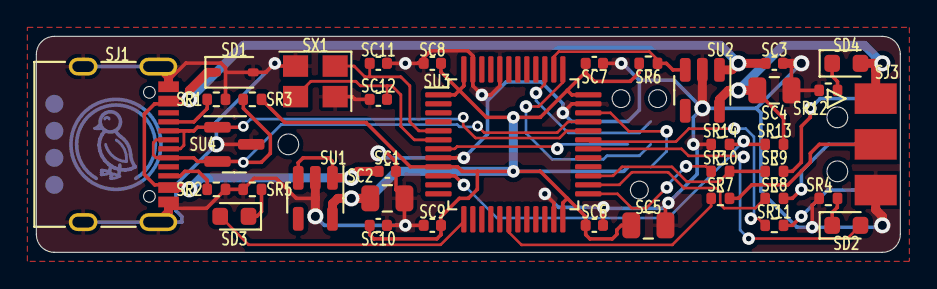
[picture p113: board SwdDebugger.kicad_pcb from above]

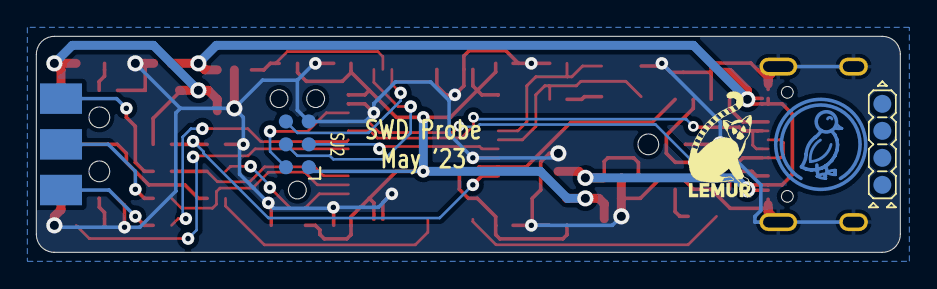
[picture p114: board SwdDebugger.kicad_pcb from below]

Board: 2 copper layers, 48.0 x 12.0 mm, 44 parts (4 on the bottom side), 30 nets.

Parts:
SC1, SC3, SC6, SC7, SC8, SC9, SC10, SC11, SC12: C_0402_1005Metric
SC2, SC4, SC5: C_0805_2012Metric
SD1: BZT52-B5V6S_R1_00001 (PANJIT International) - 100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; D_SOD-323
SD2, SD4: LED_0603_1608Metric
SD3: C2290 (Hubei KENTO Elec) - White 0603 Light Emitt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; LED_0603_1608Metric
SH1, SH2, SH3: JlcToolingHole_1.152mm
SJ1: COM-15111 (Sparkfun); USB_C_Receptacle_XKB_U262-16XN-4BVC11
SJ2: Tag-Connect_TC2030-IDC-NL_2x03_P1.27mm_Vertical
SJ3: PinHeader2.54 Shrouded 2x3 (Generic); PinHeader_2x03_P2.54mm_EdgeInline
SR1, SR2, SR3, SR4, SR5, SR6, SR7, SR8, SR9, SR10, SR11, SR12, SR13, SR14: R_0402_1005Metric
SU1, SU2: AP2204K-3.3 (Diodes Incorporated); SOT-23-5
SU3: STM32F103xxT6 (STMicroelectronics); LQFP-48_7x7mm_P0.5mm
SU4: PESD5V0X1BT (Nexperia); SOT-23
SX1: Crystal_SMD_3225-4Pin_3.2x2.5mm
UU4: Duck; Symbol_Duckling
UU5: Lemur; Symbol_LemurSmall
UU6: IdDots4; Indicator_IdDots_4

Connections:
en_pull.io: SR6.2, SU2.3, SU3.38
gnd: SC1.2, SC2.2, SC3.2, SC4.2, SC5.2, SC6.2, SC7.2, SC8.2, SC9.2, SC10.2, SC11.2, SC12.2, SD1.2, SJ1.A1, SJ1.A12, SJ1.B1, SJ1.B12, SJ1.S1, SJ2.5, SJ3.5, SR1.1, SR2.1, SR4.2, SR5.2, SR12.2, SR14.2, SU1.2, SU2.2, SU3.8, SU3.23, SU3.35, SU3.44, SU3.47, SU4.3, SX1.2, SX1.4
led_target.res.a: SD4.1, SR12.1
led_tgt.res.a: SD2.1, SR4.1
led_tgt.signal: SD2.2, SU3.30
led_usb.res.a: SD3.1, SR5.1
led_usb.signal: SD3.2, SU3.13
mcu.swd.swo: SJ2.6, SU3.39
mcu.swd_node.reset: SJ2.3, SU3.7
mcu.swd_node.swclk: SJ2.4, SU3.37
mcu.swd_node.swdio: SJ2.2, SU3.34
mcu.xtal_node.driver.xtal_in: SC11.1, SU3.5, SX1.1
mcu.xtal_node.driver.xtal_out: SC12.1, SU3.6, SX1.3
target_drv.reset_in: SR7.1, SU3.18
target_drv.swclk_in: SR8.1, SU3.26
target_drv.swd.reset: SJ3.3, SR7.2
target_drv.swd.swclk: SJ3.4, SR8.2
target_drv.swd.swdio: SJ3.2, SR9.2
target_drv.swdio_in: SR10.1, SU3.25
target_drv.swdio_out: SR9.1, SR10.2, SU3.27
target_drv.swo_in: SJ3.6, SR11.2
target_drv.swo_out: SR11.1, SU3.31
target_sense.output: SR13.2, SR14.1, SU3.10
usb.conn.A5: SJ1.A5, SR1.2
usb.conn.B5: SJ1.B5, SR2.2
usb_chain_0.d_N: SJ1.A7, SJ1.B7, SU3.32, SU4.1
usb_chain_0.d_P: SJ1.A6, SJ1.B6, SR3.2, SU3.33, SU4.2
v3v3: SC2.1, SC5.1, SC6.1, SC7.1, SC8.1, SC9.1, SC10.1, SJ2.1, SR3.1, SR6.1, SU1.5, SU3.1, SU3.9, SU3.24, SU3.36, SU3.48
vtarget: SC4.1, SD4.2, SJ3.1, SR13.1, SU2.5
vusb: SC1.1, SC3.1, SD1.1, SJ1.A4, SJ1.A9, SJ1.B4, SJ1.B9, SU1.1, SU1.3, SU2.1
