BerkeleyHCI/PolymorphicBlocks/examples/RobotDriver/RobotDriver.kicad_pcb

## KiCad design examples/RobotDriver/RobotDriver.kicad_pcb (2022-10-11)

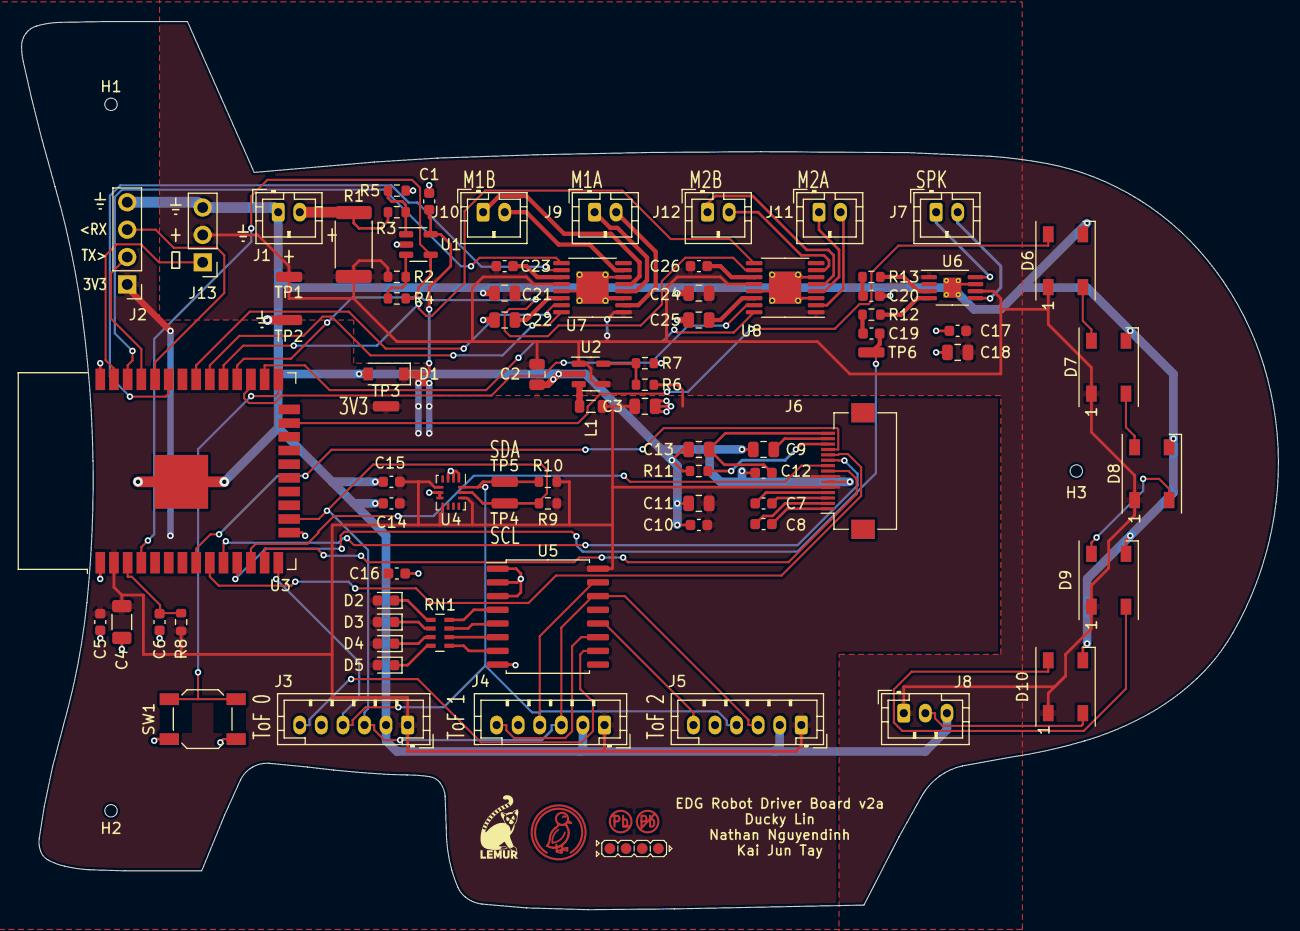
[picture p115: board RobotDriver.kicad_pcb from above]

Board: 2 copper layers, 116.5 x 82.3 mm, 86 parts (0 on the bottom side), 72 nets.

Parts:
C1, C5, C7, C8, C10, C12, C14, C15, C16, C17: C14663; C_0603_1608Metric
C2, C3, C9, C11, C18, C22, C25: C1779; C_0805_2012Metric
C4: C5672; C_1206_3216Metric
C6, C19, C20: C15849; C_0603_1608Metric
C13, C21, C24: C15850; C_0805_2012Metric
C23, C26: C57112; C_0603_1608Metric
D1: C499796; D_SOD-123
D2, D3, D4, D5: C2286; LED_0603_1608Metric
D6, D7, D8, D9, D10: C2920042; LED_WS2812B_PLCC4_5.0x5.0mm_P3.2mm
H1, H2, H3: JlcToolingHole_1.152mm
J1, J7, J9, J10, J11, J12: JST_PH_B2B-PH-K_1x02_P2.00mm_Vertical
J2: PinHeader_1x04_P2.54mm_Vertical
J3, J4, J5: JST_PH_B6B-PH-K_1x06_P2.00mm_Vertical
J6: Hirose_FH12-15S-0.5SH_1x15-1MP_P0.50mm_Horizontal
J8: JST_PH_B3B-PH-K_1x03_P2.00mm_Vertical
J13: PinHeader_1x03_P2.54mm_Vertical
L1: C98331; L_0805_2012Metric
R1: C305115; R_2512_6332Metric
R2, R3, R8: C25804; R_0603_1608Metric
R4, R5: C25811; R_0603_1608Metric
R6: C23231; R_0603_1608Metric
R7: C22809; R_0603_1608Metric
R9, R10: C23162; R_0603_1608Metric
R11: C23203; R_0603_1608Metric
R12, R13: C22984; R_0603_1608Metric
RN1: C20197; R_Array_Concave_4x0603
SW1: C318884; SW_SPST_SKQG_WithoutStem
TP1, TP2, TP3, TP4, TP5, TP6: TestPoint_TE_RCU_0603
U1: C7972; SOT-23-5
U2: C500769; SOT-23-5
U3: C701342; ESP32-WROOM-32
U4: C967633; Bosch_LGA-14_3x2.5mm_P0.5mm
U5: C86832; SOIC-16W_7.5x10.3mm_P1.27mm
U6: C27396; MSOP-8-1EP_3x3mm_P0.65mm_EP1.68x1.88mm_ThermalVias
U7, U8: C50506; TSSOP-16-1EP_4.4x5mm_P0.65mm_EP3x3mm_ThermalVias
U9: Symbol_LemurSmall
U10: Symbol_Duckling
U11: Indicator_LeadFree
U12: Indicator_IdDots_4

Connections:
batt.pins.2: J1.2, R1.1, R3.1
expander.io.led_1: RN1.7, U5.5
expander.io.led_2: RN1.6, U5.6
expander.io.tof_xshut_0: J3.6, U5.10
expander.io.tof_xshut_1: J4.6, U5.11
gnd: C1.2, C2.2, C3.2, C4.2, C5.2, C6.2, C9.2, C10.2, C11.2, C12.2, C13.2, C14.2, C15.2, C16.2, C17.2, C18.2, C20.2, C21.2, C22.2, C24.2, C25.2, D1.2, D6.3, D7.3, D8.3, D9.3, D10.3, J1.1, J2.4, J3.2, J4.2, J5.2, J6.6, J8.3, J13.3, R5.1, R7.2, R11.2, SW1.1, TP2.1, U1.2, U2.2, U3.1, U3.15, U3.38, U3.39, U4.1, U4.2, U4.3, U4.6, U4.7, U5.1, U5.2, U5.3, U5.8, U6.7, U6.9, U7.3, U7.6, U7.13, U7.17, U8.3, U8.6, U8.13, U8.17
i2c_chain_0.scl: J3.3, J4.3, J5.3, R9.2, TP4.1, U3.16, U4.13, U5.14
i2c_chain_0.sda: J3.4, J4.4, J5.4, R10.2, TP5.1, U3.14, U4.14, U5.15
isense.amp.(adapter)r2.b.src: R3.2, R5.2, U1.1
isense.amp.(adapter)rf.b.src: R2.2, R4.2, U1.3
lcd.c1_cap.pos: C7.1, J6.3
lcd.c2_cap.pos: C8.1, J6.1
lcd.device.c1n: C7.2, J6.4
lcd.device.c2n: C8.2, J6.2
lcd.device.iref: J6.13, R11.1
lcd.spi.mosi: J6.12, U3.8
lcd.spi.sck: J6.11, U3.9
lcd.vcc_cap2.pwr: C12.1, C13.1, J6.15
lcd.vcomh_cap.pos: C9.1, J6.14
led_pixel.pins.2: D10.2, J8.2
led_res.a.0: D2.1, RN1.1
led_res.a.1: D3.1, RN1.2
led_res.a.2: D4.1, RN1.3
led_res.a.3: D5.1, RN1.4
led_res.b.0: RN1.8, U5.4
leds.signals.3: RN1.5, U5.7
m1_a.pins.1: J9.1, U7.4
m1_a.pins.2: J9.2, U7.2
m1_b.pins.1: J10.1, U7.5
m1_b.pins.2: J10.2, U7.7
m2_a.pins.1: J11.1, U8.4
m2_a.pins.2: J11.2, U8.2
m2_b.pins.1: J12.1, U8.5
m2_b.pins.2: J12.2, U8.7
mcu.adc.isense: R4.1, U1.4, U3.4
mcu.gpio.lcd_cs: J6.8, U3.13
mcu.gpio.lcd_dc: J6.10, U3.10
mcu.gpio.lcd_reset: J6.9, U3.12
mcu.gpio.ledArray: D6.4, U3.23
mcu.gpio.motor_1a1: U3.30, U7.16
mcu.gpio.motor_1a2: U3.31, U7.15
mcu.gpio.motor_1b1: U3.36, U7.9
mcu.gpio.motor_1b2: U3.33, U7.10
mcu.gpio.motor_2a1: U3.26, U8.16
mcu.gpio.motor_2a2: U3.27, U8.15
mcu.gpio.motor_2b1: U3.29, U8.9
mcu.gpio.motor_2b2: U3.28, U8.10
mcu.ic.chip_pu: C6.1, R8.2, U3.3
mcu.ic.io0: SW1.2, U3.25
mcu.ic.uart0.tx: J2.2, U3.35
mcu.uart0.uart.tx: J2.3, U3.34
motor_driver1.ic.vcp: C23.1, U7.11
motor_driver1.vint_cap.pwr: C22.1, U7.14
motor_driver2.ic.vcp: C26.1, U8.11
motor_driver2.vint_cap.pwr: C25.1, U8.14
reg_3v3.fb.output: R6.2, R7.1, U2.5
reg_3v3.ic.sw: L1.1, U2.3
servo.pins.1: J13.1, U3.37
spk_chain_0: C19.2, TP6.1, U3.11
spk_chain_1.a: J7.1, U6.8
spk_chain_1.b: J7.2, U6.5
spk_drv.(adapter)inn_res.b.src: R13.2, U6.3
spk_drv.(adapter)inp_res.b.src: R12.2, U6.4
spk_drv.inn_cap.pos: C20.1, R13.1
spk_drv.inp_res.a: C19.1, R12.1
tof.xshut.2: J5.6, U5.12
v3v3: C1.1, C3.1, C4.1, C5.1, C10.1, C11.1, C14.1, C15.1, C16.1, D1.1, D2.2, D3.2, D4.2, D5.2, J2.1, J3.1, J4.1, J5.1, J6.5, J6.7, L1.2, R6.1, R8.1, R9.1, R10.1, TP3.1, U1.5, U3.2, U4.5, U4.8, U4.12, U5.16
vbatt: C2.1, C17.1, C18.1, C21.1, C23.2, C24.1, C26.2, D6.1, D7.1, D8.1, D9.1, D10.1, J8.1, J13.2, R1.2, R2.1, TP1.1, U2.1, U2.4, U6.1, U6.6, U7.1, U7.12, U8.1, U8.12
ws2812bArray.led[1].din: D6.2, D7.4
ws2812bArray.led[1].dout: D7.2, D8.4
ws2812bArray.led[3].din: D8.2, D9.4
ws2812bArray.led[3].dout: D9.2, D10.4
