BerkeleyHCI/PolymorphicBlocks/examples/TofArray/TofArray.kicad_pcb

## KiCad design examples/TofArray/TofArray.kicad_pcb (2022-07-25)

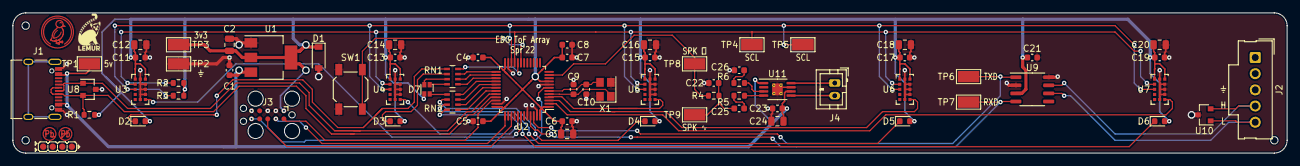
[picture p116: board TofArray.kicad_pcb from above]

Board: 2 copper layers, 200.0 x 22.0 mm, 74 parts (0 on the bottom side), 47 nets.

Parts:
1: Indicator_LeadFree
2: Indicator_IdDots_4
C1, C4, C5, C6, C11, C13, C15, C17, C19, C21, C23: C14663; C_0603_1608Metric
C2, C3, C12, C14, C16, C18, C20, C24: C1779; C_0805_2012Metric
C7: C57112; C_0603_1608Metric
C8, C25, C26: C15849; C_0603_1608Metric
C9, C10: C1663; C_0603_1608Metric
C22: C1622; C_0603_1608Metric
D1: C499796; D_SOD-123
D2, D3, D4, D5, D6: C2286; LED_0603_1608Metric
D7: C264517; LED_LiteOn_LTST-C19HE1WT
H1, H2, H3: JlcToolingHole_1.152mm
J1: C165948; USB_C_Receptacle_XKB_U262-16XN-4BVC11
J2: Molex_SL_171971-0005_1x05_P2.54mm_Vertical
J3: Tag-Connect_TC2050-IDC-FP_2x05_P1.27mm_Vertical
J4: JST_PH_B2B-PH-K_1x02_P2.00mm_Vertical
R1: C22843; R_0603_1608Metric
R2, R3: C23162; R_0603_1608Metric
R4: C21190; R_0603_1608Metric
R5, R6: C22984; R_0603_1608Metric
RN1, RN2: C20197; R_Array_Concave_4x0603
SW1: C318884; SW_SPST_SKQG_WithoutStem
TP1, TP2, TP3, TP4, TP5, TP6, TP7, TP8, TP9: C238130; TestPoint_Keystone_5015_Micro-Minature
U1: C86781; SOT-223-3_TabPin2
U2: C8734; LQFP-48_7x7mm_P0.5mm
U3, U4, U5, U6, U7: C91199; ST_VL53L0X
U8: C87911; SOT-23
U9: C12084; SO-8_3.9x4.9mm_P1.27mm
U10: SOT-23
U11: C27396; MSOP-8-1EP_3x3mm_P0.65mm_EP1.68x1.88mm_ThermalVias
U12: Symbol_Duckling
U13: Symbol_LemurSmall
X1: C9002; Crystal_SMD_3225-4Pin_3.2x2.5mm

Connections:
can_chain_0.rxd: TP7.1, U2.45, U9.4
can_chain_0.txd: TP6.1, U2.46, U9.1
can_chain_1.canh: J2.4, U9.7, U10.2
can_chain_1.canl: J2.5, U9.6, U10.1
gnd: C1.2, C2.2, C3.2, C4.2, C5.2, C6.2, C7.2, C8.2, C9.2, C10.2, C11.2, C12.2, C13.2, C14.2, C15.2, C16.2, C17.2, C18.2, C19.2, C20.2, C21.2, C22.2, C23.2, C24.2, C26.2, D1.2, J1.A1, J1.A12, J1.B1, J1.B12, J2.3, J3.2, J3.3, J3.5, SW1.1, TP2.1, U1.1, U2.8, U2.23, U2.35, U2.44, U2.47, U3.2, U3.3, U3.4, U3.6, U3.12, U4.2, U4.3, U4.4, U4.6, U4.12, U5.2, U5.3, U5.4, U5.6, U5.12, U6.2, U6.3, U6.4, U6.6, U6.12, U7.2, U7.3, U7.4, U7.6, U7.12, U8.3, U9.2, U9.8, U10.3, U11.7, U11.9, X1.2, X1.4
i2c_chain_0.scl: R2.2, TP4.1, U2.21, U3.10, U4.10, U5.10, U6.10, U7.10
i2c_chain_0.sda: R3.2, TP5.1, U2.22, U3.9, U4.9, U5.9, U6.9, U7.9
leds_chain_0.0: RN1.8, U2.20
leds_chain_0.1: RN1.7, U2.25
leds_chain_0.2: RN2.7, U2.29
leds_chain_0.3: RN2.6, U2.30
leds_chain_0.4: RN2.5, U2.31
leds_chain_0.5: RN1.6, U2.26
leds_chain_0.6: RN1.5, U2.27
leds_chain_0.7: RN2.8, U2.28
mcu.crystal.crystal.a: C9.1, U2.5, X1.1
mcu.gpio.tof_xshut_1: U2.41, U4.5
mcu.gpio.tof_xshut_2: U2.4, U5.5
mcu.gpio.tof_xshut_3: U2.3, U6.5
mcu.ic.osc.xtal_out: C10.1, U2.6, X1.3
mcu.ic.swd.swclk: J3.9, U2.37
mcu.ic.swd.swo: J3.8, U2.39
mcu.swd.swd.reset: J3.6, U2.7
mcu.swd.swd.swdio: J3.10, U2.34
res1.a.0: D2.1, RN1.1
res1.a.1: D3.1, RN1.2
res1.a.2: D7.3, RN1.3
res1.a.3: D7.4, RN1.4
res2.a.0: D7.1, RN2.1
res2.a.1: D4.1, RN2.2
res2.a.2: D5.1, RN2.3
res2.a.3: D6.1, RN2.4
spk_chain_0: R4.1, TP8.1, U2.11
spk_chain_1: C22.1, C25.2, R4.2, TP9.1
spk_chain_2.a: J4.1, U11.8
spk_chain_2.b: J4.2, U11.5
spk_drv.(adapter)inn_res.b.src: R6.2, U11.3
spk_drv.(adapter)inp_res.b.dst: R5.2, U11.4
spk_drv.inn_cap.pos: C26.1, R6.1
spk_drv.inp_res.a: C25.1, R5.1
sw1_chain_0: SW1.2, U2.19
tof.xshut.0: U2.42, U3.5
tof.xshut.4: U2.2, U7.5
usb_chain_0.d_N: J1.A7, J1.B7, U2.32, U8.1
usb_chain_0.d_P: J1.A6, J1.B6, R1.2, U2.33, U8.2
v3v3: C2.1, C3.1, C4.1, C5.1, C6.1, C7.1, C8.1, C11.1, C12.1, C13.1, C14.1, C15.1, C16.1, C17.1, C18.1, C19.1, C20.1, C21.1, D1.1, D2.2, D3.2, D4.2, D5.2, D6.2, D7.2, J3.1, R1.1, R2.1, R3.1, TP3.1, U1.2, U2.1, U2.9, U2.24, U2.36, U2.48, U3.1, U3.11, U4.1, U4.11, U5.1, U5.11, U6.1, U6.11, U7.1, U7.11, U9.3
vusb: C1.1, C23.1, C24.1, J1.A4, J1.A9, J1.B4, J1.B9, TP1.1, U1.3, U11.1, U11.6
