BerkeleyHCI/PolymorphicBlocks/examples/LedMatrix/LedMatrix.kicad_pcb

## KiCad design examples/LedMatrix/LedMatrix.kicad_pcb (2022-06-11)

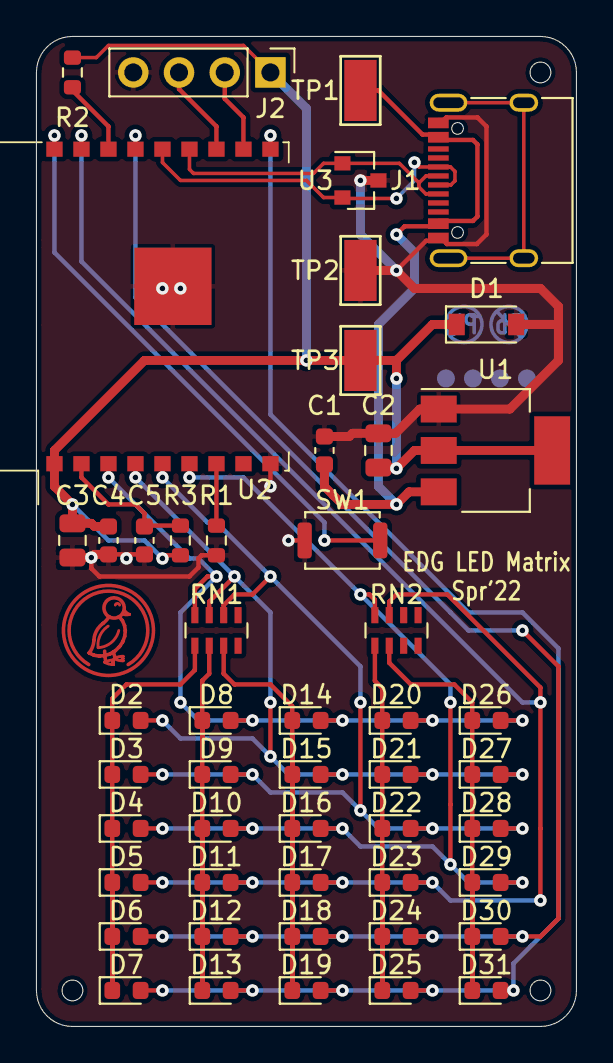
[picture p117: board LedMatrix.kicad_pcb from above]

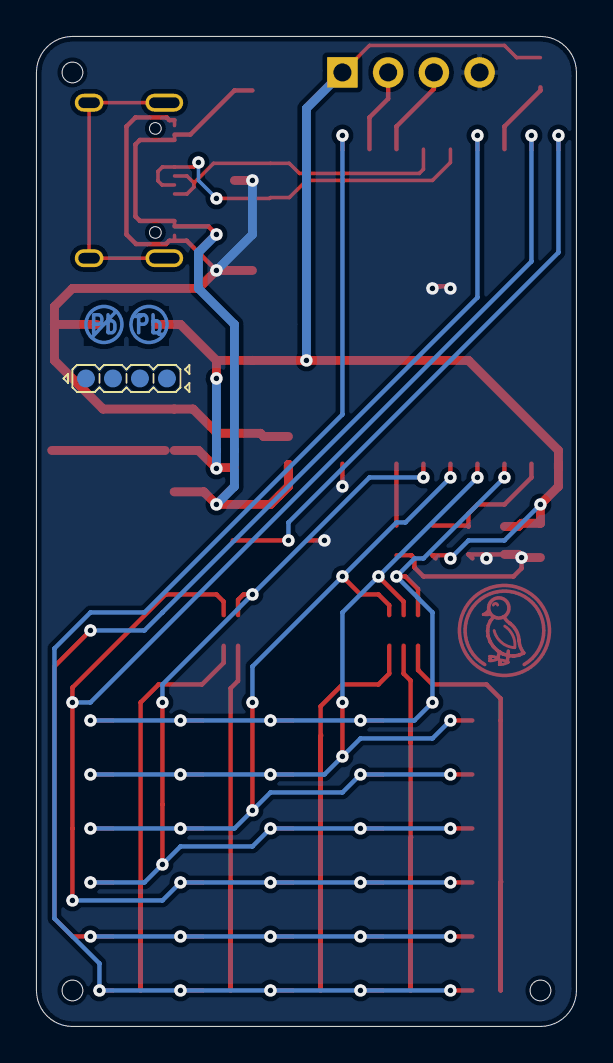
[picture p118: board LedMatrix.kicad_pcb from below]

Board: 2 copper layers, 30.0 x 55.0 mm, 56 parts (2 on the bottom side), 23 nets.

Parts:
1: Indicator_LeadFree
2: Indicator_IdDots_4
C1, C4: C14663; C_0603_1608Metric
C2: C1779; C_0805_2012Metric
C3: C15850; C_0805_2012Metric
C5: C15849; C_0603_1608Metric
D1: C499796; D_SOD-123
D2, D3, D4, D5, D6, D7, D8, D9, D10, D11, D12, D13, D14, D15, D16, D17, D18, D19, D20, D21, D22, D23, D24, D25, D26, D27, D28, D29, D30, D31: C72038; LED_0603_1608Metric
H1, H2, H3: JlcToolingHole_1.152mm
J1: C165948; USB_C_Receptacle_XKB_U262-16XN-4BVC11
J2: PinHeader_1x04_P2.54mm_Vertical
R1, R2, R3: C25804; R_0603_1608Metric
RN1, RN2: C425057; R_Array_Concave_4x0603
SW1: SW_Push_SPST_NO_Alps_SKRK
TP1, TP2, TP3: C238130; TestPoint_Keystone_5015_Micro-Minature
U1: C86781; SOT-223-3_TabPin2
U2: C2934560; ESP-WROOM-02
U3: C87911; SOT-23
U4: Symbol_Duckling

Connections:
gnd: C1.2, C2.2, C3.2, C4.2, C5.2, D1.2, J1.A1, J1.A12, J1.B1, J1.B12, J2.4, R1.1, SW1.1, TP2.1, U1.1, U2.9, U2.19, U3.3
matrix.ios.5: D6.2, D12.2, D18.2, D24.2, D30.2, U2.15
matrix.ios.6: D7.2, D13.2, D19.2, D25.2, D31.2, U2.10
matrix_res1.a.0: D2.1, D3.1, D4.1, D5.1, D6.1, D7.1, RN1.1
matrix_res1.a.1: D8.1, D9.1, D10.1, D11.1, D12.1, D13.1, RN1.2
matrix_res1.a.2: D14.1, D15.1, D16.1, D17.1, D18.1, D19.1, RN1.3
matrix_res1.b.1: D2.2, D15.2, D21.2, D27.2, RN1.7, U2.4
matrix_res2.a.0: D20.1, D21.1, D22.1, D23.1, D24.1, D25.1, RN2.1
matrix_res2.a.1: D26.1, D27.1, D28.1, D29.1, D30.1, D31.1, RN2.2
mcu.en_pull.output: C5.1, R3.2, U2.2
mcu.gpio.led_0: D8.2, D14.2, D20.2, D26.2, RN1.8, U2.3
mcu.gpio.led_2: D3.2, D9.2, D22.2, D28.2, RN1.6, U2.5
mcu.gpio.led_3: D4.2, D10.2, D16.2, D29.2, RN2.8, U2.6
mcu.gpio.led_4: D5.2, D11.2, D17.2, D23.2, RN2.7, U2.17
mcu.gpio.sw1: SW1.2, U2.18
mcu.ic.uart0.rx: J2.2, U2.11
mcu.io2_pull.io: R2.2, U2.16
mcu.io8_pull.b: R1.2, U2.7
mcu.uart0.uart.rx: J2.3, U2.12
usb.usb.dp: J1.A6, J1.B6, U2.14, U3.2
usb_esd.usb.dm: J1.A7, J1.B7, U2.13, U3.1
v3v3: C2.1, C3.1, C4.1, D1.1, J2.1, R2.1, R3.1, TP3.1, U1.2, U2.1
vusb: C1.1, J1.A4, J1.A9, J1.B4, J1.B9, TP1.1, U1.3
