BerkeleyHCI/PolymorphicBlocks/examples/Multimeter/Multimeter.kicad_pcb

## KiCad design examples/Multimeter/Multimeter.kicad_pcb (2022-05-06)

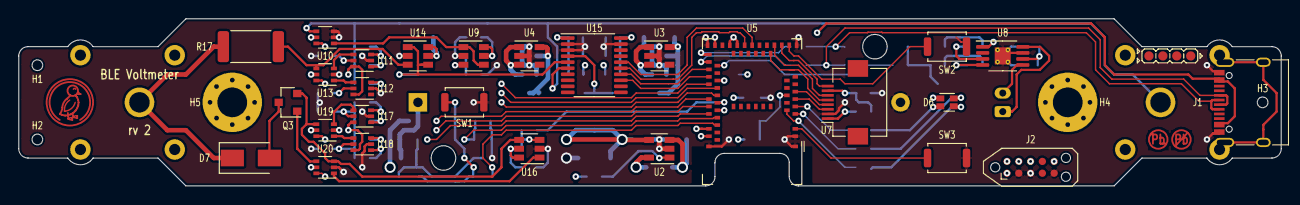
[picture p119: board Multimeter.kicad_pcb from above]

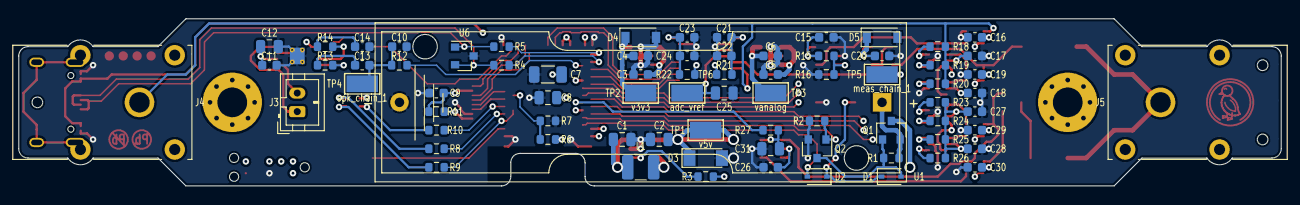
[picture p120: board Multimeter.kicad_pcb from below]

Board: 4 copper layers, 136.0 x 18.0 mm, 111 parts (76 on the bottom side), 80 nets.

Parts:
1: LeadFree; Indicator_LeadFree
2: IdDots4; Indicator_IdDots_4
C1, C8, C25: X5R 25V ±10% 10uF 0805 Multilayer Ceramic Capacit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; C_0805_2012Metric
C2, C12: 25V 4.7uF X5R ±10% 0805 Multilayer Ceramic Capaci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; C_0805_2012Metric
C3, C4, C5, C6, C9, C13, C14: 50V 1uF X5R ±10% 0603 Multilayer Ceramic Capacito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; C_0603_1608Metric
C7: 50V 10uF X5R ±10% 1206 Multilayer Ceramic Capacit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; C_1206_3216Metric
C10: 50V 47nF X7R ±10% 0603 Multilayer Ceramic Capacit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; C_0603_1608Metric
C11, C15, C16, C17, C18, C19, C20, C21, C22, C23, C24, C26, C27, C28, C29, C30: 50V 100nF X7R ±10% 0603 Multilayer Ceramic Capaci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; C_0603_1608Metric
C31: 50V 2.2uF Y5V ±20% 0805 Multilayer Ceramic Capaci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; C_0805_2012Metric
D1, D2: 30V 370mV@1mA 30mA SOD-323 Schottky Barrier Diode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; D_SOD-323
D3: 100nA@1V 25Ω Single 5.2V~6V 500mW 5.6V LL-34 Zene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; D_MiniMELF
D4, D5: 5μA@1V 90Ω Single 3.6V~3.8V 350mW 3.4V SOD-123 Ze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; D_SOD-123
D6: LED_LiteOn_LTST-C19HE1WT
D7: DIODE GEN PURP 400V 1A DO214AC; D_SMA
H1, H2, H3: JlcToolingHole_1.152mm
H4, H5: M3; MountingHole_3.2mm_M3_Pad_Via
J1: USB_C_Receptacle_XKB_U262-16XN-4BVC11
J2: SWD; Tag-Connect_TC2050-IDC-NL_2x05_P1.27mm_Vertical
J3: JST_PH_B2B-PH-K_1x02_P2.00mm_Vertical
J4, J5: CLIFF_FCR7350
L1: 620mA 22uH ±10% 270mΩ 1210 Inductors (SMD) ROHS; L_1210_3225Metric
Q1: 20V 3.1A 860mW 112mΩ@4.5V,2.8A 1V@250μA P Channel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; SOT-23
Q2: 60V 115mA 200mW 7.5Ω@10V,500mA 2.5V@250μA N Chann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; SOT-23
Q3: MOSFET P-CH 250V 140MA SC-59-3; SOT-23
R1, R2, R3, R6, R7, R8, R9, R10, R12, R13, R14, R15, R16, R18, R19, R20, R23, R24, R25, R26, R27: ±1% 1/10W Thick Film Resistors 75V ±100ppm/℃ -55℃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; R_0603_1608Metric
R4, R5, R11: ±1% 1/10W Thick Film Resistors 75V ±200ppm/℃ -55℃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; R_0603_1608Metric
R17: 1M, 1%, 1.0 W; R_2512_6332Metric
R21, R22: ±1% 1/10W Thick Film Resistors 75V ±400ppm/℃ -55℃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; R_0603_1608Metric
SW1, SW2, SW3: SW_Push_SPST_NO_Alps_SKRK
TP1: v5v; TestPoint_Keystone_5015_Micro-Minature
TP2: v3v3; TestPoint_Keystone_5015_Micro-Minature
TP3: vanalog; TestPoint_Keystone_5015_Micro-Minature
TP4: spk_chain_1; TestPoint_Keystone_5015_Micro-Minature
TP5: meas_chain_1; TestPoint_Keystone_5015_Micro-Minature
TP6: adc_vref; TestPoint_Keystone_5015_Micro-Minature
U1: BatteryHolder_Keystone_2460_1xAA
U2, U3, U4: SOT-23-5
U5: Raytac_MDBT50Q
U6: SOT-23
U7: Hirose_FH12-8S-0.5SH_1x08-1MP_P0.50mm_Horizontal
U8: MSOP-8-1EP_3x3mm_P0.65mm_EP1.73x1.85mm_ThermalVias
U9, U14, U16: SOT-23-6
U10, U11, U12, U13, U17, U18, U19, U20: SOT-363_SC-70-6
U15: TSSOP-20_4.4x6.5mm_P0.65mm
U21: Duck; Symbol_Duckling

Connections:
(adapter)inp.port.src: D7.1, J5.1, R17.1
adc.dvdd_res.b: C23.1, C24.1, R22.2, U15.20
adc.ic.avdd: C21.1, C22.1, R21.2, U15.1
adc.spi.miso: U5.24, U15.16
adc.spi.mosi: U5.26, U15.15
adc.spi.sck: U5.37, U15.14
adc_vref: C25.1, TP6.1, U15.4
data_usb.A4: C7.1, J1.A4, J1.A9, J1.B4, J1.B9, U5.32
data_usb.usb.dm: J1.A7, J1.B7, R5.2, U6.1
data_usb.usb.dp: J1.A6, J1.B6, R4.2, U6.2
driver.control: C31.1, R27.2, U16.3
driver.fet.drain: D7.2, Q3.3
driver.range.switch.inputs.0: R23.2, U17.3
driver.range.switch.inputs.1: R24.2, U17.1
driver.range.switch.inputs.2: R25.2, U18.3
driver.range.switch.inputs.3: R26.2, U18.1
driver.range.switch.sw[1_0].inputs.0: U17.4, U19.3
driver.range.switch.sw[1_0].inputs.1: U18.4, U19.1
driver.select.0_0: U5.46, U17.6, U18.6
driver.sw.inputs.0: Q3.2, U16.4, U19.4, U20.3
driver.sw.inputs.1: U16.1, U20.1
driver.sw.out: Q3.1, U20.4
gate.amp_fet.drain: D1.2, Q1.1, Q2.3, R1.2
gate.ctl_diode.cathode: D1.1, D2.1, SW1.2
gate.pwr_out: C1.1, L1.1, Q1.3, R3.1, R6.1, U2.3
gnd: C1.2, C2.2, C3.2, C4.2, C5.2, C6.2, C7.2, C8.2, C9.2, C10.2, C11.2, C12.2, C14.2, C15.2, C16.2, C17.2, C18.2, C19.2, C20.2, C21.2, C22.2, C23.2, C24.2, C25.2, C26.2, C27.2, C28.2, C29.2, C30.2, C31.2, D3.2, D4.2, D5.2, J1.A1, J1.A12, J1.B1, J1.B12, J2.2, J2.3, J2.5, Q2.2, R2.2, R7.2, R16.2, SW1.1, SW2.1, SW3.1, U1.2, U2.2, U3.2, U4.2, U5.1, U5.2, U5.15, U5.33, U5.55, U6.3, U7.2, U8.7, U8.9, U9.2, U10.2, U10.3, U11.2, U12.2, U13.2, U14.2, U15.2, U15.3, U15.19, U16.2, U17.2, U18.2, U19.2, U20.2
inn_merge.inputs.0: J4.1, R18.1, R19.1, R20.1, U10.4, U15.6
inn_mux.control.0: U5.41, U10.6
lcd.led_res.b: R11.2, U7.1
lcd.spi.mosi: U5.19, U7.5
lcd.spi.sck: U5.18, U7.6
mcu.adc.vbatsense: R6.2, R7.1, U5.9
mcu.gpio.adc_cs: U5.39, U15.13
mcu.gpio.driver_control: R27.1, U5.45
mcu.gpio.driver_enable: U5.48, U20.6
mcu.gpio.driver_select_1_0: U5.44, U19.6
mcu.gpio.gate_control: Q2.1, R2.1, U5.49
mcu.gpio.lcd_cs: U5.17, U7.8
mcu.gpio.lcd_reset: U5.8, U7.3
mcu.gpio.lcd_rs: U5.10, U7.4
mcu.gpio.measure_select_0_0: U5.42, U11.6, U12.6
mcu.gpio.measure_select_1_0: U5.43, U13.6
mcu.gpio.rgb_blue: R10.2, U5.6
mcu.gpio.sw0: D2.2, U5.50
mcu.gpio.sw1: SW2.2, U5.16
mcu.gpio.sw2: SW3.2, U5.3
mcu.ic.swd.reset: J2.6, U5.40
mcu.ic.swd.swdio: J2.10, U5.51
mcu.swd.swd.swclk: J2.9, U5.53
mcu.swd.swd.swo: J2.8, U5.47
mcu.usb_res.usb_inner.dm: R5.1, U5.34
mcu.usb_res.usb_inner.dp: R4.1, U5.35
meas_chain_0: R17.2, U13.4, U14.3
meas_chain_1: TP5.1, U14.1, U14.4, U15.5
measure.range.switch.inputs.0: R18.2, U11.3
measure.range.switch.inputs.1: R19.2, U11.1
measure.range.switch.inputs.2: R20.2, U12.3
measure.range.switch.sw[1_0].inputs.0: U11.4, U13.3
measure.range.switch.sw[1_0].inputs.1: U12.4, U13.1
ref_buf.inp: R15.2, R16.1, U9.3
reg_5v.ic.ce: R3.2, U2.1
reg_5v.power_path.switch: L1.2, U2.5
rgb.blue_res.a: D6.1, R10.1
rgb.green_res.a: D6.4, R9.1
rgb.red_res.a: D6.3, R8.1
rgb.signals.green: R9.2, U5.5
rgb.signals.red: R8.2, U5.4
spk_chain_0: R12.1, U5.36
spk_chain_1: C10.1, C13.2, R12.2, TP4.1
spk_chain_2.a: J3.1, U8.8
spk_chain_2.b: J3.2, U8.5
spk_drv.(adapter)inp_res.b.dst: R13.2, U8.4
spk_drv.ic.inn: R14.2, U8.3
spk_drv.inn_res.a: C14.1, R14.1
spk_drv.inp_res.a: C13.1, R13.1
v3v3: C4.1, C8.1, C9.1, D4.1, D6.2, J2.1, R11.1, R22.1, TP2.1, U3.5, U5.28, U5.30, U7.7
v5v: C2.1, C3.1, C5.1, C11.1, C12.1, D3.1, TP1.1, U2.4, U3.1, U3.3, U4.1, U4.3, U8.1, U8.6
vanalog: C6.1, C15.1, C16.1, C17.1, C18.1, C19.1, C20.1, C26.1, C27.1, C28.1, C29.1, C30.1, D5.1, R15.1, R21.1, R23.1, R24.1, R25.1, R26.1, TP3.1, U4.5, U9.5, U9.6, U10.5, U11.5, U12.5, U13.5, U14.5, U14.6, U16.5, U16.6, U17.5, U18.5, U19.5, U20.5
vbat: Q1.2, R1.1, U1.1
vcenter: U9.1, U9.4, U10.1
