BerkeleyHCI/PolymorphicBlocks/edg/circuits/resources/Amplifier.kicad_sch

## KiCad design edg/circuits/resources/Amplifier.kicad_sch (2023-09-29)

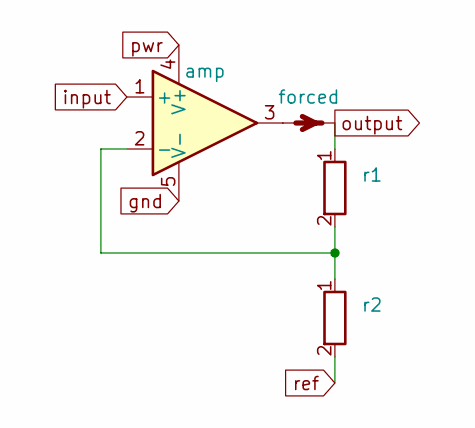
[picture p121: schematic Amplifier.kicad_sch]

Parts:
amp: (no value)
forced: (no value)
r1, r2: (no value)

Connections:
unnamed: amp.2 (-), r1.2, r2.1
unnamed: amp.3, forced.1
gnd: amp.5 (V-)
input: amp.1 (+)
output: forced.2, r1.1
pwr: amp.4 (V+)
ref: r2.2
