BerkeleyHCI/PolymorphicBlocks/edg/circuits/resources/BootstrapVoltageAdder.kicad_sch

## KiCad design edg/circuits/resources/BootstrapVoltageAdder.kicad_sch (2024-01-06)

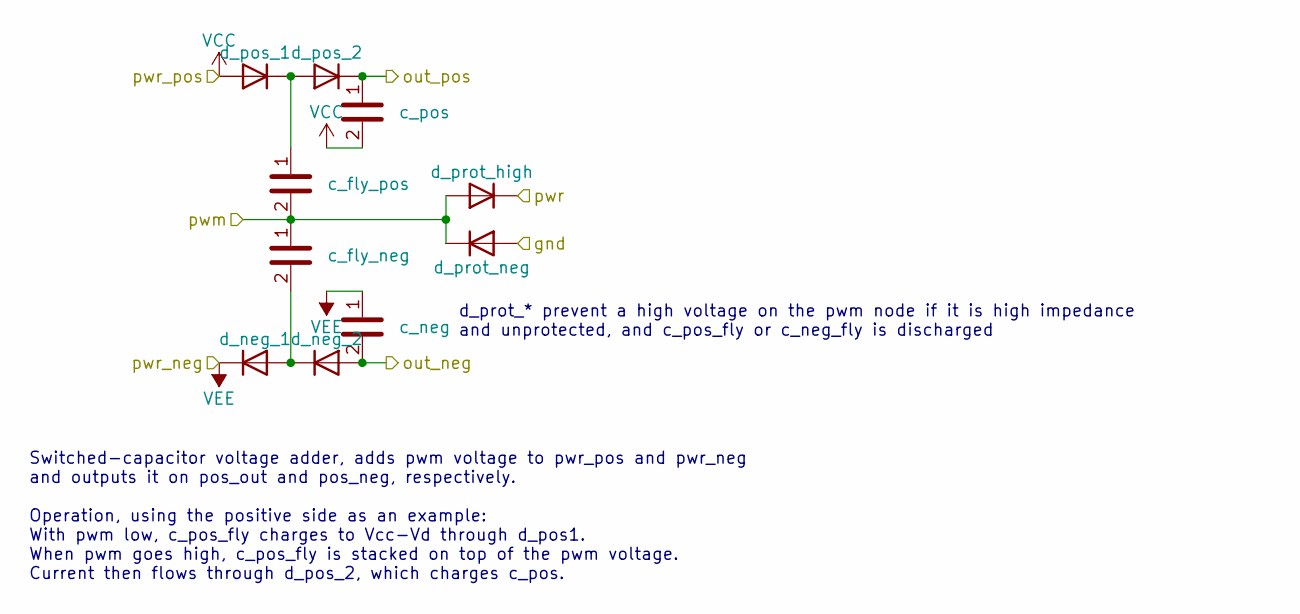
[picture p122: schematic BootstrapVoltageAdder.kicad_sch]

Parts:
c_fly_neg: (no value)
c_fly_pos: (no value)
c_neg: (no value)
c_pos: (no value)
d_neg_1, d_neg_2: (no value)
d_pos_1, d_pos_2: (no value)
d_prot_high: (no value)
d_prot_neg: (no value)

Connections:
unnamed: c_fly_neg.2, d_neg_1.2 (A), d_neg_2.1 (K)
unnamed: c_fly_pos.1, d_pos_1.1 (K), d_pos_2.2 (A)
VCC: c_pos.2, d_pos_1.2 (A)
VEE: c_neg.1, d_neg_1.1 (K)
gnd: d_prot_neg.2 (A)
out_neg: c_neg.2, d_neg_2.2 (A)
out_pos: c_pos.1, d_pos_2.1 (K)
pwm: c_fly_neg.1, c_fly_pos.2, d_prot_high.2 (A), d_prot_neg.1 (K)
pwr: d_prot_high.1 (K)

Notes on the sheet:
d_prot_* prevent a high voltage on the pwm node if it is high impedance and unprotected, and c_pos_fly or c_neg_fly is discharged
Switched-capacitor voltage adder, adds pwm voltage to pwr_pos and pwr_neg and outputs it on pos_out and pos_neg, respectively. Operation, using the positive side as an example: With pwm low, c_pos_fly charges to Vcc-Vd through d_pos1. When pwm goes high, c_pos_fly is stacked on top of the pwm volta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
