BerkeleyHCI/PolymorphicBlocks/edg/circuits/resources/CompensatorType2.kicad_sch

## KiCad design edg/circuits/resources/CompensatorType2.kicad_sch (2026-02-09)

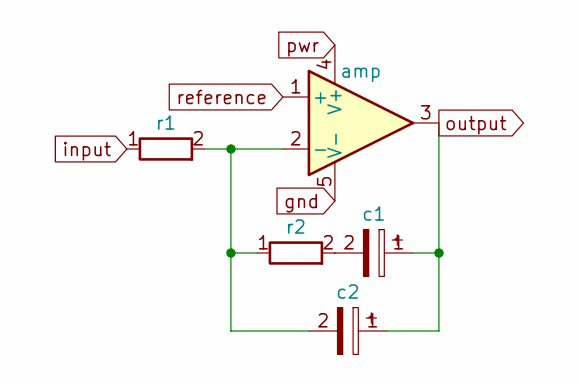
[picture p123: schematic CompensatorType2.kicad_sch]

Parts:
amp: (no value)
c1, c2: (no value)
r1, r2: (no value)

Connections:
unnamed: amp.2 (-), c2.2, r1.2, r2.1
unnamed: c1.2, r2.2
gnd: amp.5 (V-)
input: r1.1
output: amp.3, c1.1, c2.1
pwr: amp.4 (V+)
reference: amp.1 (+)
