BerkeleyHCI/PolymorphicBlocks/edg/circuits/resources/DifferentialAmplifier.kicad_sch

## KiCad design edg/circuits/resources/DifferentialAmplifier.kicad_sch (2023-10-19)

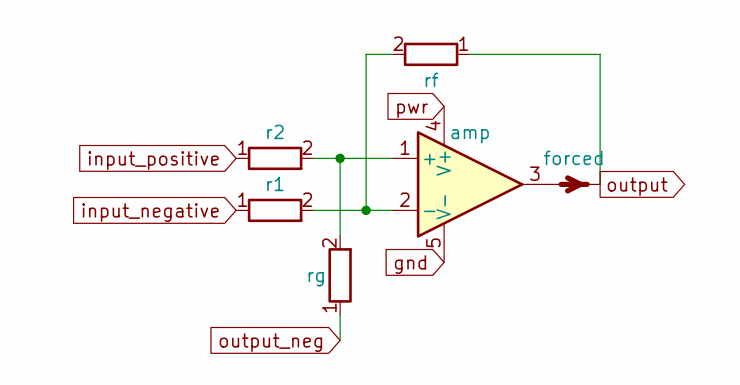
[picture p124: schematic DifferentialAmplifier.kicad_sch]

Parts:
amp: (no value)
forced: (no value)
r1, r2: (no value)
rf: (no value)
rg: (no value)

Connections:
unnamed: amp.1 (+), r2.2, rg.2
unnamed: amp.2 (-), r1.2, rf.2
unnamed: amp.3, forced.1
gnd: amp.5 (V-)
input_negative: r1.1
input_positive: r2.1
output: forced.2, rf.1
output_neg: rg.1
pwr: amp.4 (V+)
