BerkeleyHCI/PolymorphicBlocks/edg/circuits/resources/HighSideSwitch.kicad_sch

## KiCad design edg/circuits/resources/HighSideSwitch.kicad_sch (2023-12-21)

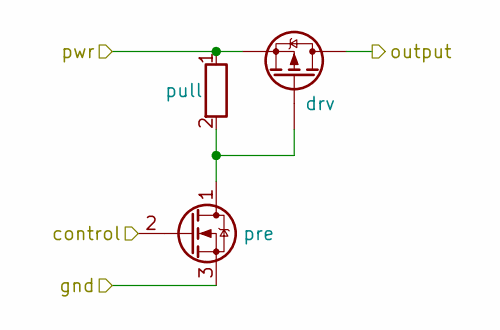
[picture p125: schematic HighSideSwitch.kicad_sch]

Parts:
drv: (no value)
pre: (no value)
pull: (no value)

Connections:
unnamed: drv.2 (G), pre.1 (D), pull.2
control: pre.2 (G)
gnd: pre.3 (S)
output: drv.1 (D)
pwr: drv.3 (S), pull.1
