BerkeleyHCI/PolymorphicBlocks/edg/circuits/resources/HighSideSwitch_Zener.kicad_sch

## KiCad design edg/circuits/resources/HighSideSwitch_Zener.kicad_sch (2023-12-21)

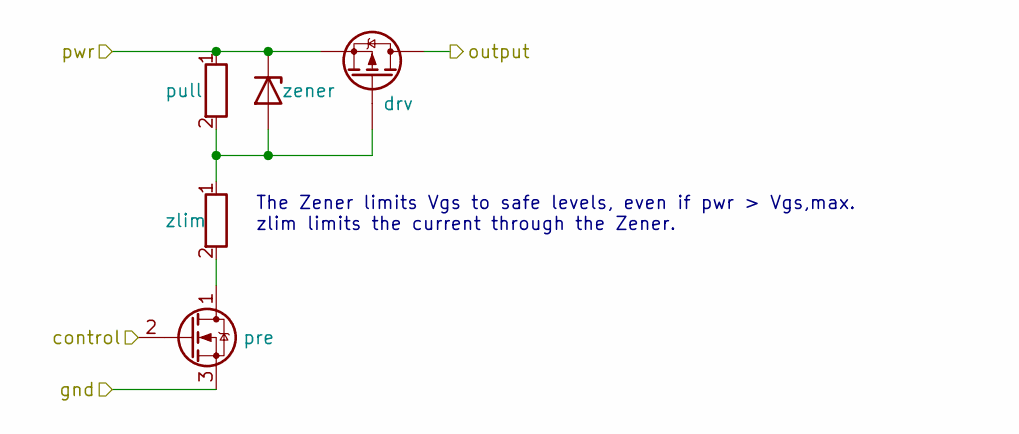
[picture p126: schematic HighSideSwitch_Zener.kicad_sch]

Parts:
drv: (no value)
pre: (no value)
pull: (no value)
zener: (no value)
zlim: (no value)

Connections:
unnamed: drv.2 (G), pull.2, zener.2 (A), zlim.1
unnamed: pre.1 (D), zlim.2
control: pre.2 (G)
gnd: pre.3 (S)
output: drv.1 (D)
pwr: drv.3 (S), pull.1, zener.1 (K)

Notes on the sheet:
The Zener limits Vgs to safe levels, even if pwr > Vgs,max. zlim limits the current through the Zener.
