BerkeleyHCI/PolymorphicBlocks/edg/circuits/resources/IntegratorInverting.kicad_sch

## KiCad design edg/circuits/resources/IntegratorInverting.kicad_sch (2022-12-27)

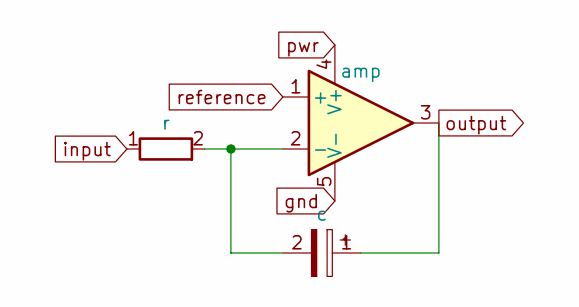
[picture p127: schematic IntegratorInverting.kicad_sch]

Parts:
amp: (no value)
c: (no value)
r: (no value)

Connections:
unnamed: amp.2 (-), c.2, r.2
gnd: amp.5 (V-)
input: r.1
output: amp.3, c.1
pwr: amp.4 (V+)
reference: amp.1 (+)
