BerkeleyHCI/PolymorphicBlocks/edg/circuits/resources/OpampFollower.kicad_sch

## KiCad design edg/circuits/resources/OpampFollower.kicad_sch (2023-09-29)

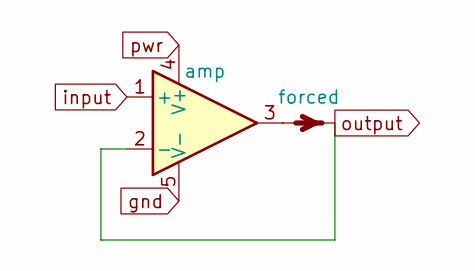
[picture p128: schematic OpampFollower.kicad_sch]

Parts:
amp: (no value)
forced: (no value)

Connections:
unnamed: amp.3, forced.1
gnd: amp.5 (V-)
input: amp.1 (+)
output: amp.2 (-), forced.2
pwr: amp.4 (V+)
