BerkeleyHCI/PolymorphicBlocks/edg/circuits/resources/PmosChargerReverseProtection.kicad_sch

## KiCad design edg/circuits/resources/PmosChargerReverseProtection.kicad_sch (2024-04-30)

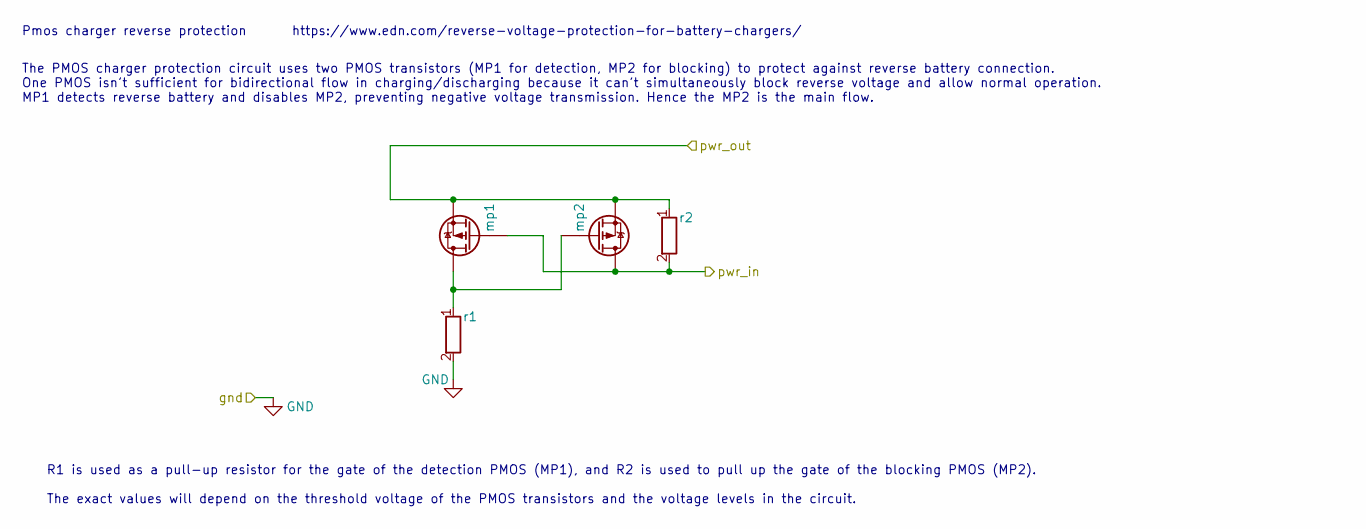
[picture p129: schematic PmosChargerReverseProtection.kicad_sch]

Parts:
mp1, mp2: (no value)
r1, r2: (no value)

Connections:
unnamed: mp1.1 (D), mp2.2 (G), r1.1
gnd: r1.2
pwr_in: mp1.2 (G), mp2.1 (D), r2.2
pwr_out: mp1.3 (S), mp2.3 (S), r2.1

Notes on the sheet:
Pmos charger reverse protection
R1 is used as a pull-up resistor for the gate of the detection PMOS (MP1), and R2 is used to pull up the gate of the blocking PMOS (MP2). The exact values will depend on the threshold voltage of the PMOS transistors and the voltage levels in the circuit.
https://www.edn.com/reverse-voltage-protection-for-battery-chargers/
The PMOS charger protection circuit uses two PMOS transistors (MP1 for detection, MP2 for blocking) to protect against reverse battery connection. One PMOS isn't sufficient for bidirectional flow in charging/discharging because it can't simultaneously block reverse voltage and allow normal operatio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
