BerkeleyHCI/PolymorphicBlocks/edg/circuits/resources/PriorityPowerOr.kicad_sch

## KiCad design edg/circuits/resources/PriorityPowerOr.kicad_sch (2023-06-09)

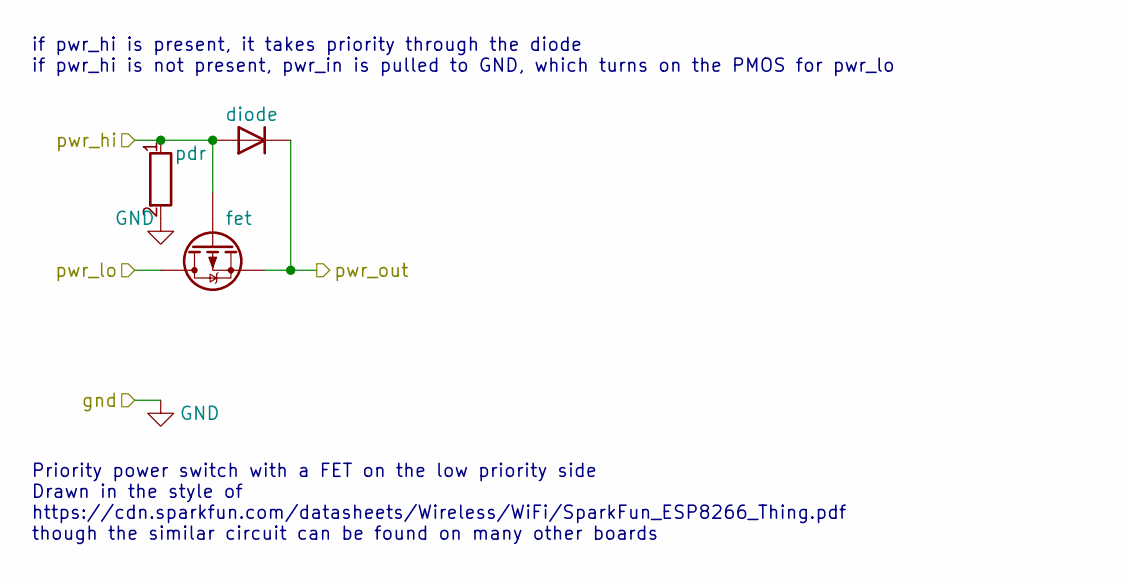
[picture p130: schematic PriorityPowerOr.kicad_sch]

Parts:
diode: (no value)
fet: (no value)
pdr: (no value)

Connections:
pwr_hi: diode.2 (A), fet.2 (G), pdr.1
pwr_lo: fet.1 (D)
pwr_out: diode.1 (K), fet.3 (S)

Notes on the sheet:
if pwr_hi is present, it takes priority through the diode if pwr_hi is not present, pwr_in is pulled to GND, which turns on the PMOS for pwr_lo
Priority power switch with a FET on the low priority side Drawn in the style of https://cdn.sparkfun.com/datasheets/Wireless/WiFi/SparkFun_ESP8266_Thing.pdf though the similar circuit can be found on many other boards
