BerkeleyHCI/PolymorphicBlocks/edg/circuits/resources/RampLimiter.kicad_sch

## KiCad design edg/circuits/resources/RampLimiter.kicad_sch (2025-09-03)

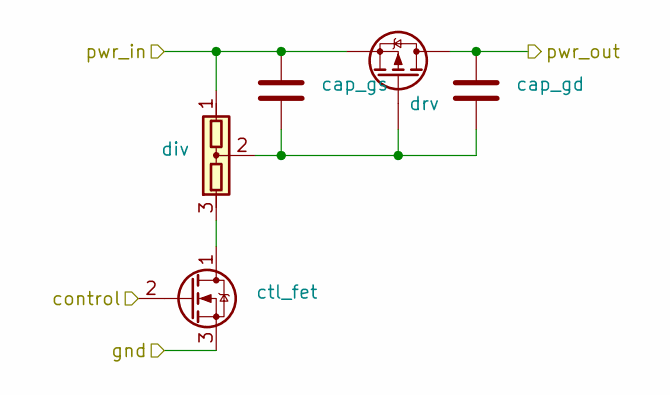
[picture p131: schematic RampLimiter.kicad_sch]

Parts:
cap_gd: (no value)
cap_gs: (no value)
ctl_fet: (no value)
div: (no value)
drv: (no value)

Connections:
unnamed: cap_gd.2, cap_gs.2, div.2, drv.2 (G)
unnamed: ctl_fet.1 (D), div.3
control: ctl_fet.2 (G)
gnd: ctl_fet.3 (S)
pwr_in: cap_gs.1, div.1, drv.3 (S)
pwr_out: cap_gd.1, drv.1 (D)
