BerkeleyHCI/PolymorphicBlocks/edg/circuits/resources/SoftPowerGate.kicad_sch

## KiCad design edg/circuits/resources/SoftPowerGate.kicad_sch (2024-04-30)

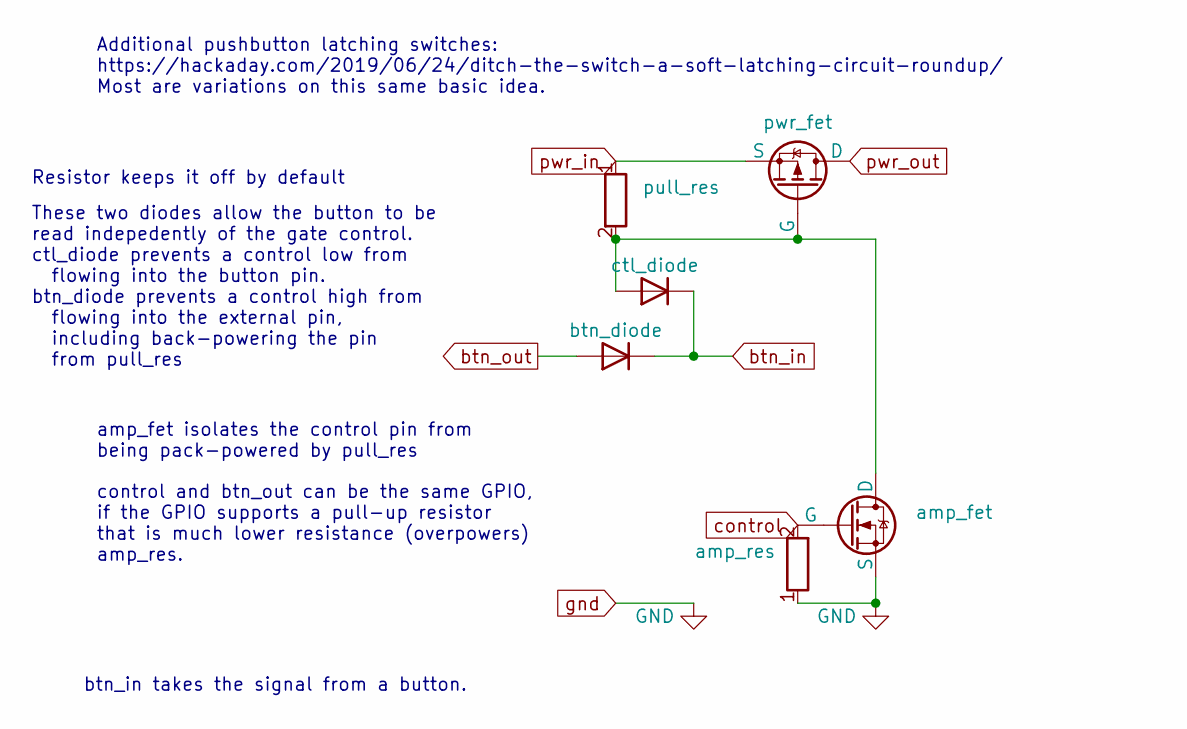
[picture p132: schematic SoftPowerGate.kicad_sch]

Parts:
amp_fet: (no value)
amp_res: (no value)
btn_diode: (no value)
ctl_diode: (no value)
pull_res: (no value)
pwr_fet: (no value)

Connections:
unnamed: amp_fet.1 (D), ctl_diode.2 (A), pull_res.2, pwr_fet.2 (G)
unnamed: amp_fet.3 (S), amp_res.1
btn_in: btn_diode.1 (K), ctl_diode.1 (K)
btn_out: btn_diode.2 (A)
control: amp_fet.2 (G), amp_res.2
pwr_in: pull_res.1, pwr_fet.3 (S)
pwr_out: pwr_fet.1 (D)

Notes on the sheet:
Resistor keeps it off by default
Additional pushbutton latching switches: https://hackaday.com/2019/06/24/ditch-the-switch-a-soft-latching-circuit-roundup/ Most are variations on this same basic idea.
amp_fet isolates the control pin from being pack-powered by pull_res
btn_in takes the signal from a button.
These two diodes allow the button to be read indepedently of the gate control. ctl_diode prevents a control low from flowing into the button pin. btn_diode prevents a control high from flowing into the external pin, including back-powering the pin from pull_res
control and btn_out can be the same GPIO, if the GPIO supports a pull-up resistor that is much lower resistance (overpowers) amp_res.
