BerkeleyHCI/PolymorphicBlocks/edg/electronics_interfaces/resources/test_kicad_import_blackbox.kicad_sch

## KiCad design edg/electronics_interfaces/resources/test_kicad_import_blackbox.kicad_sch (2023-01-11)

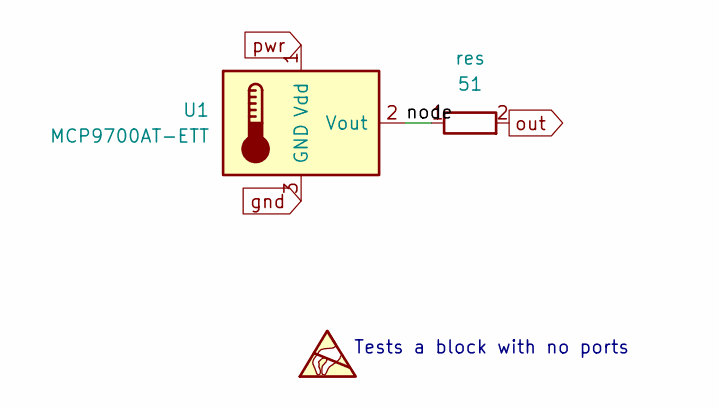
[picture p133: schematic test_kicad_import_blackbox.kicad_sch]

Parts:
SYM1: SYM_ESD_Small; Symbol_ESD-Logo_CopperTop
U1: MCP9700AT-ETT; SOT-23
res: 51

Connections:
gnd: U1.3 (GND)
node: U1.2 (Vout), res.1
out: res.2
pwr: U1.1 (Vdd)

Notes on the sheet:
Tests a block with no ports
