BerkeleyHCI/PolymorphicBlocks/edg/electronics_model/resources/test_kicad_import_aliasedpinname.kicad_sch

## KiCad design edg/electronics_model/resources/test_kicad_import_aliasedpinname.kicad_sch (2023-03-29)

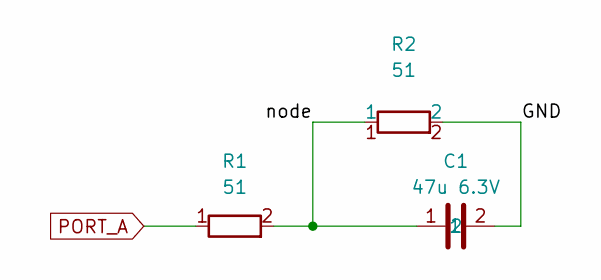
[picture p135: schematic test_kicad_import_aliasedpinname.kicad_sch]

Parts:
C1: 47u 6.3V
R1, R2: 51

Connections:
GND: C1.2, R2.2
PORT_A: R1.1
node: C1.1, R1.2, R2.1
