BerkeleyHCI/PolymorphicBlocks/edg/electronics_model/resources/test_kicad_import_codeparts.kicad_sch

## KiCad design edg/electronics_model/resources/test_kicad_import_codeparts.kicad_sch (2023-03-29)

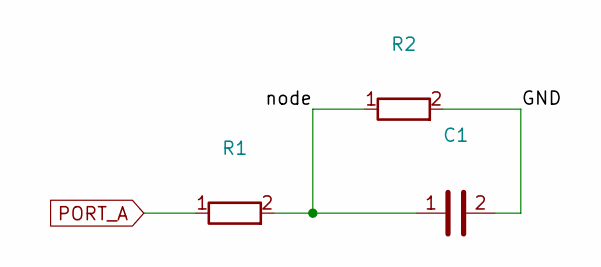
[picture p136: schematic test_kicad_import_codeparts.kicad_sch]

Parts:
C1: (no value)
R1, R2: (no value)

Connections:
GND: C1.2, R2.2
PORT_A: R1.1
node: C1.1, R1.2, R2.1
