BerkeleyHCI/PolymorphicBlocks/edg/electronics_model/resources/test_kicad_import_inline_badmultiline.kicad_sch

## KiCad design edg/electronics_model/resources/test_kicad_import_inline_badmultiline.kicad_sch (2025-02-22)

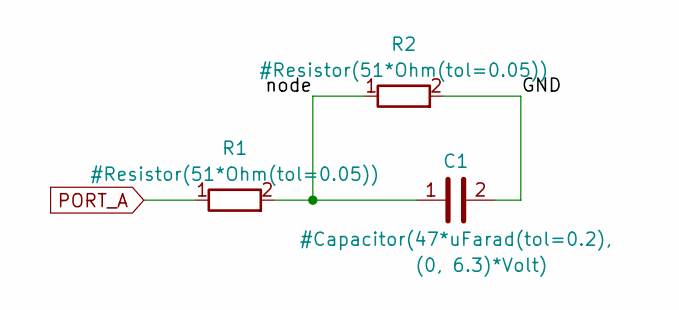
[picture p138: schematic test_kicad_import_inline_badmultiline.kicad_sch]

Parts:
C1: #Capacitor(47*uFarad(tol=0.2),
R1, R2: #Resistor(51*Ohm(tol=0.05))

Connections:
GND: C1.2, R2.2
PORT_A: R1.1
node: C1.1, R1.2, R2.1
