BerkeleyHCI/PolymorphicBlocks/edg/electronics_model/resources/test_kicad_import_inline_vars.kicad_sch

## KiCad design edg/electronics_model/resources/test_kicad_import_inline_vars.kicad_sch (2023-03-29)

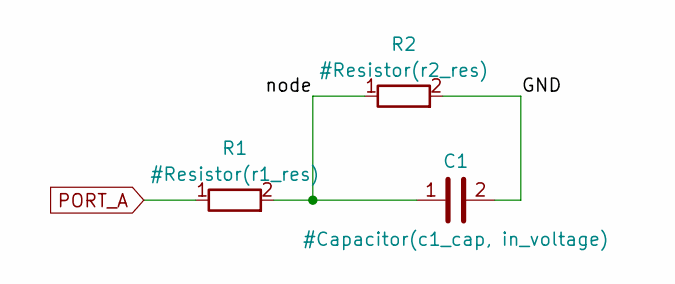
[picture p139: schematic test_kicad_import_inline_vars.kicad_sch]

Parts:
C1: #Capacitor(c1_cap, in_voltage)
R1: #Resistor(r1_res)
R2: #Resistor(r2_res)

Connections:
GND: C1.2, R2.2
PORT_A: R1.1
node: C1.1, R1.2, R2.1
