BerkeleyHCI/PolymorphicBlocks/edg/electronics_model/resources/test_kicad_import_node.kicad_sch

## KiCad design edg/electronics_model/resources/test_kicad_import_node.kicad_sch (2023-03-29)

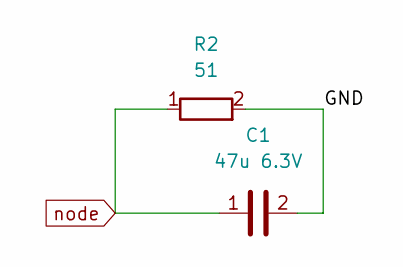
[picture p140: schematic test_kicad_import_node.kicad_sch]

Parts:
C1: 47u 6.3V
R2: 51

Connections:
GND: C1.2, R2.2
node: C1.1, R2.1
