BerkeleyHCI/PolymorphicBlocks/edg/parts/display/resources/EInkBoostPowerPath.kicad_sch

## KiCad design edg/parts/display/resources/EInkBoostPowerPath.kicad_sch (2024-07-13)

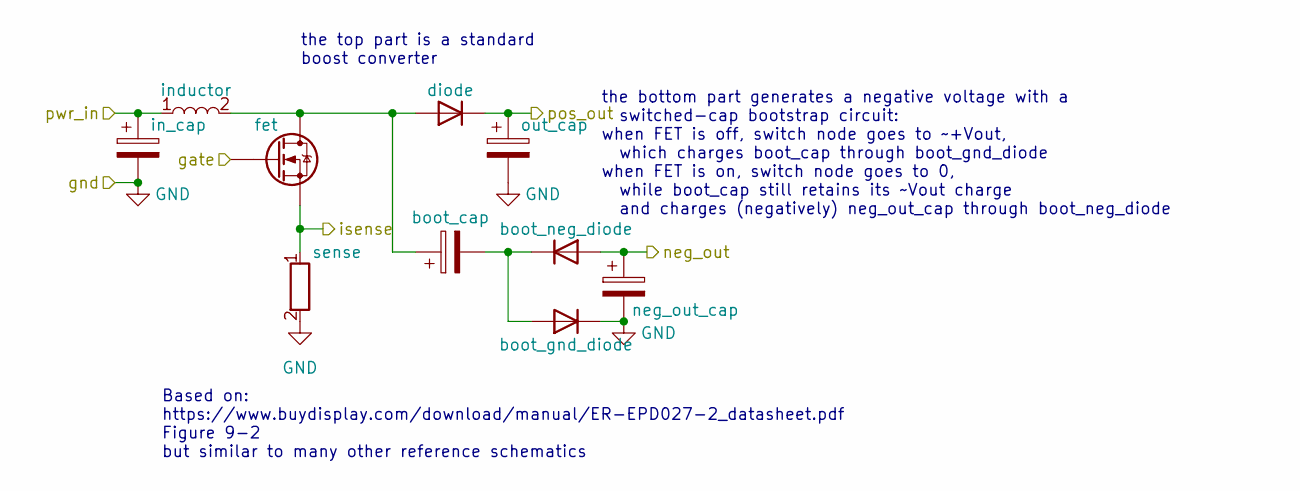
[picture p141: schematic EInkBoostPowerPath.kicad_sch]

Parts:
boot_cap: (no value)
boot_gnd_diode: (no value)
boot_neg_diode: (no value)
diode: (no value)
fet: (no value)
in_cap: (no value)
inductor: (no value)
neg_out_cap: (no value)
out_cap: (no value)
sense: (no value)

Connections:
unnamed: boot_cap.1, diode.2 (A), fet.1 (D), inductor.2
unnamed: boot_cap.2, boot_gnd_diode.2 (A), boot_neg_diode.1 (K)
unnamed: boot_gnd_diode.1 (K), neg_out_cap.2
gate: fet.2 (G)
gnd: in_cap.2
isense: fet.3 (S), sense.1
neg_out: boot_neg_diode.2 (A), neg_out_cap.1
pos_out: diode.1 (K), out_cap.1
pwr_in: in_cap.1, inductor.1

Notes on the sheet:
the top part is a standard boost converter
the bottom part generates a negative voltage with a switched-cap bootstrap circuit: when FET is off, switch node goes to ~+Vout, which charges boot_cap through boot_gnd_diode when FET is on, switch node goes to 0, while boot_cap still retains its ~Vout charge and charges (negatively) neg_out_cap th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
Based on: https://www.buydisplay.com/download/manual/ER-EPD027-2_datasheet.pdf Figure 9-2 but similar to many other reference schematics
