BerkeleyHCI/PolymorphicBlocks/edg/parts/microcontroller/resources/EspAutoProgram.kicad_sch

## KiCad design edg/parts/microcontroller/resources/EspAutoProgram.kicad_sch (2023-06-09)

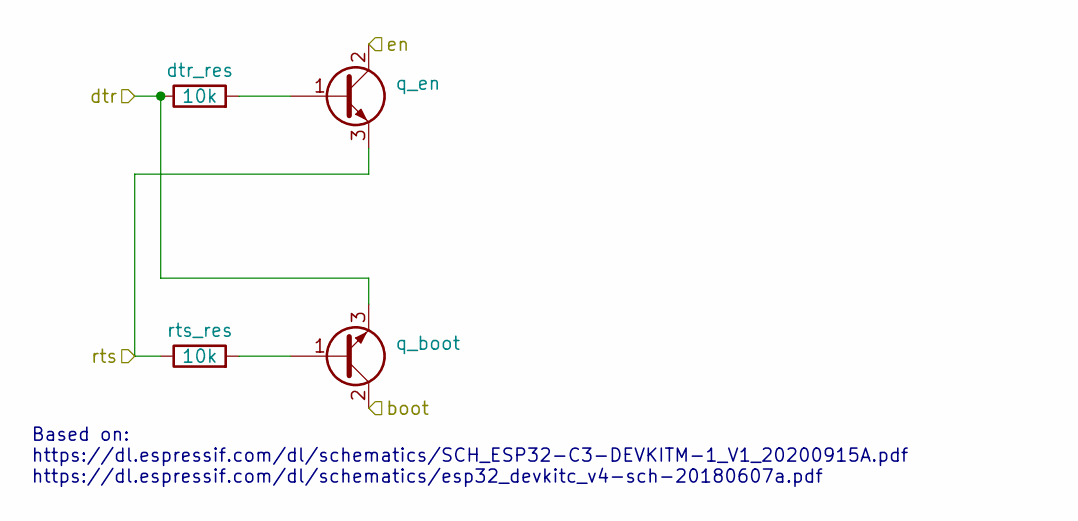
[picture p142: schematic EspAutoProgram.kicad_sch]

Parts:
dtr_res: 10k
q_boot: (no value)
q_en: (no value)
rts_res: 10k

Connections:
unnamed: dtr_res.2, q_en.1 (B)
unnamed: q_boot.1 (B), rts_res.2
boot: q_boot.2 (C)
dtr: dtr_res.1, q_boot.3 (E)
en: q_en.2 (C)
rts: q_en.3 (E), rts_res.1

Notes on the sheet:
Based on: https://dl.espressif.com/dl/schematics/SCH_ESP32-C3-DEVKITM-1_V1_20200915A.pdf https://dl.espressif.com/dl/schematics/esp32_devkitc_v4-sch-20180607a.pdf
