BerkeleyHCI/PolymorphicBlocks/edg/vendor_parts/jlc/resources/test_kicad_import_jlc.kicad_sch

## KiCad design edg/vendor_parts/jlc/resources/test_kicad_import_jlc.kicad_sch (2023-03-29)

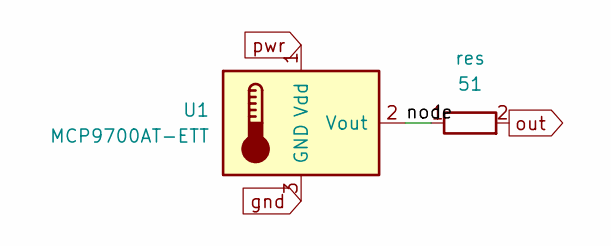
[picture p143: schematic test_kicad_import_jlc.kicad_sch]

Parts:
U1: MCP9700AT-ETT; SOT-23; JLCPCB Part # C127949
res: 51

Connections:
gnd: U1.3 (GND)
node: U1.2 (Vout), res.1
out: res.2
pwr: U1.1 (Vdd)
