BerkeleyHCI/PolymorphicBlocks/edg/parts/sensor/LightSensor_Bh1750.py

from typing_extensions import override

from ...circuits import *
from ...vendor_parts.jlc.JlcPart import JlcPart


class Bh1750_Device(InternalSubcircuit, FootprintBlock, JlcPart):
    def __init__(self) -> None:
        super().__init__()
        self.gnd = self.Port(Ground())
        self.vcc = self.Port(
            VoltageSink(
                voltage_limits=(2.4, 3.6) * Volt,
                current_draw=(0.01 * uAmp, 190 * uAmp),  # typ powerdown to max supply current
            )
        )
        self.dvi = self.Port(
            DigitalSink.from_supply(self.gnd, self.vcc, input_threshold_abs=(0.4, 0.4) * Volt)
        )  # reset pin

        dio_model = DigitalBidir.from_supply(self.gnd, self.vcc, input_threshold_factor=(0.3, 0.7))
        self.i2c = self.Port(I2cTarget(dio_model, addresses=[0x23], frequency_limit=(0, 400) * kHertz))

    @override
    def contents(self) -> None:
        self.footprint(
            "U",
            "Package_TO_SOT_SMD:HVSOF6",
            {
                "1": self.vcc,
                "2": self.gnd,  # TODO address support
                "3": self.gnd,
                "4": self.i2c.sda,
                "5": self.dvi,
                "6": self.i2c.scl,
            },
            mfr="Rohm Semiconductor",
            part="BH1750",
            datasheet="https://www.mouser.com/datasheet/2/348/bh1750fvi-e-186247.pdf",
        )
        self.assign(self.lcsc_part, "C78960")
        self.assign(self.actual_basic_part, False)


class Bh1750(Resettable, LightSensor, GeneratorBlock):
    """16-bit ambient light sensor, 1-65535 lx"""

    def __init__(self) -> None:
        super().__init__()
        self.ic = self.Block(Bh1750_Device())
        self.pwr = self.Export(self.ic.vcc, [Power])
        self.gnd = self.Export(self.ic.gnd, [Common])
        self.i2c = self.Export(self.ic.i2c)

        self.generator_param(self.reset.is_connected())

    @override
    def generate(self) -> None:
        super().generate()

        self.vcc_cap = self.Block(DecouplingCapacitor(100 * nFarad(tol=0.2))).connected(self.gnd, self.ic.vcc)

        if self.get(self.reset.is_connected()):
            self.connect(self.reset, self.ic.dvi)
            self.dvi_cap = self.Block(DigitalCapacitor(0.1 * uFarad(tol=0.05))).connected(gnd=self.gnd, io=self.ic.dvi)
        else:
            self.dvi_pull = self.Block(PullupDelayRc(1 * kOhm(tol=0.05), 1 * mSecond(tol=0.2))).connected(
                gnd=self.gnd, pwr=self.pwr, io=self.ic.dvi
            )
