BerkeleyHCI/PolymorphicBlocks/edg/abstract_parts/LedDriver.py

from typing import Any

from ..abstract_parts import *
from deprecated import deprecated


@deprecated("LED API is not stabilized")
@abstract_block
class LedDriver(PowerConditioner, Interface):
    """Abstract current-regulated high-power LED driver.
    LED ports are passive and should be directly connected to the LED (or LED string)."""

    def __init__(self, max_current: RangeLike) -> None:
        super().__init__()

        self.pwr = self.Port(VoltageSink.empty(), [Power])
        self.gnd = self.Port(Ground.empty(), [Common])

        self.leda = self.Port(Passive())
        self.ledk = self.Port(Passive())

        self.max_current = self.ArgParameter(max_current)


@deprecated("ripple should be an internal parameter")
class LedDriverSwitchingConverter(BlockInterfaceMixin[LedDriver]):
    """LED driver mixin indicating that the LED driver is a switching converter and with a peak-peak ripple limit."""

    def __init__(self, *args: Any, ripple_limit: FloatLike = float("inf"), **kwargs: Any) -> None:
        super().__init__(*args, **kwargs)
        self.ripple_limit = self.ArgParameter(ripple_limit)


@deprecated("LED API is not stabilized")
class LedDriverPwm(BlockInterfaceMixin[LedDriver]):
    """LED driver mixin with PWM input for dimming control."""

    def __init__(self, *args: Any, **kwargs: Any) -> None:
        super().__init__(*args, **kwargs)
        self.pwm = self.Port(DigitalSink.empty(), optional=True)
