BerkeleyHCI/PolymorphicBlocks/edg/parts/microcontroller/Stm32f303.py

from typing import *

from typing_extensions import override

from ...circuits import *


@non_library
class Stm32f303_Interfaces(IoControllerI2cTarget, IoControllerDac, IoControllerCan):
    """Base class for STM32F303x6/8 devices (separate from STM32F303xB/C)."""


class Nucleo_F303k8(
    IoControllerUsbOut,
    IoControllerPowerOut,
    IoController,
    Stm32f303_Interfaces,
    BaseIoControllerPinmapGenerator,
    GeneratorBlock,
    FootprintBlock,
):
    """Nucleo32 F303K8 configured as power source from USB."""

    _PIN_MAPPING = {
        "PA9": "1",  # CN3.1, D1
        "PA10": "2",  # CN3.2, D0
        # 'NRST': '3'  # CN3.3, RESET
        "PA12": "5",  # CN3.5, D2
        "PB0": "6",  # CN3.6, D3
        "PB7": "7",  # CN3.7, D4
        "PB6": "8",  # CN3.8, D5
        "PB1": "9",  # CN3.9, D6
        "PF0": "10",  # CN3.10, D7
        "PF1": "11",  # CN3.11, D8
        "PA8": "12",  # CN3.12, D9
        "PA11": "13",  # CN3.13, D10
        "PB5": "14",  # CN3.14, D11
        "PB4": "15",  # CN3.15, D12
        # 'NRST': '18'  # CN4.3, RESET
        "PA2": "20",  # CN4.5, A7
        "PA7": "21",  # CN4.6, A6
        "PA6": "22",  # CN4.7, A5
        "PA5": "23",  # CN4.8, A4
        "PA4": "24",  # CN4.9, A3
        "PA3": "25",  # CN4.10, A2
        "PA1": "26",  # CN4.11, A1
        "PA0": "27",  # CN4.12, A0
        "PB3": "30",  # CN4.15, D13
    }

    @override
    def _system_pinmap(self) -> Mapping[Union[Iterable[str], str], Union[Passive, HasPassivePort]]:
        return {
            ("4", "17"): self.gnd,
            "29": self.pwr if self.get(self.pwr.is_connected()) else self.pwr_out,
            "19": self.vusb_out,
        }

    def __init__(self) -> None:
        super().__init__()

        self.gnd.init_from(Ground())
        self.pwr.init_from(
            VoltageSink(  # assumes single-rail module
                voltage_limits=(2, 3.6) * Volt,  # table 19
                current_draw=(0.00055, 80) * mAmp + self.io_current_draw.upper(),  # table 25 Idd standby to max
            )
        )

        self.vusb_out.init_from(
            VoltageSource(
                voltage=(4.75 - 0.58, 5.1)
                * Volt,  # 4.75V USB - 0.58v BAT60JFILM drop to 5.1 from LD1117S50TR, ignoring ST890CDR
                current_limits=(0, 0.5) * Amp,  # max USB draw  # TODO higher from external power
            )
        )
        self.pwr_out.init_from(
            VoltageSource(
                voltage=3.3 * Volt(tol=0.03),  # LD39050PU33R worst-case Vout accuracy
                current_limits=(0, 0.5) * Amp,  # max USB current draw, LDO also guarantees 500mA output current
            )
        )

        self.generator_param(self.pwr.is_connected())

    @override
    def generate(self) -> None:
        super().generate()

        self.footprint(
            "U",
            "edg:Nucleo32",
            self._make_pinning(),
            mfr="STMicroelectronics",
            part="NUCLEO-F303K8",
            datasheet="https://www.st.com/resource/en/user_manual/dm00231744.pdf",
        )

    @override
    def _io_pinmap(self) -> PinMapUtil:
        """Returns the mappable for a STM32F303 device with the input power and ground references.
        This allows a shared definition between discrete chips and microcontroller boards"""
        # these are common to all IO blocks
        if self.get(self.pwr.is_connected()):  # board sinks power
            vdd: Port[VoltageLink] = self.pwr
            vdda: Port[VoltageLink] = self.pwr
        else:
            vdd = self.pwr_out
            vdda = self.pwr_out

        input_threshold_factor = (0.3, 0.7)  # TODO relaxed (but more complex) bounds available for different IO blocks
        current_limits = (-20, 20) * mAmp  # Section 6.3.14, TODO loose with relaxed VOL/VOH
        dio_tc_model = DigitalBidir.from_supply(
            self.gnd,
            vdd,
            voltage_limit_abs=(-0.3, 0.3) * Volt,  # Table 19
            current_limits=current_limits,
            input_threshold_factor=input_threshold_factor,
            pullup_capable=True,
            pulldown_capable=True,
        )
        dio_tc_switch_model = DigitalBidir.from_supply(
            self.gnd,
            vdd,
            voltage_limit_abs=(-0.3, 0.3) * Volt,  # Table 19
            current_limits=(-3, 0),  # Table 13, note 1, can sink 3 mA and should not source current
            input_threshold_factor=input_threshold_factor,
            pullup_capable=True,
            pulldown_capable=True,
        )
        dio_tt_model = DigitalBidir.from_supply(
            self.gnd,
            vdd,
            voltage_limit_abs=(-0.3, 3.6) * Volt,  # Table 19
            current_limits=current_limits,
            input_threshold_factor=input_threshold_factor,
            pullup_capable=True,
            pulldown_capable=True,
        )
        dio_tta_model = DigitalBidir.from_supply(
            self.gnd,
            vdd,
            voltage_limit_abs=(-0.3 * Volt, vdda.link().voltage.lower() + 0.3 * Volt),  # Table 19
            current_limits=current_limits,
            input_threshold_factor=input_threshold_factor,
            pullup_capable=True,
            pulldown_capable=True,
        )
        dio_ft_model = DigitalBidir.from_supply(
            self.gnd,
            vdd,
            voltage_limit_abs=(-0.3, 5.5) * Volt,  # Table 19
            current_limits=current_limits,
            input_threshold_factor=input_threshold_factor,
            pullup_capable=True,
            pulldown_capable=True,
        )
        dio_ftf_model = dio_ft_model
        dio_boot0_model = DigitalBidir.from_supply(
            self.gnd,
            vdd,
            voltage_limit_abs=(-0.3, 5.5) * Volt,  # Table 19
            current_limits=current_limits,
            input_threshold_factor=input_threshold_factor,
            pullup_capable=True,
            pulldown_capable=True,
        )

        adc_model = AnalogSink.from_supply(
            self.gnd,
            vdd,
            voltage_limit_tolerance=(-0.3, 0.3) * Volt,
            signal_limit_tolerance=(0, 0),  # Table 60 conversion voltage range
            impedance=100
            * kOhm(tol=0),  # TODO: actually spec'd as maximum external impedance; internal impedance not given
        )
        dac_model = AnalogSource.from_supply(
            self.gnd, vdd, signal_bound=(0.2 * Volt, -0.2 * Volt), impedance=15 * kOhm(tol=0)  # assumes buffer off
        )

        uart_model = UartPort(DigitalBidir.empty(), baud_limit=(0, 9) * MHertz)
        spi_model = SpiController(DigitalBidir.empty(), frequency_limit=(0, 18) * MHertz)
        # TODO SPI peripherals, which have fixed-pin CS lines
        i2c_model = I2cController(DigitalBidir.empty(), frequency_limit=(0, 1000) * kHertz)
        i2c_target_model = I2cTarget(DigitalBidir.empty(), frequency_limit=(0, 1000) * kHertz)
        can_model = CanControllerPort(DigitalBidir.empty(), bitrate_limit=(0, 1) * MHertz)

        return PinMapUtil(
            [  # Table 13, partial table for 48-pin only
                PinResource("PC13", {"PC13": dio_tc_model}),
                PinResource("PC14", {"PC14": dio_tc_model}),  # TODO remappable to OSC32_IN
                PinResource("PC15", {"PC15": dio_tc_model}),  # TODO remappable to OSC32_OUT
                PinResource("PF0", {"PF0": dio_ft_model}),  # TODO remappable to OSC_OUT
                PinResource("PF1", {"PF1": dio_ft_model}),  # TODO remappable to OSC_OUT
                PinResource("PA0", {"PA0": dio_tta_model, "ADC1_IN1": adc_model}),
                PinResource("PA1", {"PA1": dio_tta_model, "ADC1_IN2": adc_model}),
                PinResource("PA2", {"PA2": dio_tta_model, "ADC1_IN3": adc_model}),
                PinResource("PA3", {"PA3": dio_tta_model, "ADC1_IN4": adc_model}),
                PinResource("PA4", {"PA4": dio_tta_model, "ADC2_IN1": adc_model, "DAC1_OUT1": dac_model}),
                PinResource("PA5", {"PA5": dio_tta_model, "ADC2_IN2": adc_model, "DAC1_OUT2": dac_model}),
                PinResource("PA6", {"PA6": dio_tta_model, "ADC2_IN3": adc_model, "DAC2_OUT1": dac_model}),
                PinResource("PA7", {"PA7": dio_tta_model, "ADC2_IN4": adc_model}),
                PinResource("PB0", {"PB0": dio_tta_model, "ADC1_IN11": adc_model}),
                PinResource("PB1", {"PB1": dio_tta_model, "ADC1_IN12": adc_model}),
                PinResource("PB2", {"PB2": dio_tta_model, "ADC2_IN12": adc_model}),
                PinResource("PB10", {"PB10": dio_tt_model}),
                PinResource("PB11", {"PB11": dio_tta_model}),
                PinResource("PB12", {"PB12": dio_tta_model, "ADC2_IN13": adc_model}),
                PinResource("PB13", {"PB13": dio_tta_model, "ADC1_IN13": adc_model}),
                PinResource("PB14", {"PB14": dio_tta_model, "ADC2_IN14": adc_model}),
                PinResource("PB15", {"PB15": dio_tta_model, "ADC2_IN15": adc_model}),
                PinResource("PA8", {"PA8": dio_ft_model}),
                PinResource("PA9", {"PA9": dio_ft_model}),
                PinResource("PA10", {"PA10": dio_ft_model}),
                PinResource("PA11", {"PA11": dio_ft_model}),
                PinResource("PA12", {"PA12": dio_ft_model}),
                PinResource("PA13", {"PA13": dio_ft_model}),  # also JTMS/SWDAT
                PinResource("PA14", {"PA14": dio_ftf_model}),  # also JTCK/SWCLK
                PinResource("PA15", {"PA15": dio_ftf_model}),  # also JTDI
                PinResource("PB3", {"PB3": dio_ft_model}),  # also JTDO/TRACESWO
                PinResource("PB4", {"PB4": dio_ft_model}),
                PinResource("PB5", {"PB5": dio_ft_model}),
                PinResource("PB6", {"PB6": dio_ftf_model}),
                PinResource("PB7", {"PB7": dio_ftf_model}),
                PinResource("PB8", {"PB8": dio_ftf_model}),
                PinResource("PB9", {"PB9": dio_ftf_model}),
                PeripheralFixedResource(
                    "USART2", uart_model, {"tx": ["PA2", "PA14", "PB3"], "rx": ["PA3", "PA15", "PB4"]}
                ),
                PeripheralFixedResource(
                    "SPI1", spi_model, {"sck": ["PA5", "PB3"], "miso": ["PA6", "PB4"], "mosi": ["PA7", "PB5"]}
                ),
                PeripheralFixedResource(
                    "USART3", uart_model, {"tx": ["PB10", "PC10", "PB9"], "rx": ["PB11", "PC11", "PB8"]}  # 1/3 check
                ),
                PeripheralFixedResource("USART1", uart_model, {"tx": ["PA9", "PB6"], "rx": ["PA10", "PB7"]}),
                PeripheralFixedResource("CAN", can_model, {"tx": ["PA12", "PB9"], "rx": ["PA11", "PB8"]}),
                PeripheralFixedResource(
                    "I2C1", i2c_model, {"scl": ["PA15", "PB6", "PB8"], "sda": ["PA14", "PB7", "PB9"]}
                ),
                PeripheralFixedResource(
                    "I2C1_T", i2c_target_model, {"scl": ["PA15", "PB6", "PB8"], "sda": ["PA14", "PB7", "PB9"]}
                ),
                PeripheralFixedPin(
                    "SWD",
                    SwdTargetPort(dio_ft_model),
                    {"swdio": "PA13", "swclk": "PA14", "reset": "NRST"},  # TODO some are FTf pins  # note: SWO is PB3
                ),
            ]
        ).remap_pins(self._PIN_MAPPING)
