BerkeleyHCI/PolymorphicBlocks/edg/abstract_parts/Switch.py

from typing import Any, Dict
from typing_extensions import override

from ..electronics_interfaces import *


@abstract_block
class Switch(KiCadImportableBlock, DiscreteComponent):
    """Two-ported device that closes a circuit when pressed."""

    @override
    def symbol_pinning(self, symbol_name: str) -> Dict[str, BasePort]:
        assert symbol_name == "Switch:SW_SPST"
        return {"1": self.sw, "2": self.com}

    def __init__(self, voltage: RangeLike, current: RangeLike = 0 * Amp(tol=0)) -> None:
        super().__init__()

        self.sw = self.Port(Passive.empty())
        self.com = self.Port(Passive.empty())

        self.current = self.ArgParameter(current)
        self.voltage = self.ArgParameter(voltage)


@abstract_block
class TactileSwitch(Switch):
    """Abstract class (category) for a tactile switch."""


@abstract_block
class MechanicalKeyswitch(Switch):
    """Abstract class (category) for a mechanical keyboard switch, including sockets."""


@abstract_block
class RotaryEncoder(DiscreteComponent):
    """Rotary encoder with discrete clicks and a quadrature signal (A/B/Common).
    Includes shaft-type encoders as well as thumbwheels."""

    def __init__(self, voltage: RangeLike, current: RangeLike = 0 * Amp(tol=0)) -> None:
        super().__init__()

        self.a = self.Port(Passive.empty())
        self.b = self.Port(Passive.empty())
        self.com = self.Port(Passive.empty())

        self.current = self.ArgParameter(current)
        self.voltage = self.ArgParameter(voltage)


class RotaryEncoderSwitch(BlockInterfaceMixin[RotaryEncoder]):
    """Rotary encoder mixin adding a switch pin (sharing a common with the encoder),
    with ratings assumed to be the same between the switch and encoder."""

    def __init__(self, *args: Any, **kwargs: Any) -> None:
        super().__init__(*args, **kwargs)

        self.sw = self.Port(Passive.empty(), optional=True)


@abstract_block
class DirectionSwitch(DiscreteComponent):
    """Directional switch with a, b, c, d (clockwise) switches and common."""

    def __init__(self, voltage: RangeLike, current: RangeLike = 0 * Amp(tol=0)) -> None:
        super().__init__()

        self.a = self.Port(Passive.empty())
        self.b = self.Port(Passive.empty())
        self.c = self.Port(Passive.empty())
        self.d = self.Port(Passive.empty())
        self.com = self.Port(Passive.empty())

        self.current = self.ArgParameter(current)
        self.voltage = self.ArgParameter(voltage)


class DirectionSwitchCenter(BlockInterfaceMixin[DirectionSwitch]):
    """DirectionSwitch mixin adding center switch pin (sharing a common with the encoder),
    with ratings assumed to be the same between the switch and encoder."""

    def __init__(self, *args: Any, **kwargs: Any) -> None:
        super().__init__(*args, **kwargs)

        self.center = self.Port(Passive.empty(), optional=True)


class DigitalSwitch(HumanInterface):
    """Wrapper around Switch that provides a digital port which is pulled low (to GND) when pressed."""

    def __init__(self) -> None:
        super().__init__()

        self.gnd = self.Port(Ground(), [Common])
        self.out = self.Port(DigitalSource.low_from_supply(self.gnd), [Output])

    @override
    def contents(self) -> None:
        super().contents()
        self.package = self.Block(Switch(current=self.out.link().current_draw, voltage=self.out.link().voltage))

        self.connect(self.out.net, self.package.sw)
        self.connect(self.gnd.net, self.package.com)


@abstract_block_default(lambda: DigitalWrapperRotaryEncoder)
class DigitalRotaryEncoder(HumanInterface):
    """Wrapper around RotaryEncoder that provides digital ports that are pulled low (to GND) when pressed."""

    def __init__(self) -> None:
        super().__init__()

        self.gnd = self.Port(Ground.empty(), [Common])
        self.a = self.Port(DigitalSource.empty())
        self.b = self.Port(DigitalSource.empty())


class DigitalWrapperRotaryEncoder(DigitalRotaryEncoder):
    """Basic implementation for DigitalRotaryEncoder as a wrapper around a passive-typed RotaryEncoder."""

    @override
    def contents(self) -> None:
        super().contents()

        self.gnd.init_from(Ground())
        dio_model = DigitalSource.low_from_supply(self.gnd)
        self.a.init_from(dio_model)
        self.b.init_from(dio_model)

        self.package = self.Block(
            RotaryEncoder(
                current=self.a.link().current_draw.hull(self.b.link().current_draw),
                voltage=self.a.link().voltage.hull(self.b.link().voltage),
            )
        )
        self.connect(self.a.net, self.package.a)
        self.connect(self.b.net, self.package.b)
        self.connect(self.gnd.net, self.package.com)


@abstract_block_default(lambda: DigitalWrapperRotaryEncoderWithSwitch)
class DigitalRotaryEncoderSwitch(BlockInterfaceMixin[DigitalRotaryEncoder]):
    """DigitalRotaryEncoder mixin adding a switch pin."""

    def __init__(self, *args: Any, **kwargs: Any) -> None:
        super().__init__(*args, **kwargs)

        self.sw = self.Port(DigitalSource.empty(), optional=True)


class DigitalWrapperRotaryEncoderWithSwitch(DigitalRotaryEncoderSwitch, DigitalWrapperRotaryEncoder, GeneratorBlock):
    @override
    def contents(self) -> None:
        super().contents()
        self.generator_param(self.sw.is_connected())

    @override
    def generate(self) -> None:
        super().generate()
        if self.get(self.sw.is_connected()):
            self.sw.init_from(DigitalSource.low_from_supply(self.gnd))
            package_sw = self.package.with_mixin(RotaryEncoderSwitch())
            self.connect(self.sw.net, package_sw.sw)


@abstract_block_default(lambda: DigitalWrapperDirectionSwitch)
class DigitalDirectionSwitch(HumanInterface):
    """Wrapper around DirectionSwitch that provides digital ports that are pulled low (to GND) when pressed."""

    def __init__(self) -> None:
        super().__init__()

        self.gnd = self.Port(Ground.empty(), [Common])
        self.a = self.Port(DigitalSource.empty())
        self.b = self.Port(DigitalSource.empty())
        self.c = self.Port(DigitalSource.empty())
        self.d = self.Port(DigitalSource.empty())


class DigitalWrapperDirectionSwitch(DigitalDirectionSwitch):
    """Basic implementation for DigitalDirectionSwitch as a wrapper around a passive-typed DirectionSwitch."""

    @override
    def contents(self) -> None:
        super().contents()

        self.gnd.init_from(Ground())
        dio_model = DigitalSource.low_from_supply(self.gnd)
        self.a.init_from(dio_model)
        self.b.init_from(dio_model)
        self.c.init_from(dio_model)
        self.d.init_from(dio_model)

        self.package = self.Block(
            DirectionSwitch(
                current=self.a.link().current_draw.hull(self.b.link().current_draw),
                voltage=self.a.link().voltage.hull(self.b.link().voltage),
            )
        )
        self.connect(self.a.net, self.package.a)
        self.connect(self.b.net, self.package.b)
        self.connect(self.c.net, self.package.c)
        self.connect(self.d.net, self.package.d)
        self.connect(self.gnd.net, self.package.com)


@abstract_block_default(lambda: DigitalWrapperDirectionSwitchWithCenter)
class DigitalDirectionSwitchCenter(BlockInterfaceMixin[DigitalDirectionSwitch]):
    """DigitalRotaryEncoder mixin adding a switch pin."""

    def __init__(self, *args: Any, **kwargs: Any) -> None:
        super().__init__(*args, **kwargs)

        self.center = self.Port(DigitalSource.empty(), optional=True)


class DigitalWrapperDirectionSwitchWithCenter(
    DigitalDirectionSwitchCenter, DigitalWrapperDirectionSwitch, GeneratorBlock
):
    @override
    def contents(self) -> None:
        super().contents()
        self.generator_param(self.center.is_connected())

    @override
    def generate(self) -> None:
        super().generate()
        if self.get(self.center.is_connected()):
            self.center.init_from(DigitalSource.low_from_supply(self.gnd))
            package_sw = self.package.with_mixin(DirectionSwitchCenter())
            self.connect(self.center.net, package_sw.center)
