BerkeleyHCI/PolymorphicBlocks/edg/circuits/PowerConditioning.py

from typing import Optional

from deprecated import deprecated
from typing_extensions import override

from ..abstract_parts import *


class SingleDiodePowerMerge(PowerConditioner, Block):
    """Single-diode power merge block for two voltage sources, where the lower voltage one is diode-gated and less
    preferred if both are connected.
    """

    def __init__(self, voltage_drop: RangeLike = (0, 0.6) * Volt) -> None:
        super().__init__()

        self.pwr_in = self.Port(VoltageSink(current_draw=RangeExpr()))  # high-priority source
        self.pwr_in_diode = self.Port(VoltageSink(current_draw=RangeExpr()))  # low-priority source
        self.pwr_out = self.Port(
            VoltageSource(  # use the spec voltage drop to avoid circular dependencies downstream
                voltage=self.pwr_in.link().voltage.hull(self.pwr_in_diode.link().voltage - voltage_drop),
            )
        )

        self.diode = self.Block(
            Diode(
                reverse_voltage=(0, self.pwr_in.link().voltage.upper() - self.pwr_in_diode.link().voltage.lower()),
                current=self.pwr_out.link().current_draw,
                voltage_drop=voltage_drop,
            )
        )

        self.require(
            self.pwr_in_diode.link().voltage.upper() - self.diode.voltage_drop.lower()
            <= self.pwr_in.link().voltage.lower()
        )
        self.assign(self.pwr_in.current_draw, self.pwr_out.link().current_draw)
        self.assign(self.pwr_in_diode.current_draw, self.pwr_out.link().current_draw)

        self.connect(self.pwr_in_diode.net, self.diode.anode)
        self.connect(self.pwr_out.net, self.pwr_in.net, self.diode.cathode)


class DiodePowerMerge(PowerConditioner, GeneratorBlock):
    """Diode power merge block for multiple voltage sources."""

    def __init__(self, voltage_drop: RangeLike = (0, 0.6) * Volt) -> None:
        super().__init__()
        self.voltage_drop = self.ArgParameter(voltage_drop)

        self.pwr_ins = self.Port(Vector(VoltageSink.empty()))
        self.pwr_out = self.Port(VoltageSource(voltage=RangeExpr()))
        self.generator_param(self.pwr_ins.requested())

    @override
    def generate(self) -> None:
        super().generate()

        input_hull = self.pwr_ins.map_extract(lambda pwr_in: pwr_in.link().voltage).hull()
        # use the spec voltage drop to avoid circular dependencies downstream
        self.assign(self.pwr_out.voltage, input_hull - self.voltage_drop)

        requested = self.get(self.pwr_ins.requested())
        assert len(requested) > 0, "power inputs required"

        self.diodes = ElementDict[Diode]()
        self.pwr_ins.defined()
        for name in requested:
            pwr_in = self.pwr_ins.append_elt(VoltageSink(current_draw=self.pwr_out.link().current_draw), name)
            self.diodes[name] = diode = self.Block(
                Diode(
                    reverse_voltage=(0, self.pwr_out.voltage.upper() - pwr_in.link().voltage.lower()),
                    current=self.pwr_out.link().current_draw,
                    voltage_drop=self.voltage_drop,
                )
            )
            self.connect(pwr_in.net, diode.anode)
            self.connect(self.pwr_out.net, diode.cathode)

    @property
    @deprecated(f"replaced with pwr_ins.request(...)")
    def pwr_in1(self) -> VoltageSink:
        return self.pwr_ins.request("1")

    @property
    @deprecated(f"replaced with pwr_ins.request(...)")
    def pwr_in2(self) -> VoltageSink:
        return self.pwr_ins.request("2")


class PriorityPowerOr(PowerConditioner, KiCadSchematicBlock, Block):
    """Power merge block for two power inputs, where the high priority input (e.g. USB) is higher voltage and
    the low priority input is lower voltage (e.g. battery).
    The higher priority input incurs a diode drop, while the lower priority input has a FET.
    As a side effect, the FET power path also acts as reverse polarity protection.
    """

    def __init__(self, diode_voltage_drop: RangeLike, fet_rds_on: RangeLike) -> None:
        super().__init__()

        self.gnd = self.Port(Ground.empty())
        self.pwr_hi = self.Port(VoltageSink.empty())  # high-priority higher-voltage source
        self.pwr_lo = self.Port(VoltageSink.empty())  # low-priority lower-voltage source
        self.pwr_out = self.Port(VoltageSource.empty())

        self.diode_voltage_drop = self.ArgParameter(diode_voltage_drop)
        self.fet_rds_on = self.ArgParameter(fet_rds_on)

    @override
    def contents(self) -> None:
        super().contents()

        # FET behavior requires the high priority path to be higher voltage
        self.require(self.pwr_hi.link().voltage.lower() > self.pwr_lo.link().voltage.upper())

        output_current_draw = self.pwr_out.link().current_draw
        self.pdr = self.Block(Resistor(10 * kOhm(tol=0.01)))
        self.diode = self.Block(
            Diode(
                reverse_voltage=(0, self.pwr_lo.link().voltage.upper()),
                current=output_current_draw,
                voltage_drop=self.diode_voltage_drop,
            )
        )
        self.fet = self.Block(
            Fet.PFet(  # doesn't account for reverse protection
                drain_voltage=(0, self.pwr_hi.link().voltage.upper() - self.pwr_lo.link().voltage.lower()),
                drain_current=output_current_draw,
                # gate voltage accounts for a possible power on transient
                gate_voltage=(-self.pwr_hi.link().voltage.upper(), (self.pwr_hi.link().voltage.upper())),
                rds_on=self.fet_rds_on,
            )
        )

        self.import_kicad(
            self.file_path("resources", f"{self.__class__.__name__}.kicad_sch"),
            conversions={
                "pwr_hi": VoltageSink(current_draw=output_current_draw),
                "pwr_lo": VoltageSink(current_draw=output_current_draw),
                "pwr_out": VoltageSource(
                    voltage=self.pwr_lo.link().voltage.hull(
                        # use the spec voltage drop since using the actual voltage drop causes a circular dependency
                        # (where current depends on voltage, but the diode voltage drop depends on the diode selection
                        # which depends on the current through)
                        self.pwr_hi.link().voltage
                        - self.diode_voltage_drop
                    ),
                ),
                "gnd": Ground(),
            },
        )

    def connected_from(
        self,
        gnd: Optional[Port[GroundLink]] = None,
        pwr_hi: Optional[Port[VoltageLink]] = None,
        pwr_lo: Optional[Port[VoltageLink]] = None,
    ) -> "PriorityPowerOr":
        """Convenience function to connect ports, returning this object so it can still be given a name."""
        if gnd is not None:
            builder.block().connect(gnd, self.gnd)
        if pwr_hi is not None:
            builder.block().connect(pwr_hi, self.pwr_hi)
        if pwr_lo is not None:
            builder.block().connect(pwr_lo, self.pwr_lo)
        return self


class PmosReverseProtection(PowerConditioner, KiCadSchematicBlock, Block):
    """Reverse polarity protection using a PMOS. This method has lower power loss over diode-based protection.
    100R-330R is good but 1k-50k can be used for continuous load.
    Not reverse / bidirectional current flow capable (eg, can't charge a battery through this).
    Ref: https://components101.com/articles/design-guide-pmos-mosfet-for-reverse-voltage-polarity-protection
    """

    def __init__(self, gate_resistor: RangeLike = 10 * kOhm(tol=0.05), rds_on: RangeLike = (0, 0.1) * Ohm):
        super().__init__()
        self.gnd = self.Port(Ground.empty(), [Common])
        self.pwr_in = self.Port(VoltageSink.empty(), [Input])
        self.pwr_out = self.Port(VoltageSource.empty(), [Output])

        self.gate_resistor = self.ArgParameter(gate_resistor)
        self.rds_on = self.ArgParameter(rds_on)

    @override
    def contents(self) -> None:
        super().contents()
        output_current_draw = self.pwr_out.link().current_draw
        self.fet = self.Block(
            Fet.PFet(
                drain_voltage=(0, self.pwr_out.link().voltage.upper()),
                drain_current=output_current_draw,
                gate_voltage=(-self.pwr_out.link().voltage.upper(), self.pwr_out.link().voltage.upper()),
                rds_on=self.rds_on,
            )
        )

        # TODO: generate zener diode + resistor for high voltage applications
        #  self.diode = self.Block(ZenerDiode(self.clamp_voltage))

        self.import_kicad(
            self.file_path("resources", f"{self.__class__.__name__}.kicad_sch"),
            conversions={
                "pwr_in": VoltageSink(
                    current_draw=output_current_draw,
                ),
                "pwr_out": VoltageSource(
                    voltage=self.pwr_in.link().voltage,
                ),
                "gnd": Ground(),
            },
        )


class PmosChargerReverseProtection(PowerConditioner, KiCadSchematicBlock, Block):
    """PMOS-based reverse voltage protection, with charging (reverse / bidirectional flow) capability
    using additional FETs.

    The highest battery voltage is bounded by the transistors' Vgs/Vds.
    There is also a rare case when this circuit being disconnected when a charger is connected first.
    But always reverse protect. R1 and R2 are the pullup bias resistors for mp1 and mp2 PFet.
    More info at: https://www.edn.com/reverse-voltage-protection-for-battery-chargers/
    """

    def __init__(
        self,
        r1_val: RangeLike = 100 * kOhm(tol=0.01),
        r2_val: RangeLike = 100 * kOhm(tol=0.01),
        rds_on: RangeLike = (0, 0.1) * Ohm,
    ):
        super().__init__()

        self.gnd = self.Port(Ground.empty(), [Common])
        self.pwr_in = self.Port(VoltageSink.empty(), [Input], doc="Power input from the battery")

        self.pwr_out = self.Port(
            VoltageSource.empty(),
            [Output],
            doc="Power output for a load which will be also reverse protected from the battery",
        )

        self.r1_val = self.ArgParameter(r1_val)
        self.r2_val = self.ArgParameter(r2_val)
        self.rds_on = self.ArgParameter(rds_on)

    @override
    def contents(self) -> None:
        super().contents()
        self.r1 = self.Block(Resistor(resistance=self.r1_val))
        self.r2 = self.Block(Resistor(resistance=self.r2_val))

        # use the maximum voltages and currents accounting for both directions
        batt_voltage = self.pwr_in.link().voltage.hull(self.pwr_out.link().reverse_voltage)
        batt_current = self.pwr_out.link().current_draw.hull(self.pwr_in.link().reverse_current_draw)

        power = batt_current * batt_current * self.rds_on
        r1_current = batt_voltage / self.r1.resistance

        # Create the PMOS transistors and resistors based on the provided schematic
        self.mp1 = self.Block(
            Fet.PFet(
                drain_voltage=batt_voltage,
                drain_current=r1_current,
                gate_voltage=(-batt_voltage.upper(), batt_voltage.upper()),
                rds_on=self.rds_on,
            )
        )
        self.mp2 = self.Block(
            Fet.PFet(
                drain_voltage=batt_voltage,
                drain_current=batt_current,
                gate_voltage=(-batt_voltage.upper(), batt_voltage.upper()),
                rds_on=self.rds_on,
                power=power,
            )
        )

        self.import_kicad(
            self.file_path("resources", f"{self.__class__.__name__}.kicad_sch"),
            conversions={
                "pwr_in": VoltageSink(
                    current_draw=batt_current,
                    reverse_voltage=self.pwr_out.link().reverse_voltage,
                    reverse_current_limits=RangeExpr.ALL,
                ),
                "pwr_out": VoltageSource(
                    voltage=batt_voltage,
                    reverse_voltage_limits=self.pwr_in.link().reverse_voltage_limits,
                    reverse_current_draw=self.pwr_in.link().reverse_current_draw,
                ),
                "gnd": Ground(),
            },
        )

    @property
    @deprecated(f"chg_in is deprecated and unified with sink-capable (bidirectional) pwr_out")
    def chg_in(self) -> VoltageSource:
        return self.pwr_out

    @property
    @deprecated(f"chg_out is deprecated and unified with source-capable (bidirectional) pwr_in")
    def chg_out(self) -> VoltageSink:
        return self.pwr_in


class SoftPowerGate(PowerSwitch, KiCadSchematicBlock, Block):  # migrate from the multimater
    """A high-side PFET power gate that has a button to power on, can be latched on by an external signal,
    and provides the button output as a signal.
    """

    def __init__(
        self,
        pull_resistance: RangeLike = 10 * kOhm(tol=0.05),
        amp_resistance: RangeLike = 10 * kOhm(tol=0.05),
        diode_drop: RangeLike = (0, 0.6) * Volt,
    ):
        super().__init__()
        self.pwr_in = self.Port(VoltageSink.empty(), [Input])
        self.pwr_out = self.Port(VoltageSource.empty(), [Output], doc="Gate controlled power out")
        self.gnd = self.Port(Ground.empty(), [Common])

        self.btn_out = self.Port(
            DigitalSource.empty(),
            optional=True,
            doc="Allows the button state to be read independently of the control signal. Open-drain.",
        )
        self.btn_in = self.Port(
            DigitalBidir.empty(),
            doc="Connect to button that pulls down to GND to turn on power. Do not connect to GPIO.",
        )
        self.control = self.Port(
            DigitalSink.empty(), doc="external control to latch the power on"
        )  # digital level control - gnd-referenced NFET gate

        self.pull_resistance = self.ArgParameter(pull_resistance)
        self.amp_resistance = self.ArgParameter(amp_resistance)
        self.diode_drop = self.ArgParameter(diode_drop)

    @override
    def contents(self) -> None:
        super().contents()
        control_voltage = self.btn_in.link().voltage.hull(self.gnd.link().voltage)
        pwr_voltage = self.pwr_out.link().voltage.hull(self.gnd.link().voltage)
        pwr_current = self.pwr_out.link().current_draw.hull(RangeExpr.ZERO)

        self.pull_res = self.Block(Resistor(resistance=self.pull_resistance))
        self.pwr_fet = self.Block(
            Fet.PFet(
                drain_voltage=pwr_voltage,
                drain_current=pwr_current,
                gate_voltage=(-control_voltage.upper(), control_voltage.upper()),  # TODO this ignores the diode drop
            )
        )

        self.amp_res = self.Block(Resistor(resistance=self.amp_resistance))
        self.amp_fet = self.Block(
            Fet.NFet(
                drain_voltage=control_voltage,
                drain_current=RangeExpr.ZERO,  # effectively no current
                gate_voltage=(self.control.link().output_thresholds.upper(), self.control.link().voltage.upper()),
            )
        )

        self.ctl_diode = self.Block(
            Diode(
                reverse_voltage=control_voltage,
                current=RangeExpr.ZERO,  # effectively no current
                voltage_drop=self.diode_drop,
            )
        )

        self.btn_diode = self.Block(
            Diode(
                reverse_voltage=control_voltage,
                current=RangeExpr.ZERO,  # effectively no current
                voltage_drop=self.diode_drop,
            )
        )

        self.import_kicad(
            self.file_path("resources", f"{self.__class__.__name__}.kicad_sch"),
            conversions={
                "pwr_in": VoltageSink(
                    current_draw=self.pwr_out.link().current_draw,
                ),
                "pwr_out": VoltageSource(
                    voltage=self.pwr_in.link().voltage,
                ),
                "control": DigitalSink(),  # TODO more modeling here?
                "gnd": Ground(),
                "btn_out": DigitalSource.low_from_supply(self.gnd),
                "btn_in": DigitalBidir(
                    voltage=self.gnd.link().voltage,
                    output_thresholds=(self.gnd.link().voltage.upper(), float("inf")),
                    pullup_capable=True,
                ),
            },
        )


class SoftPowerSwitch(PowerSwitch, Block):
    """A software power switch that adds a power button a user can turn on"""

    def __init__(
        self,
        pull_resistance: RangeLike = 10 * kOhm(tol=0.05),
        amp_resistance: RangeLike = 10 * kOhm(tol=0.05),
        diode_drop: RangeLike = (0, 0.4) * Volt,
    ):
        super().__init__()
        self.pwr_gate = self.Block(SoftPowerGate(pull_resistance, amp_resistance, diode_drop))
        self.gnd = self.Export(self.pwr_gate.gnd, [Common])
        self.pwr_in = self.Export(self.pwr_gate.pwr_in, [Input])
        self.pwr_out = self.Export(self.pwr_gate.pwr_out, [Output])
        self.btn_out = self.Export(self.pwr_gate.btn_out)
        self.control = self.Export(self.pwr_gate.control)

    @override
    def contents(self) -> None:
        super().contents()
        with self.implicit_connect(
            ImplicitConnect(self.gnd, [Common]),
        ) as imp:
            self.btn = imp.Block(DigitalSwitch())
        self.connect(self.pwr_gate.btn_in, self.btn.out)
