BerkeleyHCI/PolymorphicBlocks/edg/parts/microcontroller/Esp32.py

from typing import *

from typing_extensions import override

from ...circuits import *
from ...vendor_parts.jlc.JlcPart import JlcPart
from .EspCommon import HasEspProgramming


@non_library
class Esp32_Interfaces(
    IoControllerSpiPeripheral,
    IoControllerI2cTarget,
    IoControllerTouchDriver,
    IoControllerDac,
    IoControllerCan,
    IoControllerDvp8,
    IoControllerI2s,
    IoControllerWifi,
    IoControllerBle,
    IoControllerBluetooth,
    BaseIoController,
):
    """Defines base interfaces for ESP32 microcontrollers"""


class Esp32_Wroom_32_Device(
    Esp32_Interfaces,
    InternalSubcircuit,
    BaseIoControllerModelable,
    BaseIoControllerPinmapGenerator,
    FootprintBlock,
    JlcPart,
):
    """ESP32-WROOM-32 module

    Module datasheet: https://www.espressif.com/sites/default/files/documentation/esp32-wroom-32e_esp32-wroom-32ue_datasheet_en.pdf
    """

    _PIN_MAPPING = {
        "SENSOR_VP": "4",
        "SENSOR_VN": "5",
        "VDET_1": "6",
        "VDET_2": "7",
        "32K_XP": "8",
        "32K_XN": "9",
        "GPIO25": "10",
        "GPIO26": "11",
        "GPIO27": "12",
        "MTMS": "13",
        "MTDI": "14",  # aka GPIO12
        "MTCK": "16",
        # pins 17-22 NC
        "MTDO": "23",  # aka GPIO15
        "GPIO4": "26",
        "GPIO16": "27",  # for QSPI PSRAM variants this cannot be used
        "GPIO17": "28",
        "GPIO5": "29",
        "GPIO18": "30",
        "GPIO19": "31",
        # pin 32 NC
        "GPIO21": "33",
        "GPIO22": "36",
        "GPIO23": "37",
    }

    def __init__(self, **kwargs: Any) -> None:
        super().__init__(**kwargs)

        self.pwr = self.Port(
            VoltageSink(
                voltage_limits=(3.0, 3.6) * Volt,  # section 5.2, table 14, most restrictive limits
                current_draw=(0.001, 370) * mAmp
                + self.io_current_draw.upper(),  # from power off (table 8) to RF working (WRROM datasheet table 9)
            ),
            [Power],
        )
        self.gnd = self.Port(Ground(), [Common])

        self._dio_model = DigitalBidir.from_supply(  # section 5.2, table 15
            self.gnd,
            self.pwr,
            voltage_limit_tolerance=(-0.3, 0.3) * Volt,
            current_limits=(-28, 40) * mAmp,
            input_threshold_factor=(0.25, 0.75),
            pullup_capable=True,
            pulldown_capable=True,
        )
        self.chip_pu = self.Port(self._dio_model, optional=self._model)
        # section 2.4, table 5: strapping IOs that need a fixed value to boot, TODO currently not allocatable post-boot
        self.io0 = self.Port(self._dio_model, optional=True)  # default pullup (SPI boot), set low to download boot
        self.io2 = self.Port(
            self._dio_model, optional=True
        )  # default pulldown (enable download boot), ignored during SPI boot

        # similarly, the programming UART is fixed and allocated separately
        self.uart0 = self.Port(UartPort(self._dio_model), optional=True)

    @override
    def generate(self) -> None:
        super().generate()

        self.assign(self.lcsc_part, "C701342")
        self.assign(self.actual_basic_part, False)
        self.footprint(
            "U",
            "RF_Module:ESP32-WROOM-32",
            self._make_pinning(),
            mfr="Espressif Systems",
            part="ESP32-WROOM-32",
            datasheet="https://www.espressif.com/sites/default/files/documentation/esp32-wroom-32e_esp32-wroom-32ue_datasheet_en.pdf",
            pnp_rot=-90,
            pnp_offset=(0, 0.8),
        )

    @override
    def _system_pinmap(self) -> Mapping[Union[Iterable[str], str], Union[Passive, HasPassivePort]]:
        return {
            "2": self.pwr,
            ("1", "15", "38", "39"): self.gnd,
            "3": self.chip_pu,
            "25": self.io0,
            "24": self.io2,
            "34": self.uart0.rx,
            "35": self.uart0.tx,
            # 'MTDO': ...,  # disconnected, internally pulled up for strapping - U0TXD active
            # 'MTDI': ...,  # disconnected, internally pulled down for strapping - 3.3v LDO
        }

    @override
    def _io_pinmap(self) -> PinMapUtil:
        sdio_model = DigitalBidir.from_supply(  # section 5.2, table 15, for SDIO power domain pins
            self.gnd,
            self.pwr,
            voltage_limit_tolerance=(-0.3, 0.3) * Volt,
            current_limits=(-28, 20) * mAmp,  # reduced sourcing capability
            input_threshold_factor=(0.25, 0.75),
            pullup_capable=True,
            pulldown_capable=True,
        )

        adc_model = AnalogSink.from_supply(
            self.gnd,
            self.pwr,
            signal_limit_abs=(0.1, 2.45) * Volt,  # table 3-4, effective ADC range
            # TODO: impedance / leakage - not specified by datasheet
        )

        dac_model = AnalogSource.from_supply(self.gnd, self.pwr)  # TODO: no specs in datasheet?!

        uart_model = UartPort(DigitalBidir.empty(), baud_limit=(0, 5) * MHertz)
        spi_model = SpiController(DigitalBidir.empty(), frequency_limit=(0, 80) * MHertz)  # section 4.1.17
        spi_peripheral_model = SpiPeripheral(DigitalBidir.empty(), frequency_limit=(0, 80) * MHertz)
        i2c_model = I2cController(DigitalBidir.empty(), frequency_limit=(100, 5000) * kHertz)  # section 4.1.11
        i2c_target_model = I2cTarget(DigitalBidir.empty(), frequency_limit=(100, 5000) * kHertz)
        touch_model = TouchDriver()
        can_model = CanControllerPort(DigitalBidir.empty(), bitrate_limit=(12.5, 1000) * kHertz)  # aka TWAI
        i2s_model = I2sController(DigitalBidir.empty())
        dvp8_model = Dvp8Host(DigitalBidir.empty())

        return (
            PinMapUtil(
                [  # section 2.2, table 1
                    # VDD3P3_RTC
                    PinResource("SENSOR_VP", {"ADC1_CH0": adc_model}),  # also input-only 'GPIO36': dio_model, RTC_GPIO
                    PinResource(
                        "SENSOR_CAPP", {"ADC1_CH1": adc_model}
                    ),  # also input-only 'GPIO37': dio_model, RTC_GPIO
                    PinResource(
                        "SENSOR_CAPN", {"ADC1_CH2": adc_model}
                    ),  # also input-only 'GPIO38': dio_model,  RTC_GPIO
                    PinResource("SENSOR_VN", {"ADC1_CH3": adc_model}),  # also input-only 'GPIO39': dio_model, RTC_GPIO
                    PinResource("VDET_1", {"ADC1_CH6": adc_model}),  # also input-only 'GPIO34': dio_model, RTC_GPIO
                    PinResource("VDET_2", {"ADC1_CH7": adc_model}),  # also input-only 'GPIO35': dio_model,  RTC_GPIO
                    PinResource(
                        "32K_XP", {"GPIO32": self._dio_model, "ADC1_CH4": adc_model, "TOUCH9": touch_model}
                    ),  # also RTC_GPIO, 32K_XP
                    PinResource(
                        "32K_XN", {"GPIO33": self._dio_model, "ADC1_CH5": adc_model, "TOUCH8": touch_model}
                    ),  # also RTC_GPIO, 32K_XN
                    PinResource(
                        "GPIO25", {"GPIO25": self._dio_model, "ADC2_CH8": adc_model, "DAC_1": dac_model}
                    ),  # also RTC_GPIO
                    PinResource(
                        "GPIO26", {"GPIO26": self._dio_model, "ADC2_CH9": adc_model, "DAC_2": dac_model}
                    ),  # also RTC_GPIO
                    PinResource(
                        "GPIO27", {"GPIO27": self._dio_model, "ADC2_CH7": adc_model, "TOUCH7": touch_model}
                    ),  # also RTC_GPIO
                    PinResource(
                        "MTMS", {"GPIO14": self._dio_model, "ADC2_CH6": adc_model, "TOUCH6": touch_model}
                    ),  # also RTC_GPIO
                    PinResource(
                        "MTDI", {"GPIO12": self._dio_model, "ADC2_CH5": adc_model, "TOUCH5": touch_model}
                    ),  # also RTC_GPIO, noncritical strapping pin
                    PinResource(
                        "MTCK", {"GPIO13": self._dio_model, "ADC2_CH4": adc_model, "TOUCH4": touch_model}
                    ),  # also RTC_GPIO
                    PinResource(
                        "MTDO", {"GPIO15": self._dio_model, "ADC2_CH3": adc_model, "TOUCH3": touch_model}
                    ),  # also RTC_GPIO, noncritical strapping pin
                    # PinResource('GPIO2', {'GPIO2': self._dio_model, 'ADC2_CH2': adc_model, 'TOUCH2': touch_model}),  # also RTC_GPIO, strapping pin
                    # PinResource('GPIO0', {'GPIO0': self._dio_model, 'ADC2_CH1': adc_model, 'TOUCH1': touch_model}),  # also RTC_GPIO, strapping pin
                    PinResource(
                        "GPIO4", {"GPIO4": self._dio_model, "ADC2_CH0": adc_model, "TOUCH0": touch_model}
                    ),  # also RTC_GPIO
                    # VDD_SDIO
                    PinResource("GPIO16", {"GPIO16": sdio_model}),
                    PinResource("GPIO17", {"GPIO17": sdio_model}),
                    PinResource("SD_DATA_2", {"GPIO9": sdio_model}),
                    PinResource("SD_DATA_3", {"GPIO10": sdio_model}),
                    PinResource("SD_CMD", {"GPIO11": sdio_model}),
                    PinResource("SD_CLK", {"GPIO6": sdio_model}),
                    PinResource("SD_DATA_0", {"GPIO7": sdio_model}),
                    PinResource("SD_DATA_1", {"GPIO8": sdio_model}),
                    # VDD_3P3_CPU
                    PinResource("GPIO5", {"GPIO5": self._dio_model}),
                    PinResource("GPIO18", {"GPIO18": self._dio_model}),
                    PinResource("GPIO23", {"GPIO23": self._dio_model}),
                    PinResource("GPIO19", {"GPIO19": self._dio_model}),
                    PinResource("GPIO22", {"GPIO22": self._dio_model}),
                    # PinResource('U0RXD', {'GPIO3': dio_model}),  # for programming, technically reallocatable
                    # PinResource('U0TXD', {'GPIO1': dio_model}),  # for programming, technically reallocatable
                    PinResource("GPIO21", {"GPIO21": self._dio_model}),
                    # section 4.2, table 12: peripheral pin assignments
                    # note LED and motor PWMs can be assigned to any pin
                    # PeripheralAnyResource('U0', uart_model),  # for programming, technically reallocatable
                    PeripheralAnyResource("U1", uart_model),
                    PeripheralAnyResource("U2", uart_model),
                    PeripheralAnyResource("I2CEXT0", i2c_model),
                    PeripheralAnyResource("I2CEXT1", i2c_model),
                    PeripheralAnyResource("I2CEXT0_T", i2c_target_model),  # TODO shared resource w/ I2C controller
                    PeripheralAnyResource("I2CEXT1_T", i2c_target_model),  # TODO shared resource w/ I2C controller
                    # PeripheralAnyResource('SPI', spi_model),  # for flash, non-allocatable
                    PeripheralAnyResource("HSPI", spi_model),
                    PeripheralAnyResource("VSPI", spi_model),
                    PeripheralAnyResource("HSPI_P", spi_peripheral_model),  # TODO shared resource w/ SPI controller
                    PeripheralAnyResource("VSPI_P", spi_peripheral_model),  # TODO shared resource w/ SPI controller
                    PeripheralAnyResource("TWAI", can_model),
                    PeripheralAnyResource("I2S0", i2s_model),  # while CLK is restricted pinning, SCK = BCK here
                    PeripheralAnyResource("I2S1", i2s_model),
                    PeripheralAnyResource(
                        "DVP", dvp8_model
                    ),  # TODO this also eats an I2S port, also available as 16-bit
                ]
            )
            .remap_pins(self._PIN_MAPPING)
            .filter_pins(self.get(self._allowed_pins))
        )


class Esp32_Wroom_32(
    Microcontroller,
    Radiofrequency,
    HasEspProgramming,
    Resettable,
    Esp32_Interfaces,
    IoControllerPowerRequired,
    GeneratorBlock,
):
    """Wrapper around Esp32c3_Wroom02 with external capacitors and UART programming header.
    NOT COMPATIBLE WITH QSPI PSRAM VARIANTS - for those, GPIO16 needs to be pulled up.
    """

    def __init__(self) -> None:
        super().__init__()
        self.generator_param(self.reset.is_connected())

    @override
    def contents(self) -> None:
        super().contents()

        with self.implicit_connect(ImplicitConnect(self.pwr, [Power]), ImplicitConnect(self.gnd, [Common])) as imp:
            self.ic = imp.Block(Esp32_Wroom_32_Device(pin_assigns=ArrayStringExpr()))
            self._wrap_inner(self.ic)
            self.connect(self.program_uart_node, self.ic.uart0)
            self.connect(self.program_en_node, self.ic.chip_pu)
            self.connect(self.program_boot_node, self.ic.io0)
            # strapping pins are by default pulled to SPI boot, and can be reconfigured to download boot

            self.vcc_cap0 = imp.Block(DecouplingCapacitor(22 * uFarad(tol=0.2)))  # C1
            self.vcc_cap1 = imp.Block(DecouplingCapacitor(0.1 * uFarad(tol=0.2)))  # C2

    @override
    def generate(self) -> None:
        super().generate()

        if self.get(self.reset.is_connected()):
            self.connect(self.reset, self.ic.chip_pu)
        else:
            self.en_pull = self.Block(PullupDelayRc(10 * kOhm(tol=0.05), 10 * mSecond(tol=0.2))).connected(
                gnd=self.gnd, pwr=self.pwr, io=self.ic.chip_pu
            )


class Freenove_Esp32_Wrover_Device(Esp32_Interfaces, BaseIoControllerWrapped, GeneratorBlock, FootprintBlock):
    _PIN_REMAPPING = {
        # 'SENSOR_VP': '3',  # camera CSI_Y6
        # 'SENSOR_VN': '4',  # camera CSI_Y7
        # 'VDET_1': '5',  # input only GPIO34, CSI_Y8
        # 'VDET_2': '6',  # input only GPIO35, CSI_Y9
        "32K_XP": "7",  # GPIO32
        "32K_XN": "8",  # GPIO33
        # 'GPIO25': '9',  # camera CSI_VYSNC
        # 'GPIO26': '10',  # camera I2C_SDA
        # 'GPIO27': '11',  # camera I2C_SCL
        "MTMS": "12",  # GPIO14
        "MTDI": "13",  # GPIO12
        "MTCK": "15",  # GPIO13
        # 'SD_DATA_2': '16',  # FLASH_D2, SD2
        # 'SD_DATA_3': '17',  # DLASH_D3, SD3
        # 'SD_CMD': '18',  # FLASH_CMD, CMD
        # 'SD_CLK': '22',  # FLASH_CLK, SD0
        # 'SD_DATA_0': '23',  # FLASH_D0, SD1
        # 'SD_DATA_1': '24',  # FLASH_D1, SD1
        "MTDO": "25",  # GPIO15
        # 'GPIO4': '28',  # camera CSI_Y2
        # 'GPIO5': '31',  # camera CSI_Y3
        # 'GPIO18': '32',  # camera CSI_Y4
        # 'GPIO19': '33',  # camera CSI_Y5
        # 'GPIO21': '35',  # camera XCLK
        # 'GPIO22': '38',  # camera CSI_PCLK
        # 'GPIO23': '39',  # camera CSI_HREF
    }

    def __init__(self, **kwargs: Any) -> None:
        super().__init__(**kwargs)
        self.gnd = self.Port(Ground.empty(), optional=True)
        self.v3v3 = self.Port(Passive.empty(), optional=True)
        self.vcc = self.Port(Passive.empty(), optional=True)  # VUsb
        self.generator_param(self.pin_assigns)
        self._generator_param_all_ios()

    @override
    def generate(self) -> None:
        super().generate()

        self.footprint(
            "U",
            "edg:Freenove_ESP32-WROVER",
            self._make_pinning(
                {
                    "1": self.v3v3,  # 3v3, output of internal AMS1117-3.3V LDO
                    "19": self.vcc,  # Vcc 5vUSB, input to internal LDO
                    "20": self.vcc,
                    "14": self.gnd,
                    "21": self.gnd,
                    "29": self.gnd,
                    "30": self.gnd,
                    "34": self.gnd,
                    "40": self.gnd,
                },
                self._PIN_REMAPPING,
            ),
            mfr="",
            part="Freenove ESP32-WROVER",
        )


class Freenove_Esp32_Wrover(
    IoControllerUsbOut,
    IoControllerPowerOut,
    Esp32_Interfaces,
    IoController,
    BaseIoControllerWrapper,
    GeneratorBlock,
    WrapperSubboardBlock,
):
    """ESP32-WROVER-DEV breakout with camera.

    Module datasheet: https://www.espressif.com/sites/default/files/documentation/esp32-wrover-e_esp32-wrover-ie_datasheet_en.pdf
    Board used: https://amazon.com/ESP32-WROVER-Contained-Compatible-Bluetooth-Tutorials/dp/B09BC1N9LL
    Board internal schematic: https://github.com/Freenove/Freenove_ESP32_WROVER_Board/blob/f710fd6976e76ab76c29c2ee3042cd7bac22c3d6/Datasheet/ESP32_Schematic.pdf

    Top left is pin 1, going down the left side then up the right side.
    Up is defined from the text orientation (antenna is on top).
    """

    def __init__(self, **kwargs: Any) -> None:
        super().__init__(**kwargs)

        self.vusb_out.init_from(
            VoltageSource(voltage=UsbConnector.USB2_VOLTAGE_RANGE, current_limits=UsbConnector.USB2_CURRENT_LIMITS)
        )

        self.generator_param(
            self.gnd.is_connected(),
            self.pwr.is_connected(),
            self.pwr_out.is_connected(),
            self.vusb_out.is_connected(),
            self.pin_assigns,
        )
        self._generator_param_all_ios()

    @override
    def generate(self) -> None:
        super().generate()

        self.model = self.Block(
            Esp32_Wroom_32_Device(pin_assigns=ArrayStringExpr(), _model=True, _allowed_pins=ArrayStringExpr())
        )
        self.device = self.Block(Freenove_Esp32_Wrover_Device(pin_assigns=ArrayStringExpr()), external=True)
        self._wrap_inner_model_device(self.model, self.device, Freenove_Esp32_Wrover_Device._PIN_REMAPPING)

        self.connect(self._generate_gnd_node(), self.model.gnd)
        self.export_tap(self.gnd, self.device.gnd)

        self.connect(
            self._generate_pwr_node(
                voltage=3.3 * Volt(tol=0.05),
                current_limits=UsbConnector.USB2_CURRENT_LIMITS,  # tolerance is a guess
            ),
            self.model.pwr,
        )
        self.export_tap((self.pwr if self.get(self.pwr.is_connected()) else self.pwr_out).net, self.device.v3v3)

        self.export_tap(self.vusb_out.net, self.device.vcc)
