BerkeleyHCI/PolymorphicBlocks/edg/circuits/OpampCircuits.py

from math import ceil, log10
from typing import List, Tuple, Dict, Mapping

from typing_extensions import override

from ..abstract_parts import *
from ..electronics_interfaces.DummyDevices import ForcedAnalogSignal
from .ResistiveDivider import ResistiveDivider


class OpampFollower(OpampApplication, KiCadSchematicBlock, KiCadImportableBlock):
    """Opamp follower circuit, outputs the same signal as the input (but probably stronger)."""

    @override
    def symbol_pinning(self, symbol_name: str) -> Mapping[str, BasePort]:
        assert symbol_name == "edg_importable:Follower"
        return {"1": self.input, "3": self.output, "V+": self.pwr, "V-": self.gnd}

    def __init__(self) -> None:
        super().__init__()
        self.pwr = self.Port(VoltageSink.empty(), [Power])
        self.gnd = self.Port(Ground.empty(), [Common])

        self.input = self.Port(AnalogSink.empty(), [Input])
        self.output = self.Port(AnalogSource.empty(), [Output])

    @override
    def contents(self) -> None:
        super().contents()

        self.amp = self.Block(Opamp())
        self.forced = self.Block(ForcedAnalogSignal(self.input.link().signal))

        self.import_kicad(self.file_path("resources", f"{self.__class__.__name__}.kicad_sch"))


class AmplifierValues(ESeriesRatioValue["AmplifierValues"]):
    def __init__(self, amplification: Range, parallel_impedance: Range):
        self.amplification = amplification  # amplification factor from in to out
        self.parallel_impedance = parallel_impedance  # parallel impedance into the opamp negative pin

    @staticmethod
    @override
    def from_resistors(r1_range: Range, r2_range: Range) -> "AmplifierValues":
        """r2 is the low-side resistor (Vin- to GND) and r1 is the high-side resistor (Vin- to Vout)."""
        return AmplifierValues((r1_range / r2_range) + 1, 1 / (1 / r1_range + 1 / r2_range))

    @override
    def initial_test_decades(self) -> Tuple[int, int]:
        decade = ceil(log10(self.parallel_impedance.center()))
        return decade, decade

    @override
    def distance_to(self, spec: "AmplifierValues") -> List[float]:
        if self.amplification in spec.amplification and self.parallel_impedance in spec.parallel_impedance:
            return []
        else:
            return [
                abs(self.amplification.center() - spec.amplification.center()),
                abs(self.parallel_impedance.center() - spec.parallel_impedance.center()),
            ]

    @override
    def intersects(self, spec: "AmplifierValues") -> bool:
        return self.amplification.intersects(spec.amplification) and self.parallel_impedance.intersects(
            spec.parallel_impedance
        )


class Amplifier(OpampApplication, KiCadSchematicBlock, KiCadImportableBlock, GeneratorBlock):
    """Opamp non-inverting amplifier, outputs a scaled-up version of the input signal.

    From https://en.wikipedia.org/wiki/Operational_amplifier_applications#Non-inverting_amplifier:
    Vout = Vin (1 + R1/R2)

    The input and output impedances given are a bit more complex, so this simplifies it to
    the opamp's specified pin impedances - TODO: is this correct(ish)?
    """

    @override
    def symbol_pinning(self, symbol_name: str) -> Dict[str, BasePort]:
        mapping: Dict[str, Dict[str, BasePort]] = {
            "Simulation_SPICE:OPAMP": {
                "+": self.input,
                "-": self.reference,
                "3": self.output,
                "V+": self.pwr,
                "V-": self.gnd,
            },
            "edg_importable:Amplifier": {
                "+": self.input,
                "R": self.reference,
                "3": self.output,
                "V+": self.pwr,
                "V-": self.gnd,
            },
        }
        return mapping[symbol_name]

    def __init__(
        self,
        amplification: RangeLike,
        impedance: RangeLike = (10, 100) * kOhm,
        *,
        series: IntLike = 24,
        tolerance: FloatLike = 0.01,
    ):  # to be overridden by refinements
        super().__init__()

        self.pwr = self.Port(VoltageSink.empty(), [Power])
        self.gnd = self.Port(Ground.empty(), [Common])

        self.input = self.Port(AnalogSink.empty(), [Input])
        self.output = self.Port(AnalogSource.empty(), [Output])
        self.reference = self.Port(AnalogSink.empty(), optional=True)  # optional zero reference, defaults to GND

        self.amplification = self.ArgParameter(amplification)
        self.impedance = self.ArgParameter(impedance)
        self.series = self.ArgParameter(series)
        self.tolerance = self.ArgParameter(tolerance)
        self.generator_param(
            self.amplification, self.impedance, self.series, self.tolerance, self.reference.is_connected()
        )

        self.actual_amplification = self.Parameter(RangeExpr())

    @override
    def contents(self) -> None:
        super().contents()

        self.description = DescriptionString(
            "<b>amplification:</b> ",
            DescriptionString.FormatUnits(self.actual_amplification, ""),
            " <b>of spec:</b> ",
            DescriptionString.FormatUnits(self.amplification, ""),
        )

    @override
    def generate(self) -> None:
        super().generate()

        calculator = ESeriesRatioUtil(
            ESeriesUtil.SERIES[self.get(self.series)], self.get(self.tolerance), AmplifierValues
        )
        top_resistance, bottom_resistance = calculator.find(
            AmplifierValues(self.get(self.amplification), self.get(self.impedance))
        )

        self.amp = self.Block(Opamp())  # needed as forward reference for modeling
        self.r1 = self.Block(Resistor(Range.from_tolerance(top_resistance, self.get(self.tolerance))))
        self.r2 = self.Block(Resistor(Range.from_tolerance(bottom_resistance, self.get(self.tolerance))))

        if self.get(self.reference.is_connected()):
            reference_type: HasPassivePort = AnalogSink(impedance=self.r1.actual_resistance + self.r2.actual_resistance)
            reference_node: Port = self.reference
            reference_range = self.reference.link().signal
        else:
            reference_type = Ground()
            reference_node = self.gnd
            reference_range = self.gnd.link().voltage

        input_signal_range = self.amp.out.voltage.intersect(self.input.link().signal - reference_range)
        output_range = input_signal_range * self.actual_amplification + reference_range
        # TODO tolerances can cause the range to be much larger than actual, so bound it to avoid false-positives
        self.forced = self.Block(ForcedAnalogSignal(self.amp.out.signal.intersect(output_range)))

        self.import_kicad(
            self.file_path("resources", f"{self.__class__.__name__}.kicad_sch"),
            conversions={
                "r1.1": AnalogSink(impedance=self.r1.actual_resistance + self.r2.actual_resistance),
                "r1.2": AnalogSource(  # this models the entire node
                    voltage=self.amp.out.voltage,
                    impedance=1 / (1 / self.r1.actual_resistance + 1 / self.r2.actual_resistance),
                ),
                "r2.1": AnalogSink(),  # ideal
                "r2.2": reference_type,
            },
            nodes={"ref": reference_node},
        )

        self.assign(self.actual_amplification, 1 + (self.r1.actual_resistance / self.r2.actual_resistance))


class DifferentialValues(ESeriesRatioValue["DifferentialValues"]):
    def __init__(self, ratio: Range, input_impedance: Range):
        self.ratio = ratio  # ratio from difference between inputs to output
        self.input_impedance = input_impedance  # resistance of the input resistor

    @staticmethod
    @override
    def from_resistors(r1_range: Range, r2_range: Range) -> "DifferentialValues":
        """r1 is the input side resistance and r2 is the feedback or ground resistor."""
        return DifferentialValues((r2_range / r1_range), r1_range)

    @override
    def initial_test_decades(self) -> Tuple[int, int]:
        r1_decade = ceil(log10(self.input_impedance.center()))
        r2_decade = ceil(log10((self.input_impedance * self.ratio).center()))
        return r1_decade, r2_decade

    @override
    def distance_to(self, spec: "DifferentialValues") -> List[float]:
        if self.ratio in spec.ratio and self.input_impedance in spec.input_impedance:
            return []
        else:
            return [
                abs(self.ratio.center() - spec.ratio.center()),
                abs(self.input_impedance.center() - spec.input_impedance.center()),
            ]

    @override
    def intersects(self, spec: "DifferentialValues") -> bool:
        return self.ratio.intersects(spec.ratio) and self.input_impedance.intersects(spec.input_impedance)
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
